astir13/SoftRF/documents/images/ForeFlight-1.jpg

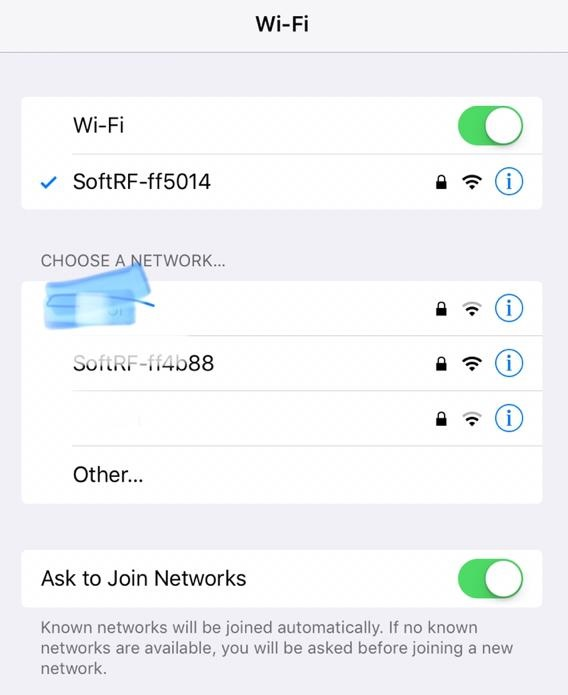
documents/images/ForeFlight-1.jpg
