astir13/SoftRF/documents/images/ForeFlight-2.jpg

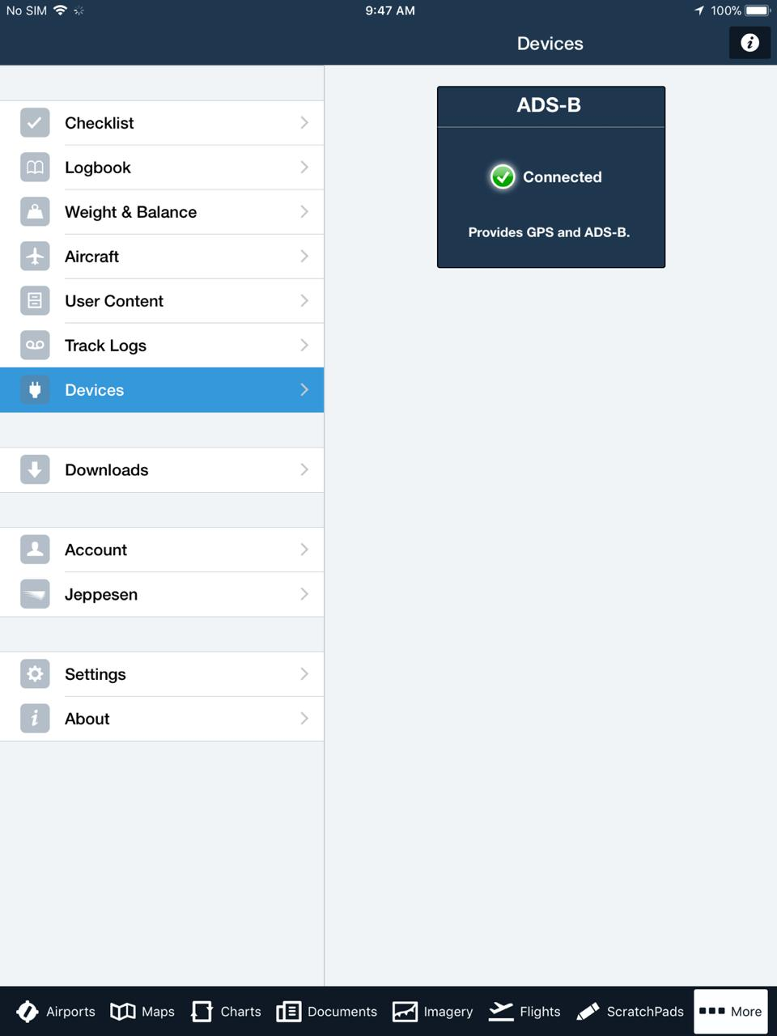
documents/images/ForeFlight-2.jpg
