astir13/SoftRF/documents/images/ForeFlight-3.jpg

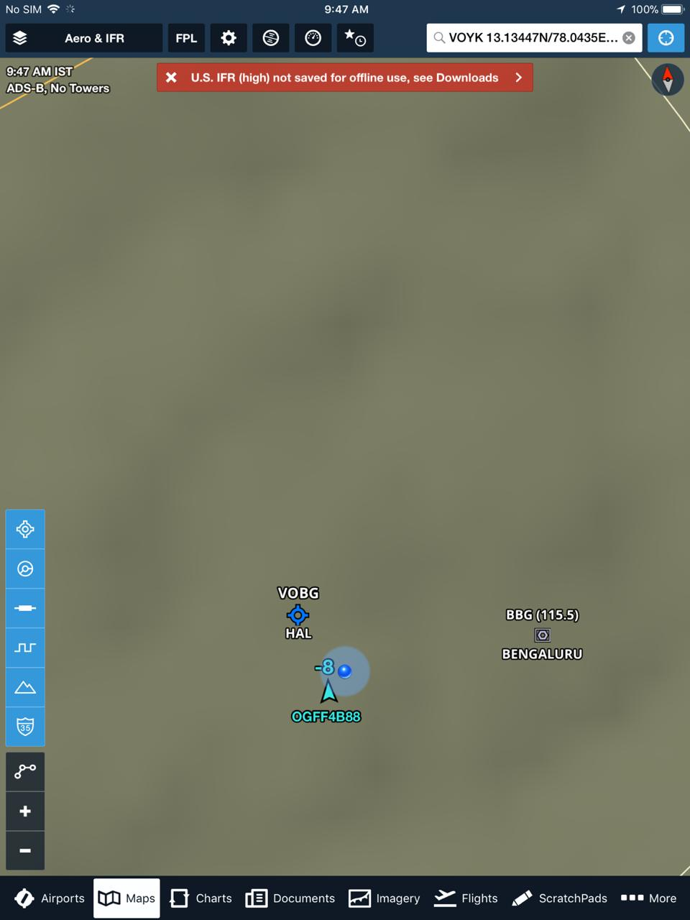
documents/images/ForeFlight-3.jpg
