astir13/SoftRF/documents/images/iLogger-boot.jpg

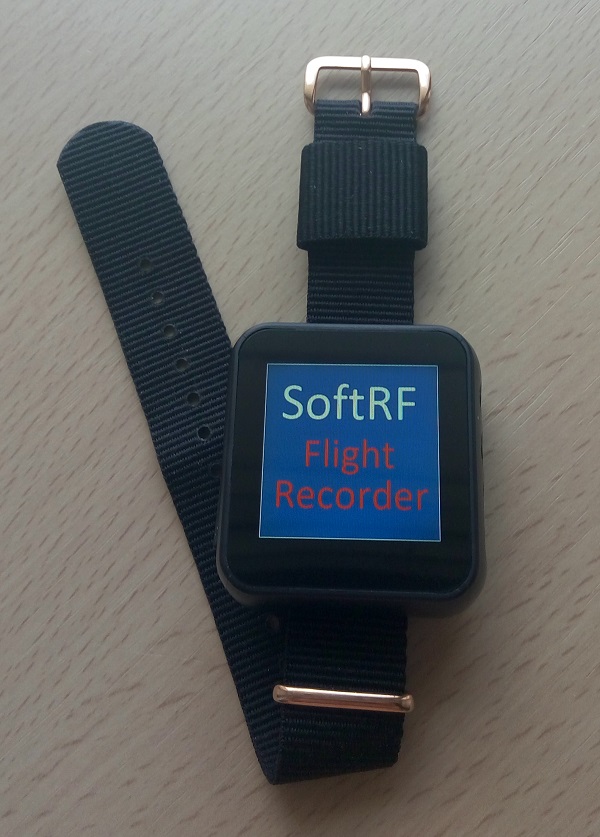
documents/images/iLogger-boot.jpg
