astir13/SoftRF/documents/images/iLogger-DIY.jpg

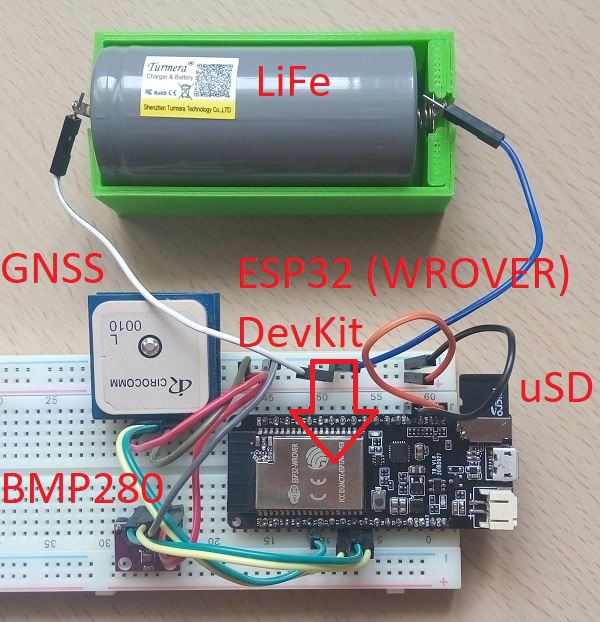
documents/images/iLogger-DIY.jpg
