astir13/SoftRF/documents/images/iLogger-flashing.jpg

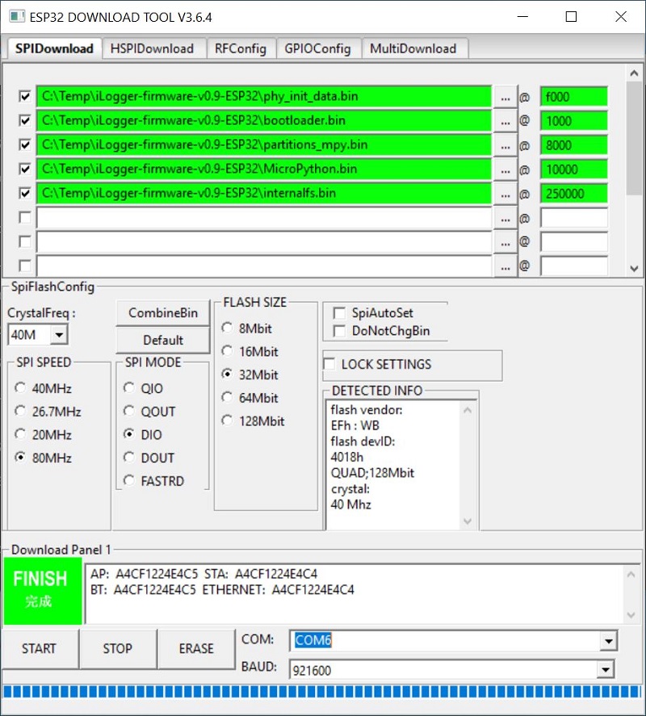
documents/images/iLogger-flashing.jpg
