astir13/SoftRF/documents/images/iLogger-I2C.jpg

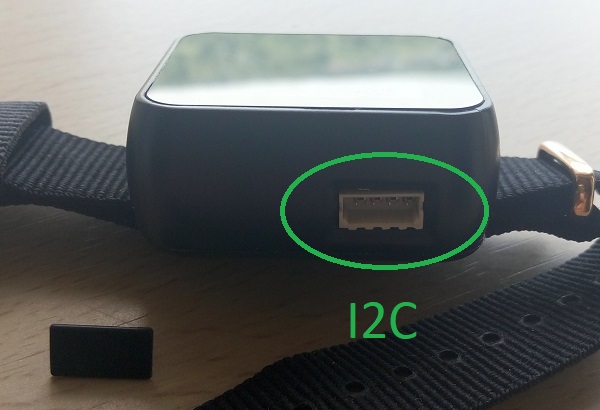
documents/images/iLogger-I2C.jpg
