astir13/SoftRF/documents/images/iLogger-nocard.jpg

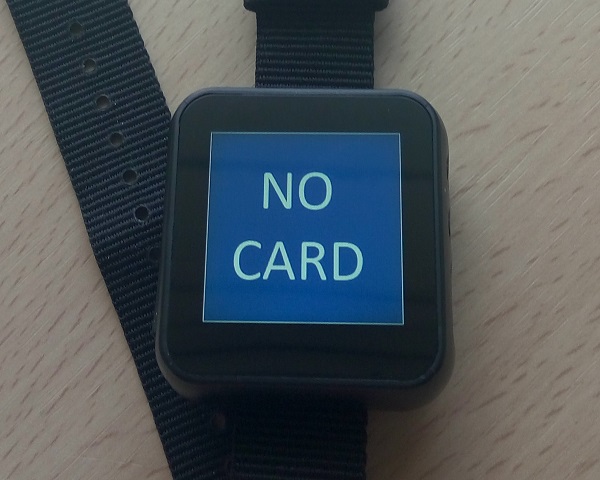
documents/images/iLogger-nocard.jpg
