astir13/SoftRF/documents/images/iLogger-nofix.jpg

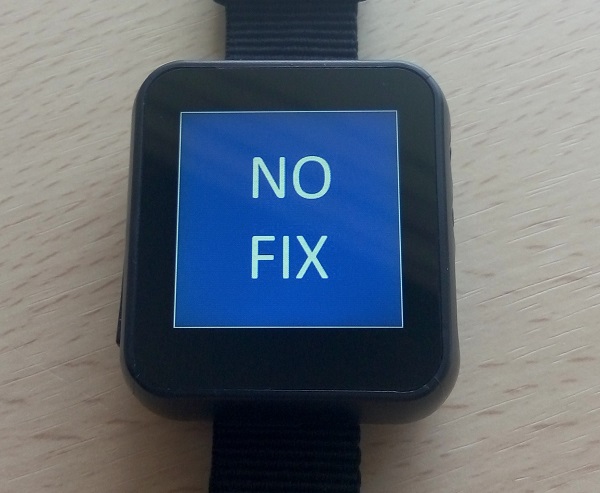
documents/images/iLogger-nofix.jpg
