astir13/SoftRF/documents/images/iLogger-off.jpg

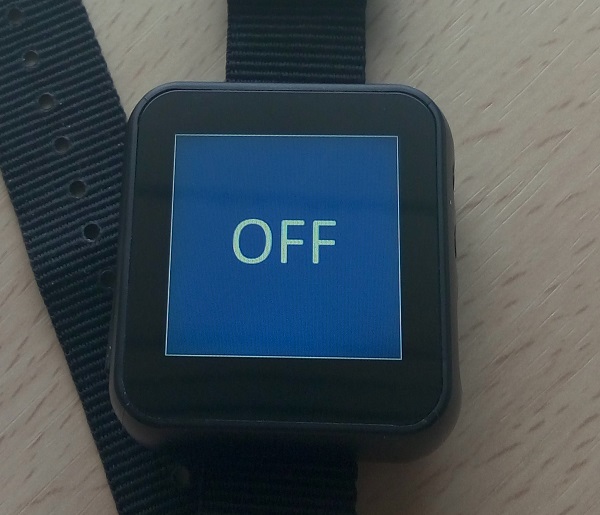
documents/images/iLogger-off.jpg
