astir13/SoftRF/documents/images/iLogger-SeeYou.JPG

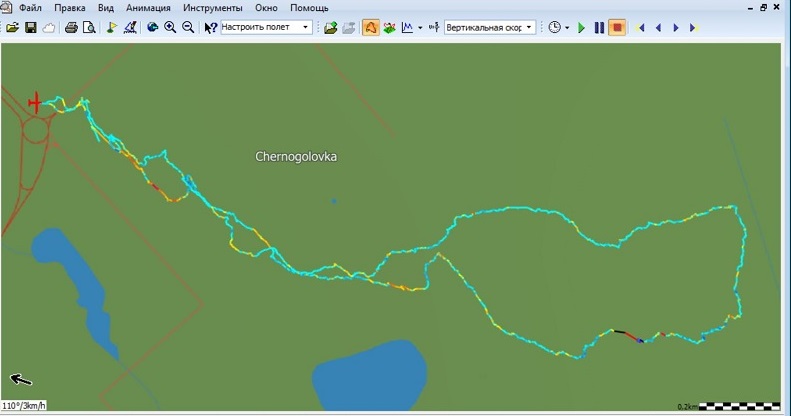
documents/images/iLogger-SeeYou.JPG
