astir13/SoftRF/documents/images/instrument-panel-1.jpg

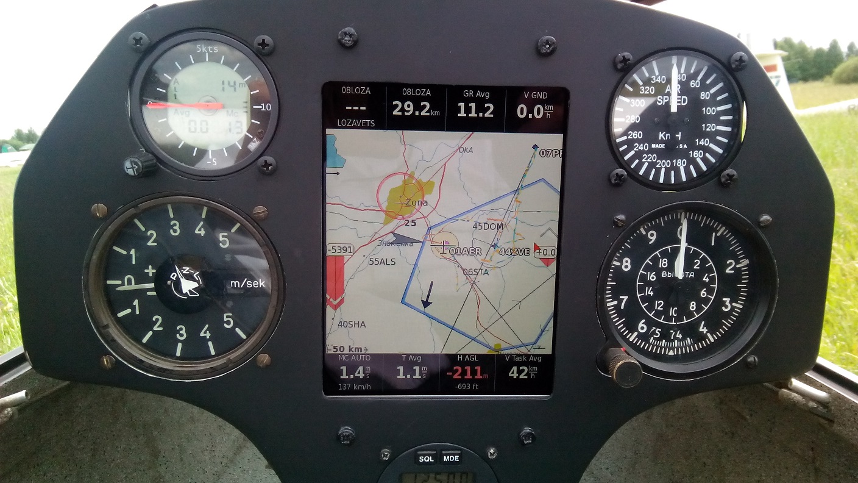
documents/images/instrument-panel-1.jpg
