astir13/SoftRF/documents/images/PE2_QS_p1.jpg

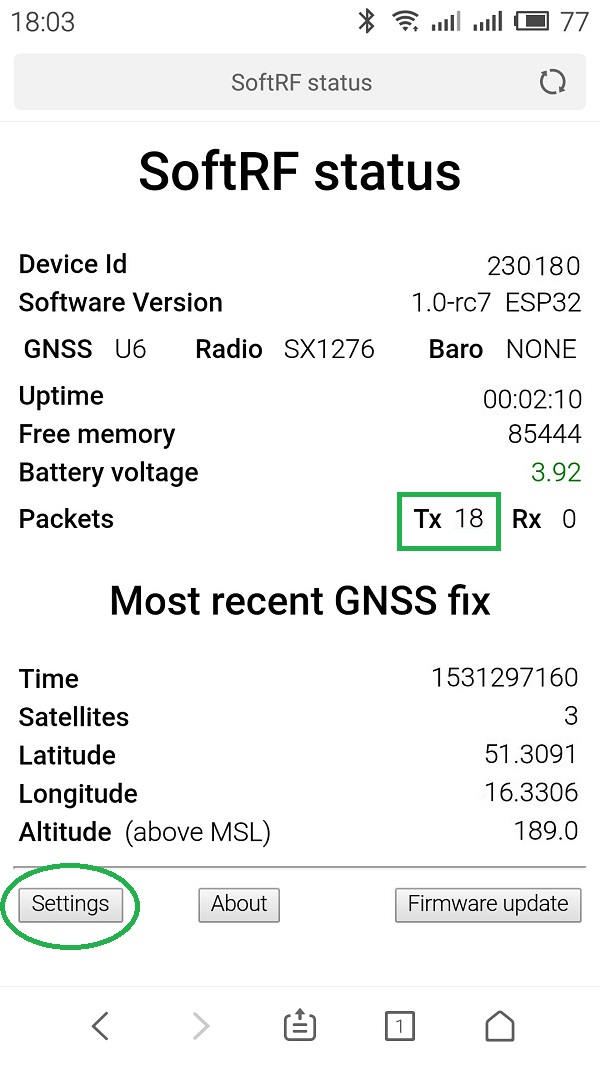
documents/images/PE2_QS_p1.jpg
