astir13/SoftRF/documents/images/PE2_QS_p2.jpg

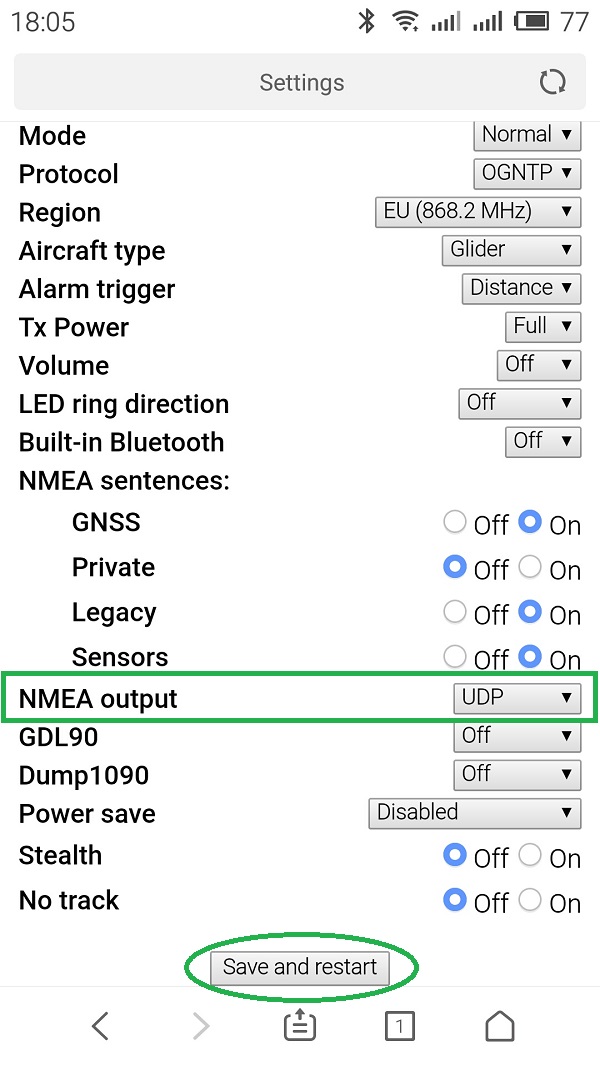
documents/images/PE2_QS_p2.jpg
