astir13/SoftRF/documents/images/Prime2_T22_V10_1.jpg

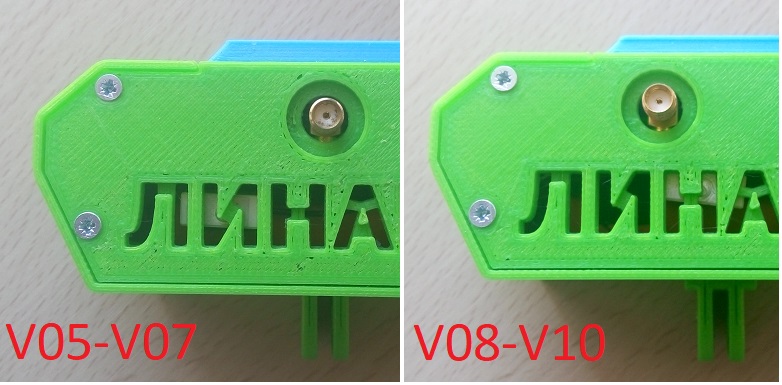
documents/images/Prime2_T22_V10_1.jpg
