astir13/SoftRF/documents/images/RPI_SPI.jpg

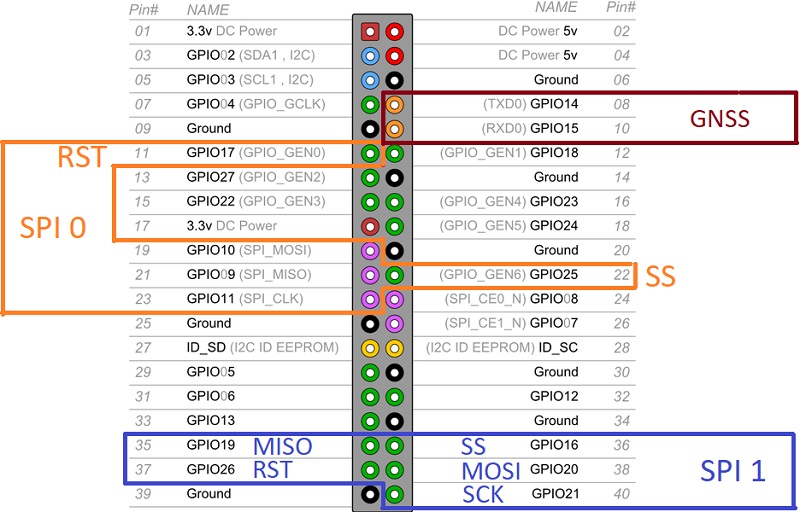
documents/images/RPI_SPI.jpg
