astir13/SoftRF/documents/images/skyview-1-t5s.jpg

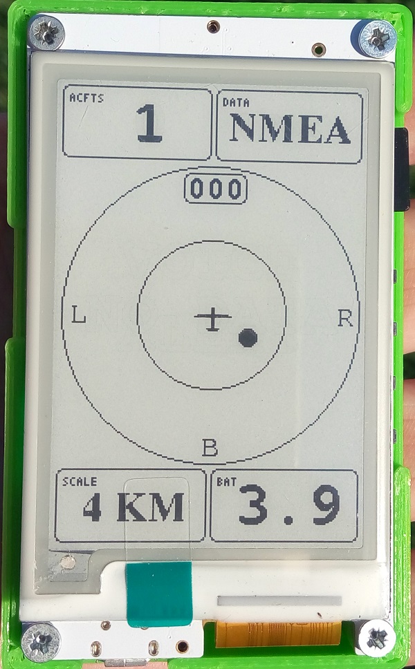
documents/images/skyview-1-t5s.jpg
