astir13/SoftRF/documents/images/skyview-1.jpg

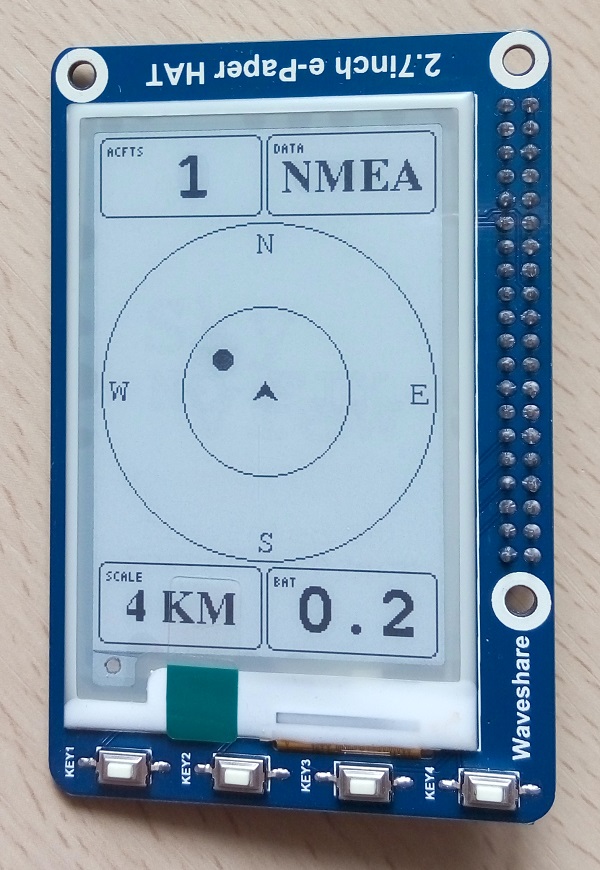
documents/images/skyview-1.jpg
