astir13/SoftRF/documents/images/skyview-2.jpg

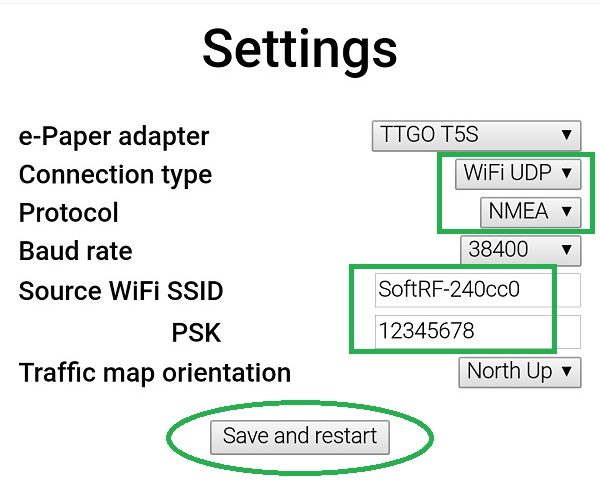
documents/images/skyview-2.jpg
