astir13/SoftRF/documents/images/skyview-3-t5s.jpg

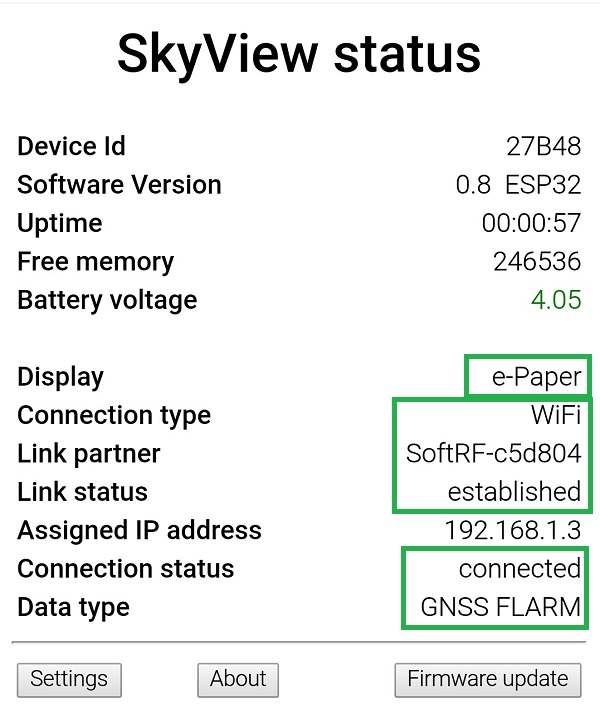
documents/images/skyview-3-t5s.jpg
