astir13/SoftRF/documents/images/skyview-3.jpg

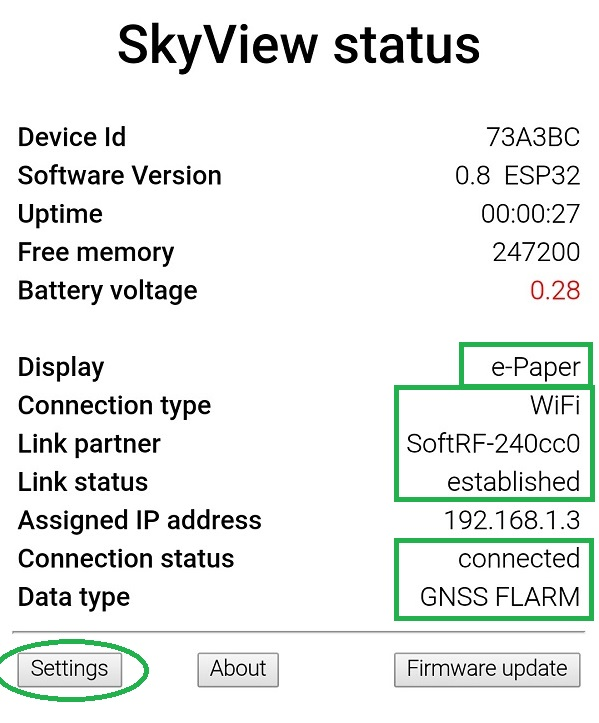
documents/images/skyview-3.jpg
