astir13/SoftRF/documents/images/skyview-4.jpg

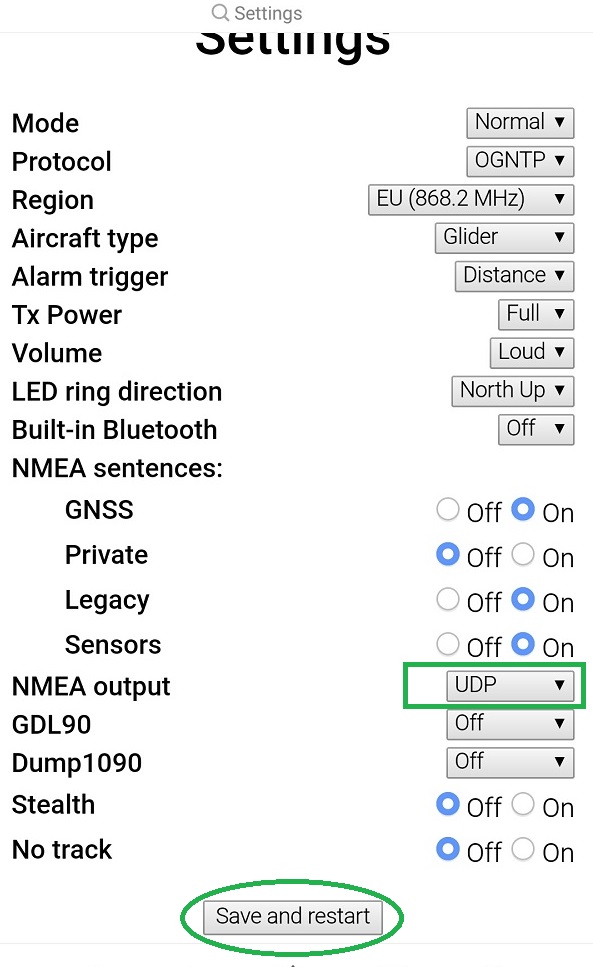
documents/images/skyview-4.jpg
