astir13/SoftRF/documents/images/skyview-5-t5s.jpg

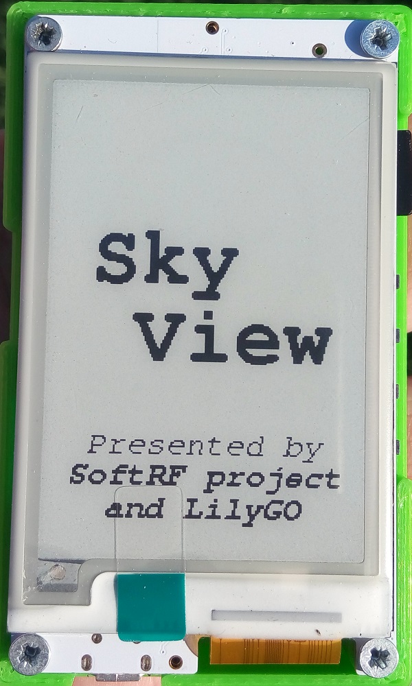
documents/images/skyview-5-t5s.jpg
