astir13/SoftRF/documents/images/skyview-5.jpg

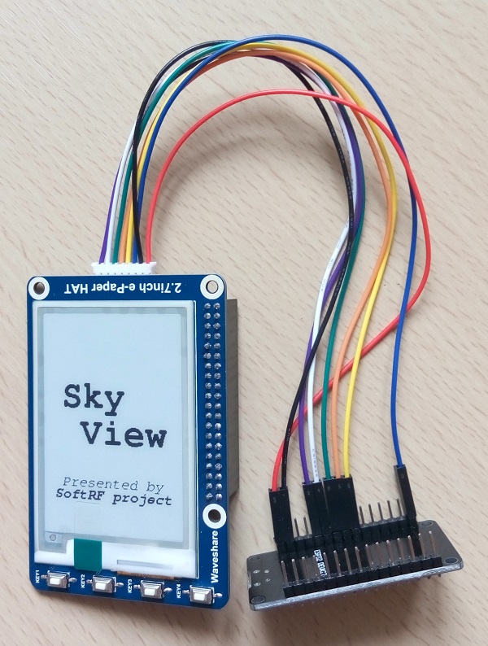
documents/images/skyview-5.jpg
