astir13/SoftRF/documents/images/skyview-7-no-traffic-t5s.jpg

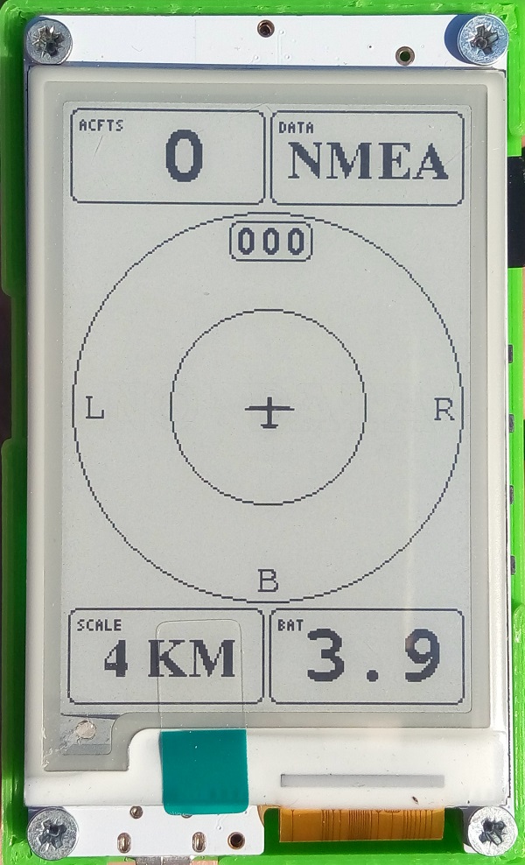
documents/images/skyview-7-no-traffic-t5s.jpg
