astir13/SoftRF/documents/images/skyview-8-no-data-t5s.jpg

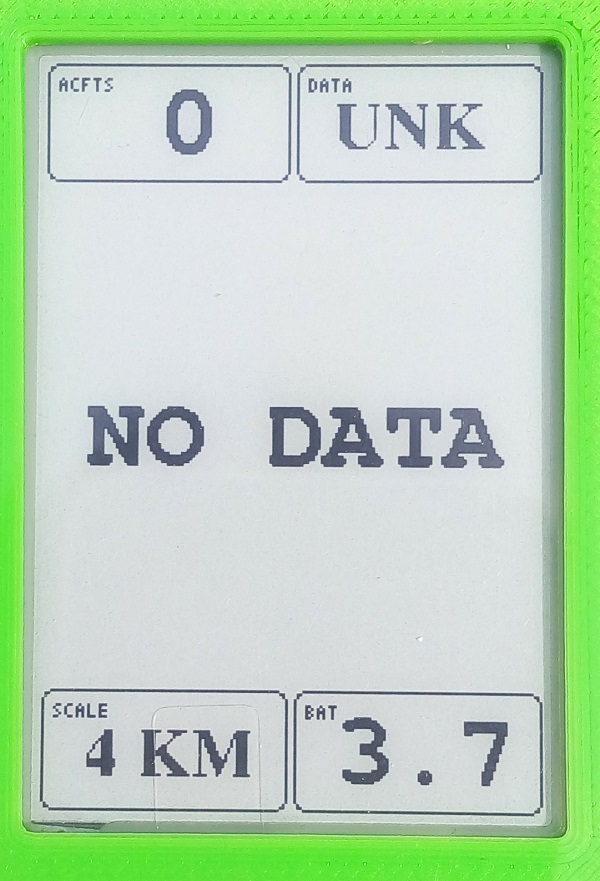
documents/images/skyview-8-no-data-t5s.jpg
