astir13/SoftRF/documents/images/skyview-8-no-data.jpg

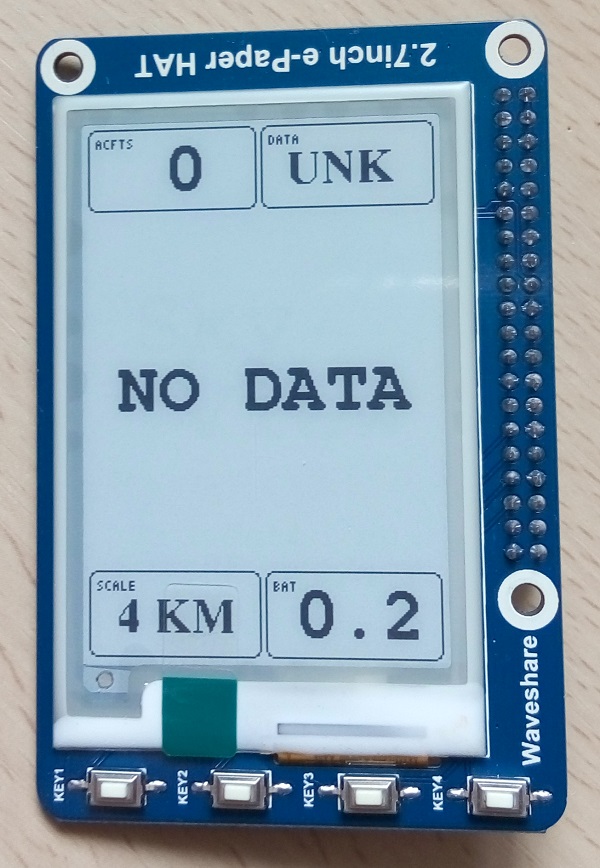
documents/images/skyview-8-no-data.jpg
