astir13/SoftRF/documents/images/skyview-9.JPG

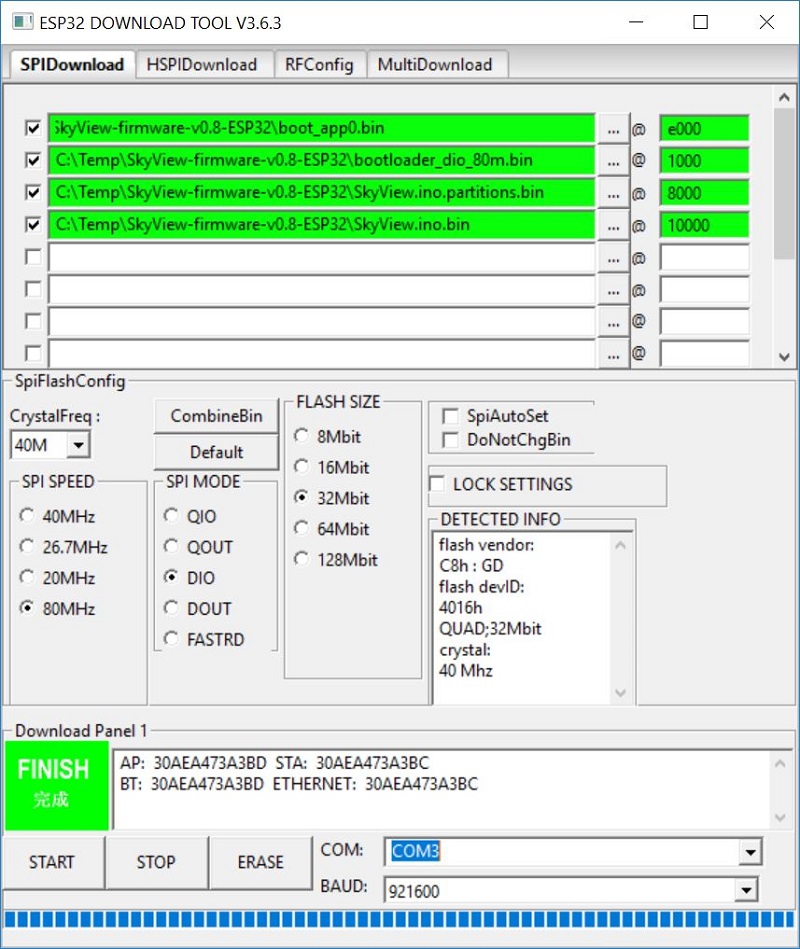
documents/images/skyview-9.JPG
