astir13/SoftRF/documents/images/skyview-10.jpg

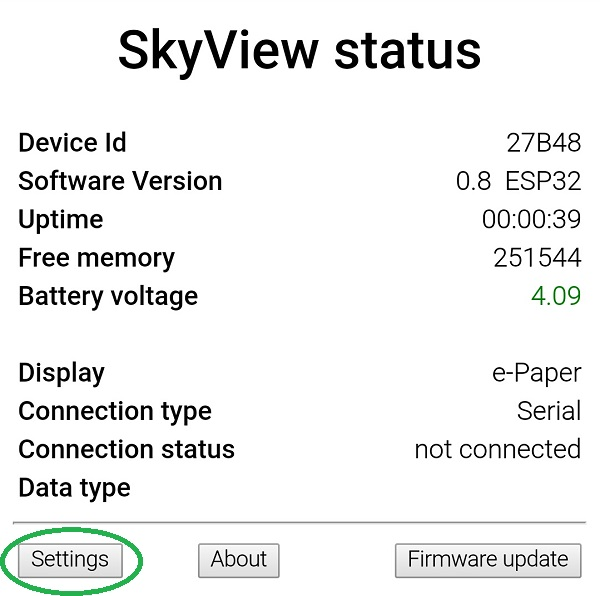
documents/images/skyview-10.jpg
