astir13/SoftRF/documents/images/skyview-12.jpg

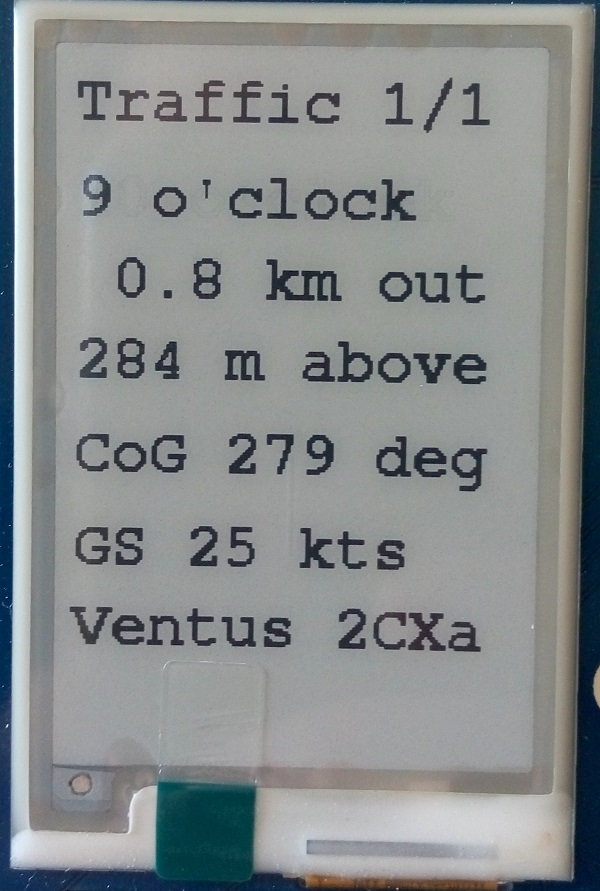
documents/images/skyview-12.jpg
