astir13/SoftRF/documents/images/skyview-14.jpg

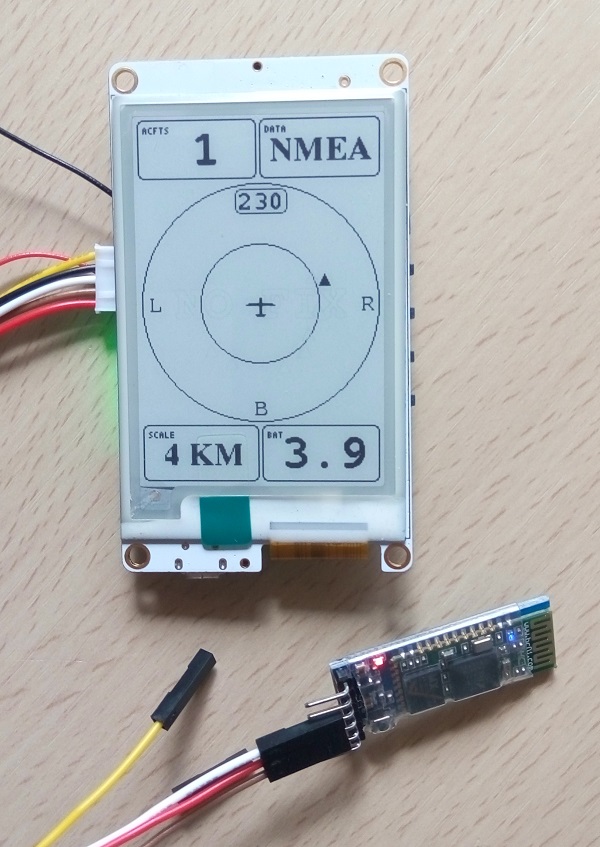
documents/images/skyview-14.jpg
