astir13/SoftRF/documents/images/skyview-15.JPG

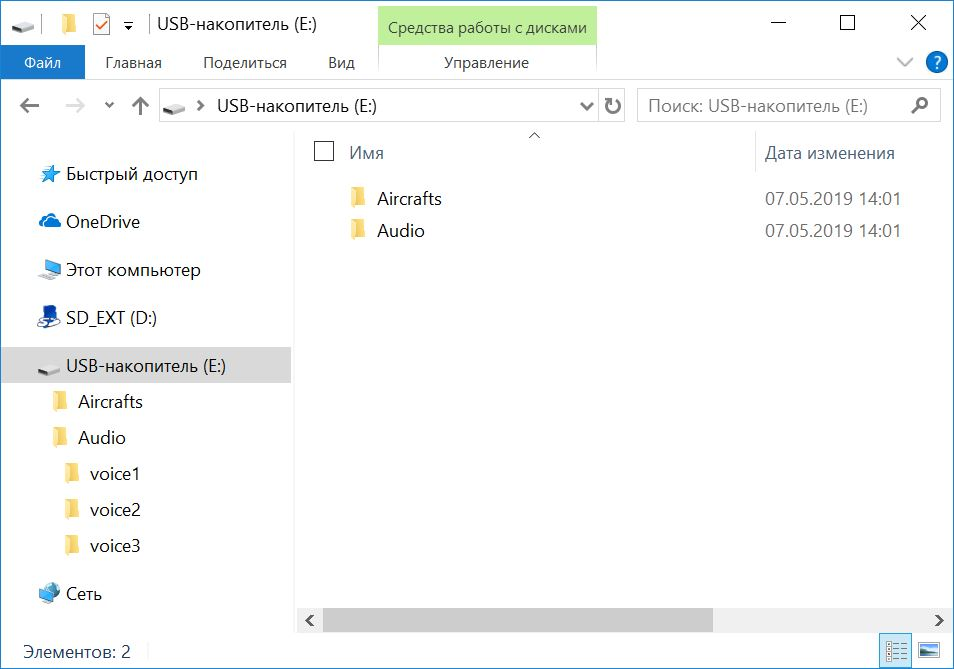
documents/images/skyview-15.JPG
