astir13/SoftRF/documents/images/skyview-16-ePaper-vs-OLED.jpg

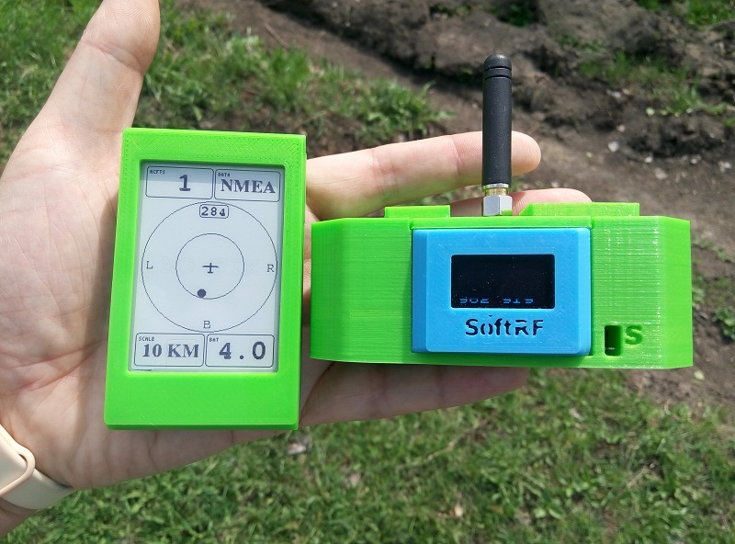
documents/images/skyview-16-ePaper-vs-OLED.jpg
