astir13/SoftRF/documents/images/skyview-17.jpg

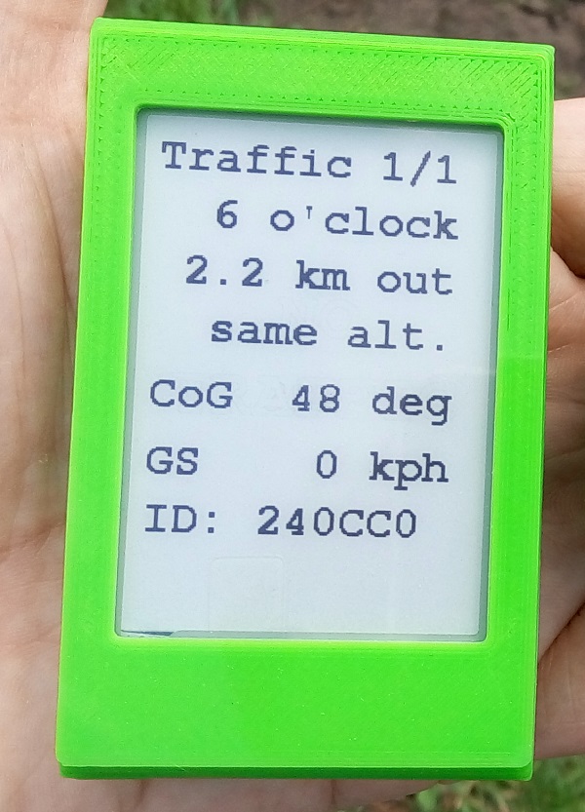
documents/images/skyview-17.jpg
