astir13/SoftRF/documents/images/skyview-18.jpg

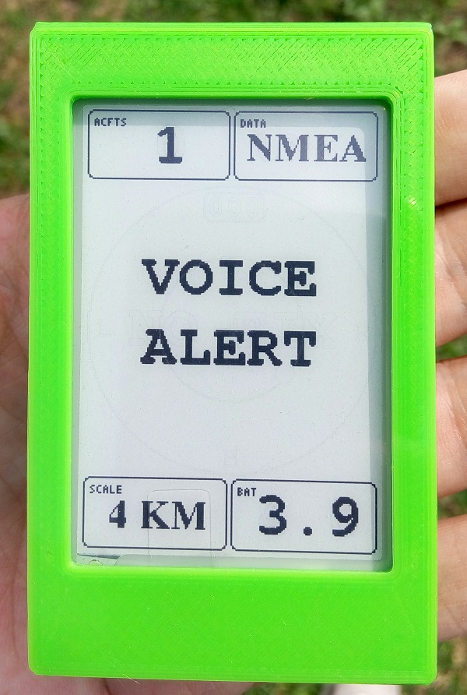
documents/images/skyview-18.jpg
