astir13/SoftRF/documents/images/skyview-19-buttons.jpg

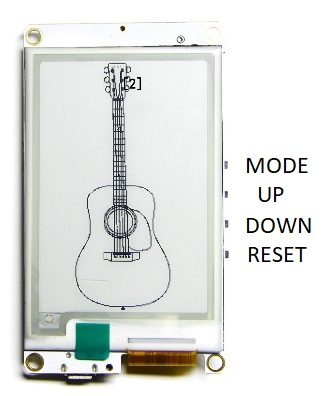
documents/images/skyview-19-buttons.jpg
