astir13/SoftRF/documents/images/skyview-20-serial.jpg

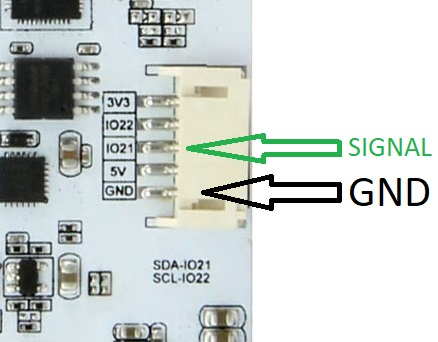
documents/images/skyview-20-serial.jpg
