astir13/SoftRF/documents/images/skyview-21-speaker.jpg

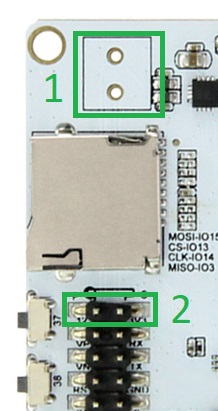
documents/images/skyview-21-speaker.jpg
