astir13/SoftRF/documents/images/skyview-22-enclosure.jpg

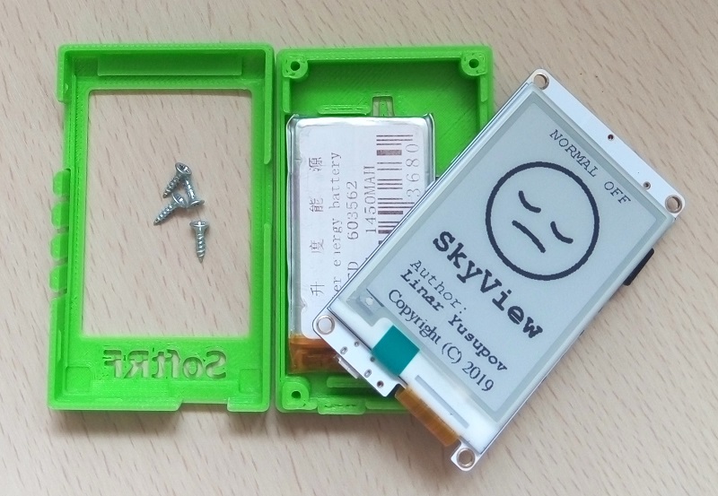
documents/images/skyview-22-enclosure.jpg
