astir13/SoftRF/documents/images/skyview-23-enclosure.jpg

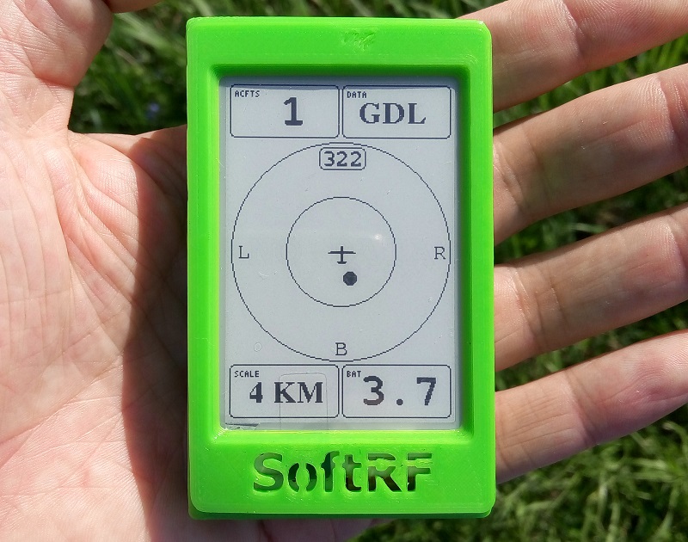
documents/images/skyview-23-enclosure.jpg
