astir13/SoftRF/documents/images/skyview-24.jpg

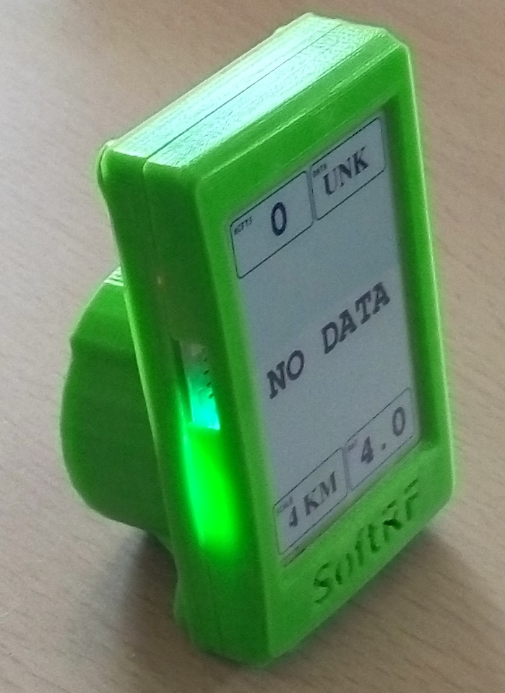
documents/images/skyview-24.jpg
