astir13/SoftRF/documents/images/skyview-25.jpg

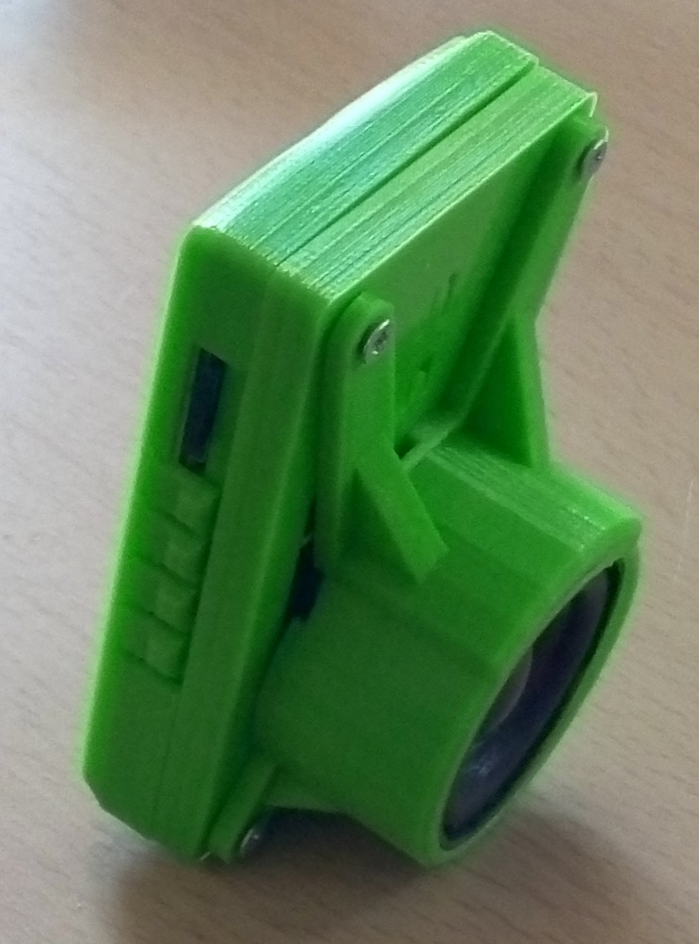
documents/images/skyview-25.jpg
