astir13/SoftRF/documents/images/skyview-26.jpg

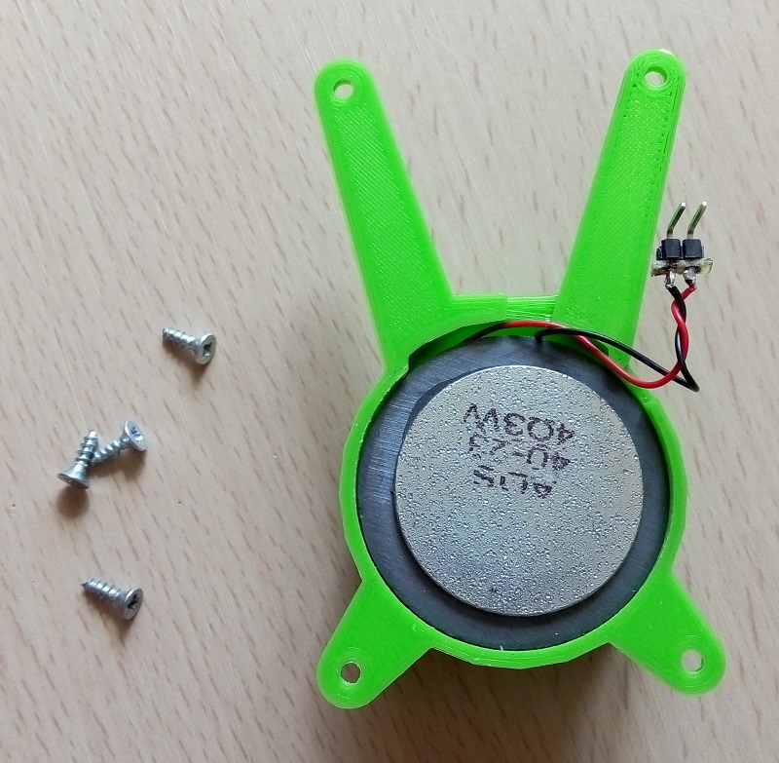
documents/images/skyview-26.jpg
