astir13/SoftRF/documents/images/skyview-27-holder.jpg

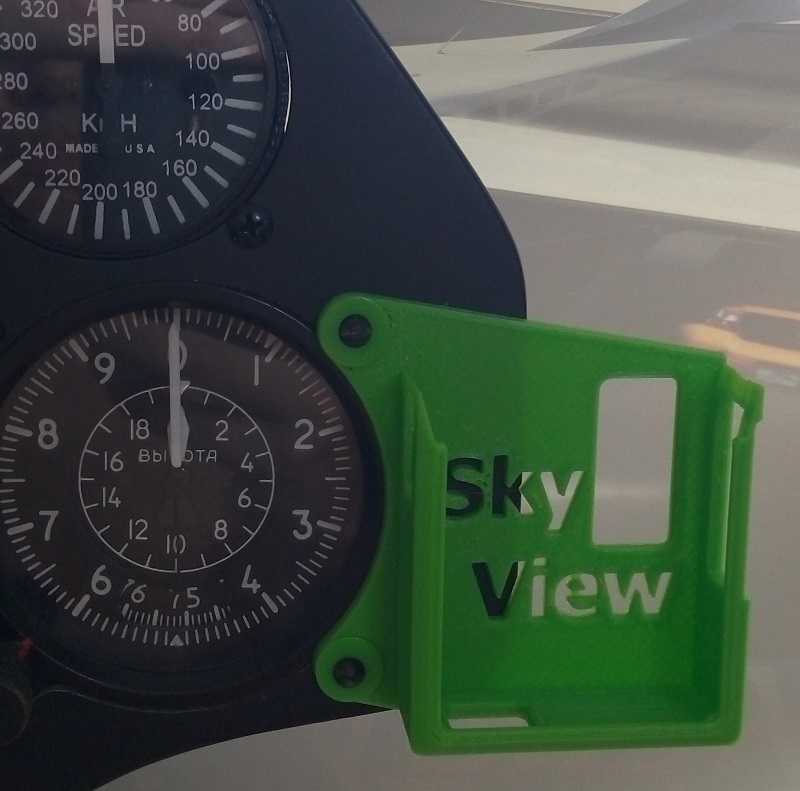
documents/images/skyview-27-holder.jpg
