astir13/SoftRF/documents/images/skyview-28.jpg

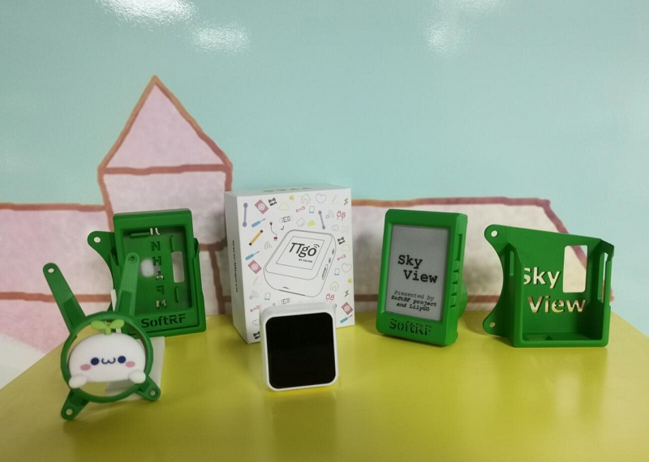
documents/images/skyview-28.jpg
