astir13/SoftRF/documents/images/skyview-29-holder.jpg

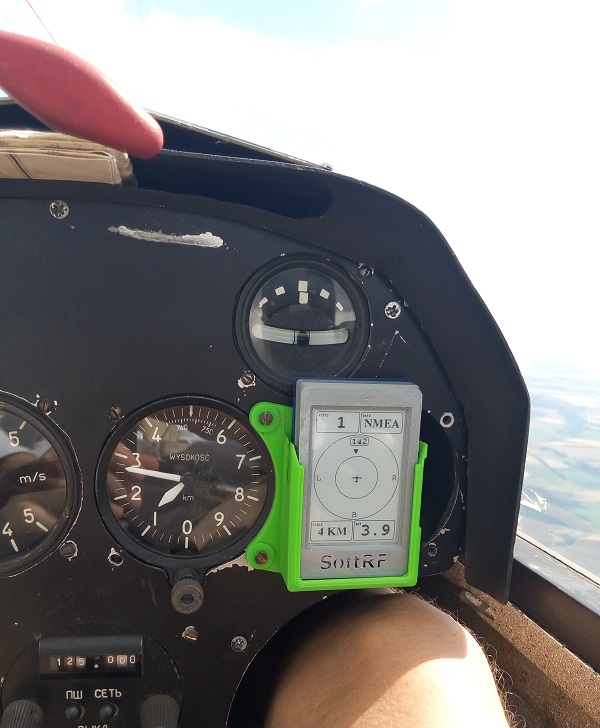
documents/images/skyview-29-holder.jpg
