astir13/SoftRF/documents/images/skyview-30-distance.jpg

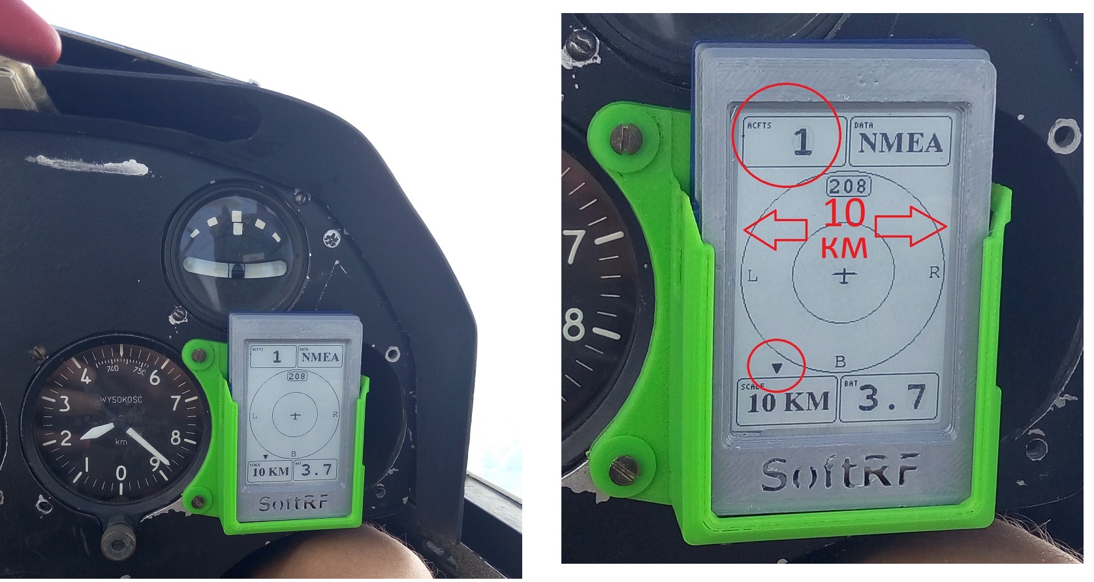
documents/images/skyview-30-distance.jpg
