astir13/SoftRF/documents/images/skyview-34.jpg

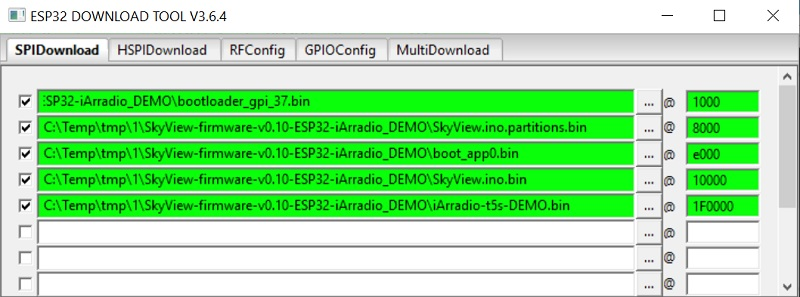
documents/images/skyview-34.jpg
