astir13/SoftRF/documents/images/skywatch-2.jpg

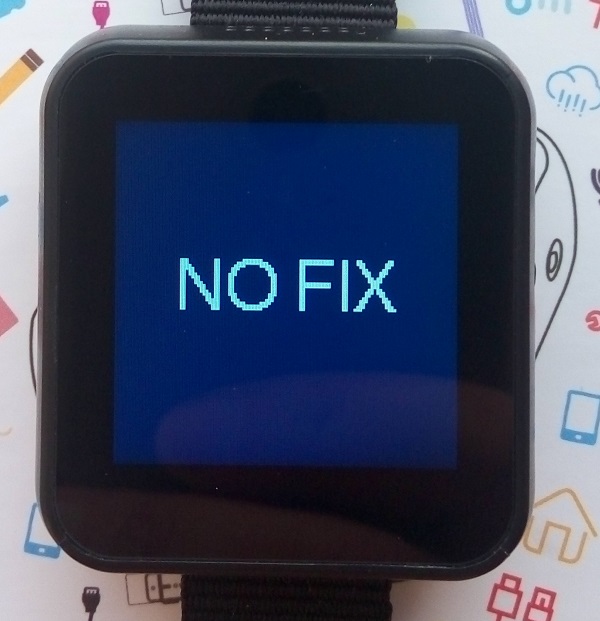
documents/images/skywatch-2.jpg
