astir13/SoftRF/documents/images/skywatch-3.jpg

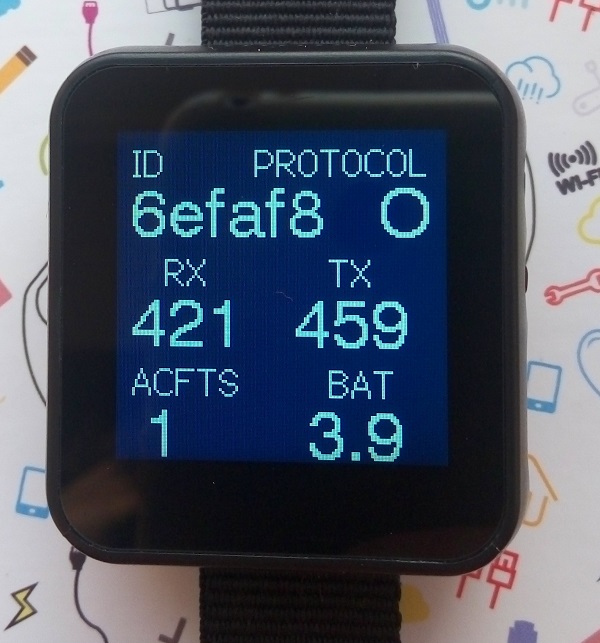
documents/images/skywatch-3.jpg
