astir13/SoftRF/documents/images/skywatch-5.jpg

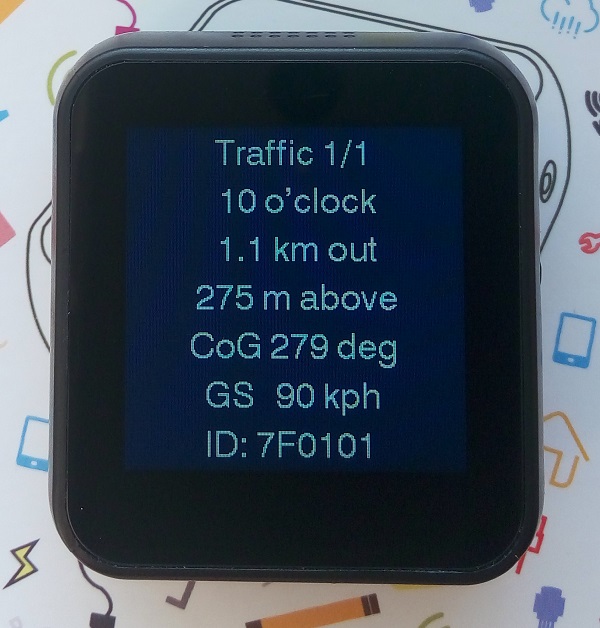
documents/images/skywatch-5.jpg
