astir13/SoftRF/documents/images/skywatch-6.jpg

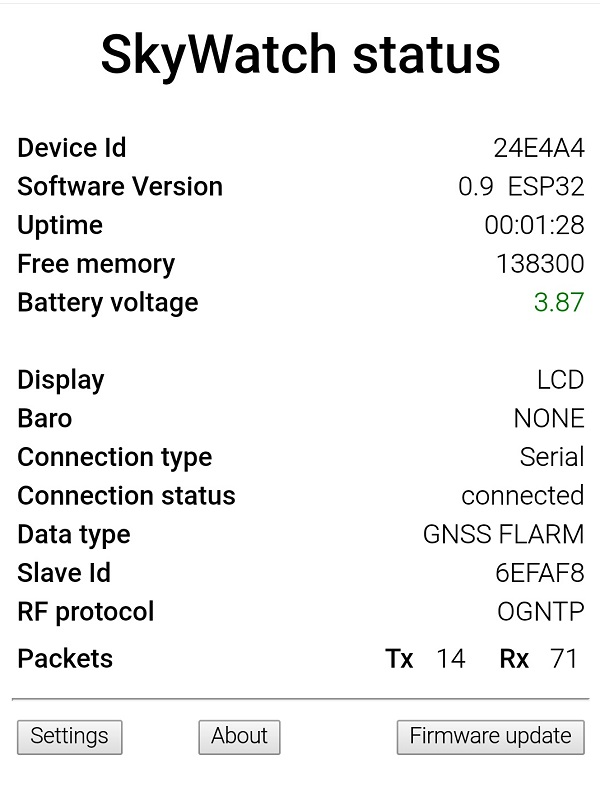
documents/images/skywatch-6.jpg
