astir13/SoftRF/documents/images/SoftRF-UAT-1.jpg

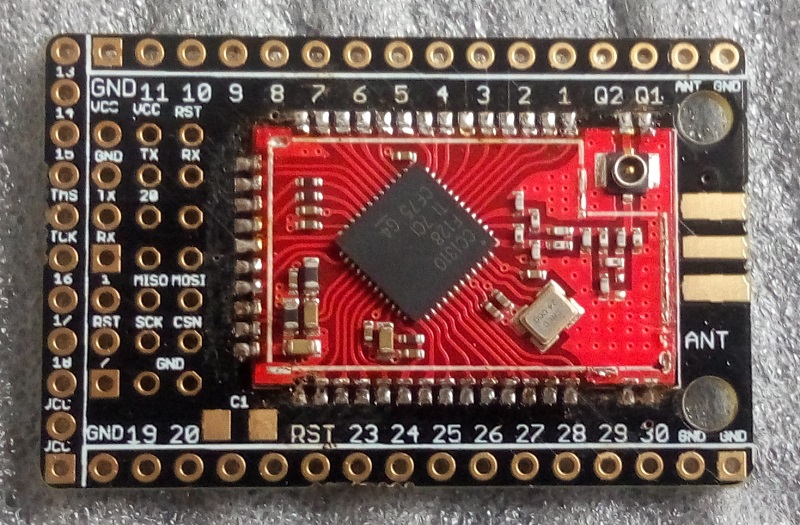
documents/images/SoftRF-UAT-1.jpg
