astir13/SoftRF/documents/images/stm32_breadboard.jpg

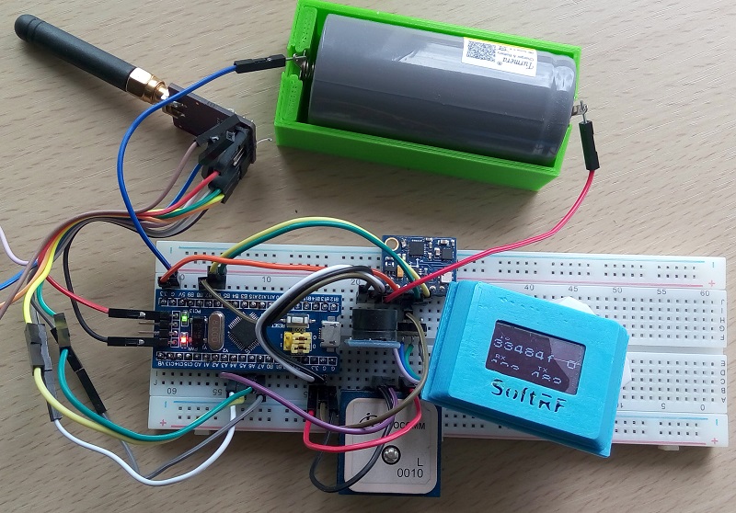
documents/images/stm32_breadboard.jpg
