astir13/SoftRF/documents/images/stm32_rfm69.jpg

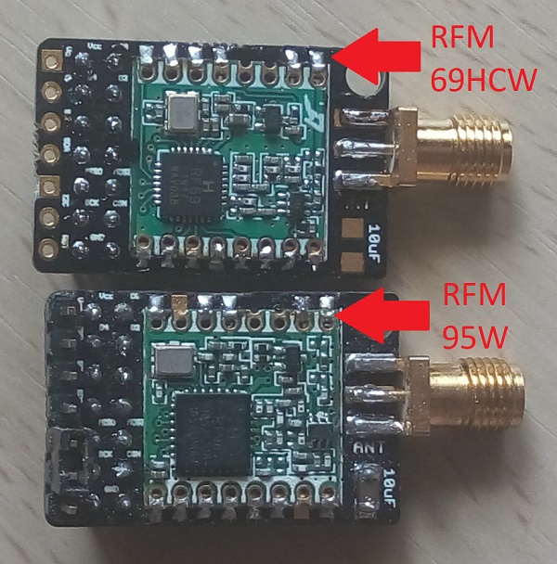
documents/images/stm32_rfm69.jpg
