astir13/SoftRF/documents/images/t-motion-7.jpg

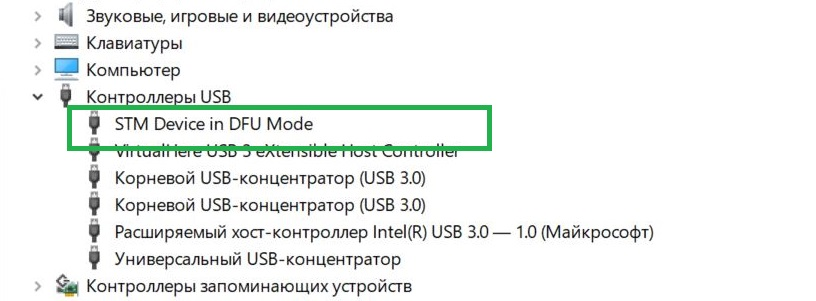
documents/images/t-motion-7.jpg
