astir13/SoftRF/documents/images/t-motion-10.jpg

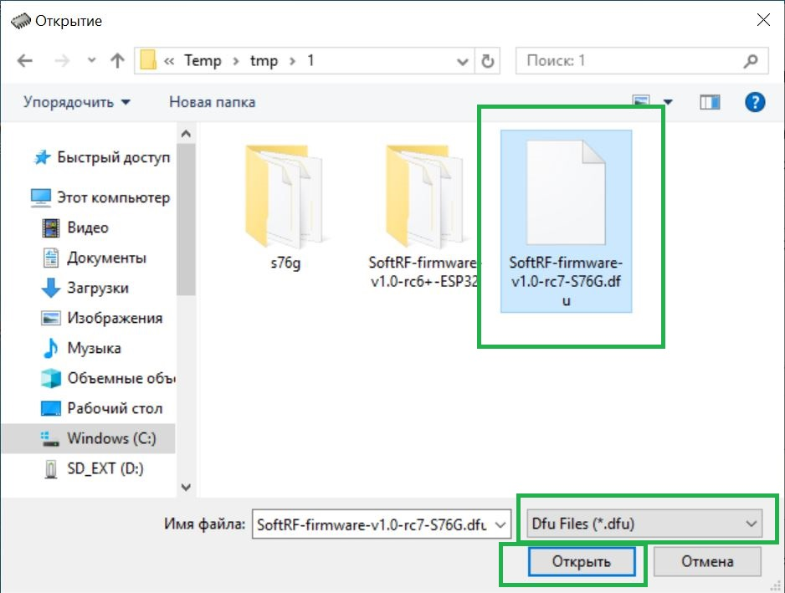
documents/images/t-motion-10.jpg
