astir13/SoftRF/documents/images/t-motion-12.jpg

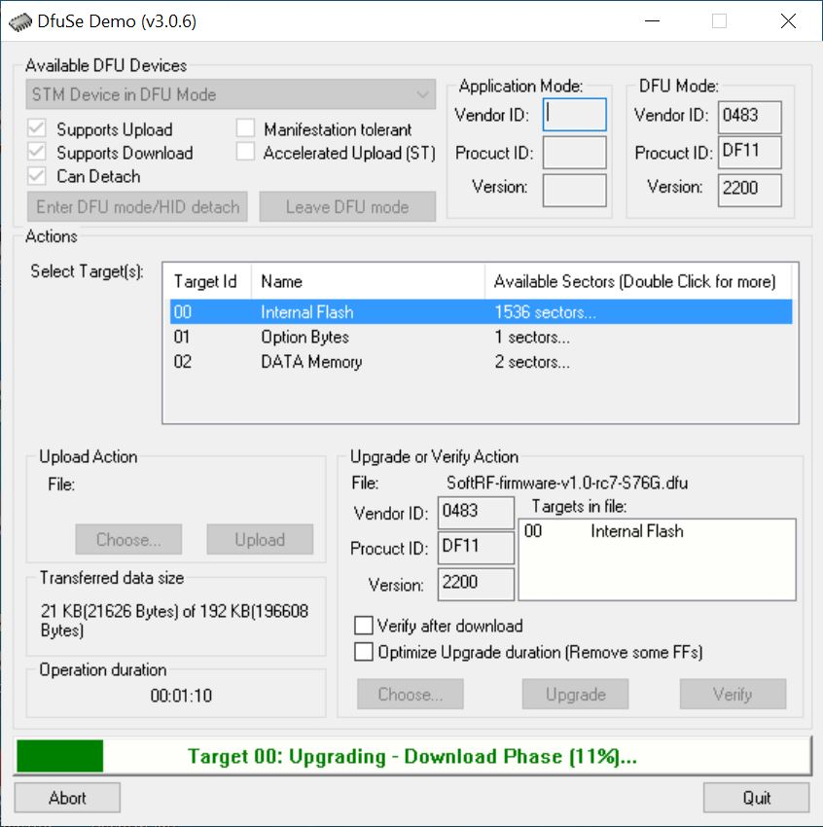
documents/images/t-motion-12.jpg
