astir13/SoftRF/documents/images/t-motion-13.jpg

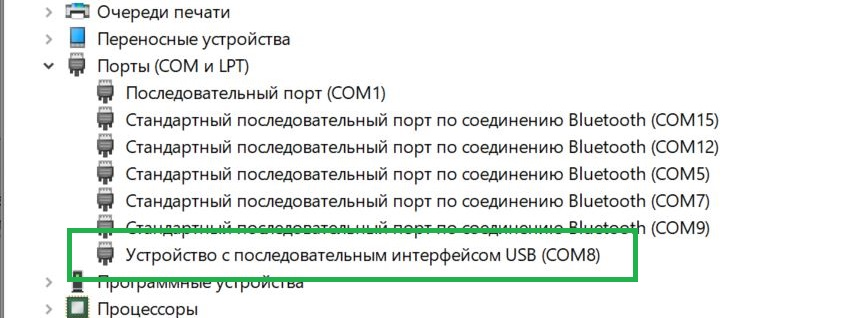
documents/images/t-motion-13.jpg
