astir13/SoftRF/documents/images/t-motion-14.jpg

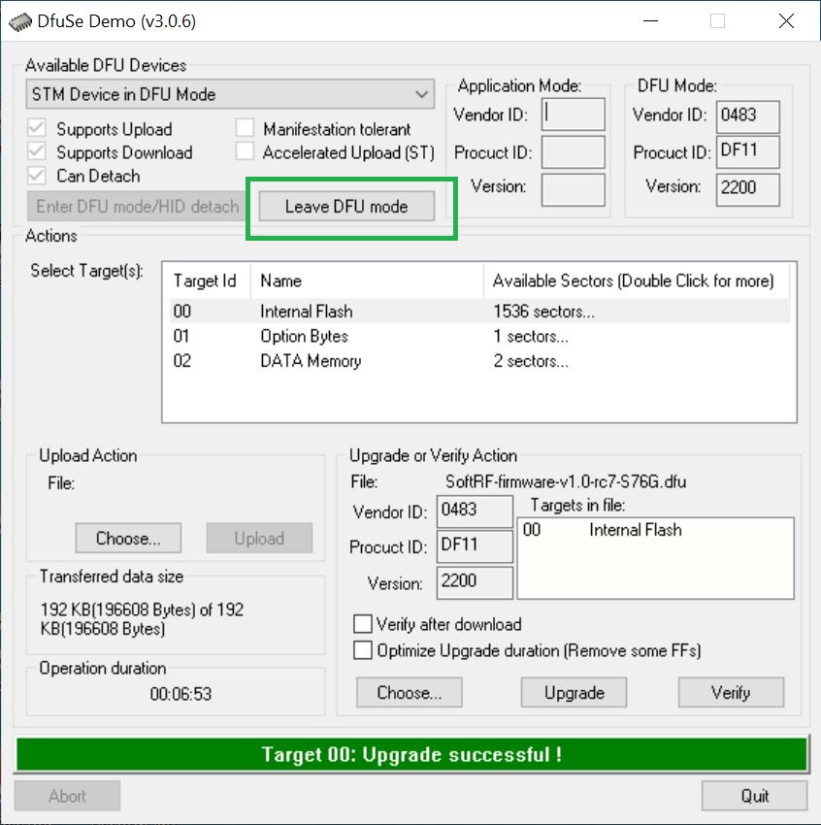
documents/images/t-motion-14.jpg
