astir13/SoftRF/documents/images/t-motion-16.jpg

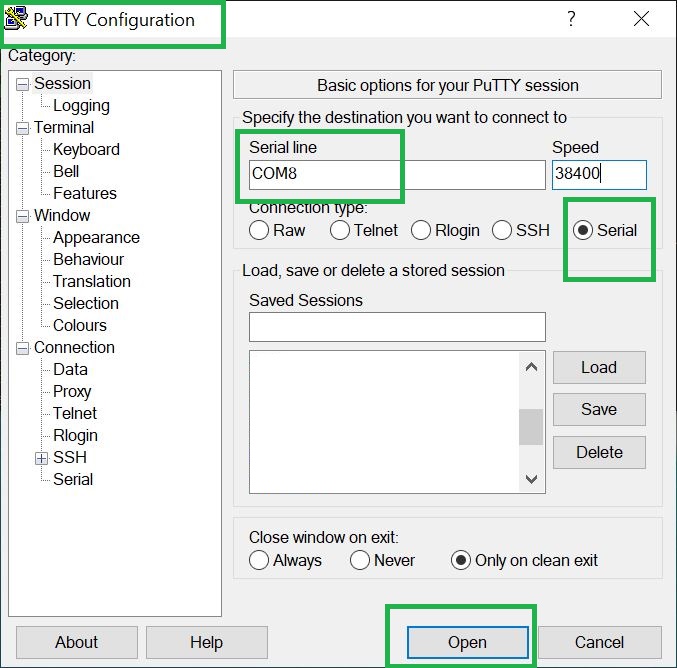
documents/images/t-motion-16.jpg
