astir13/SoftRF/documents/images/t-motion-17.jpg

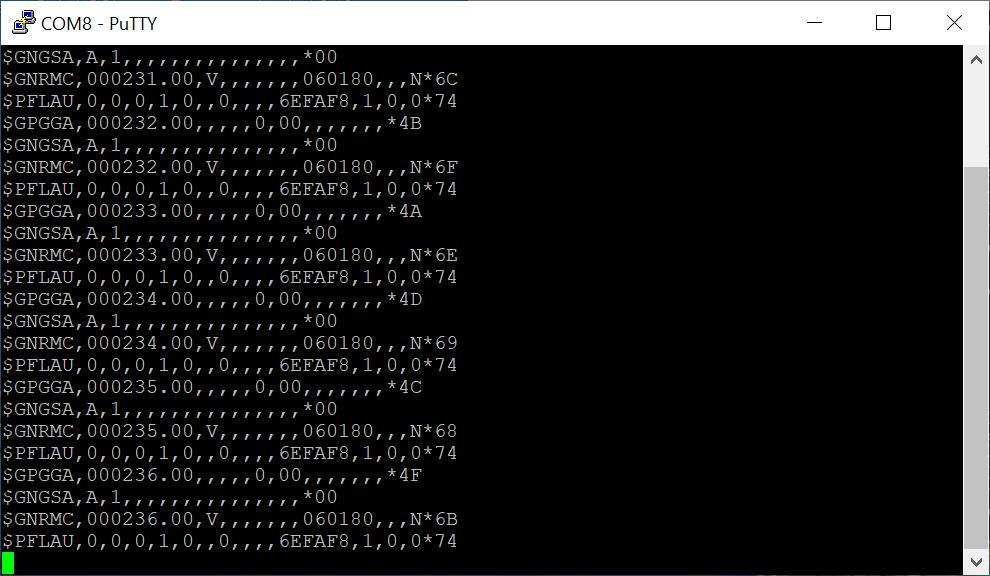
documents/images/t-motion-17.jpg
