astir13/SoftRF/documents/images/t-motion-18.jpg

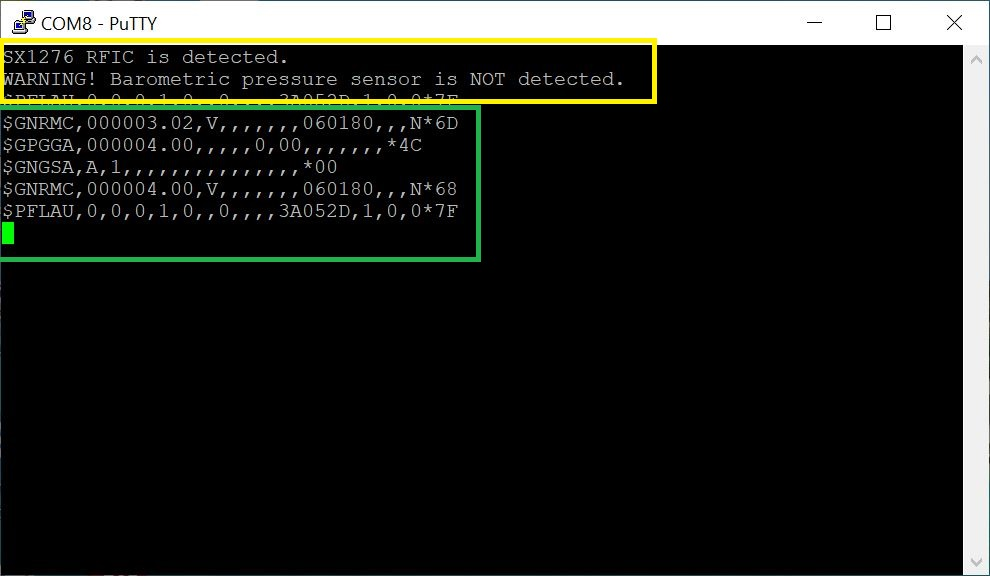
documents/images/t-motion-18.jpg
