astir13/SoftRF/documents/images/t-motion-20.jpg

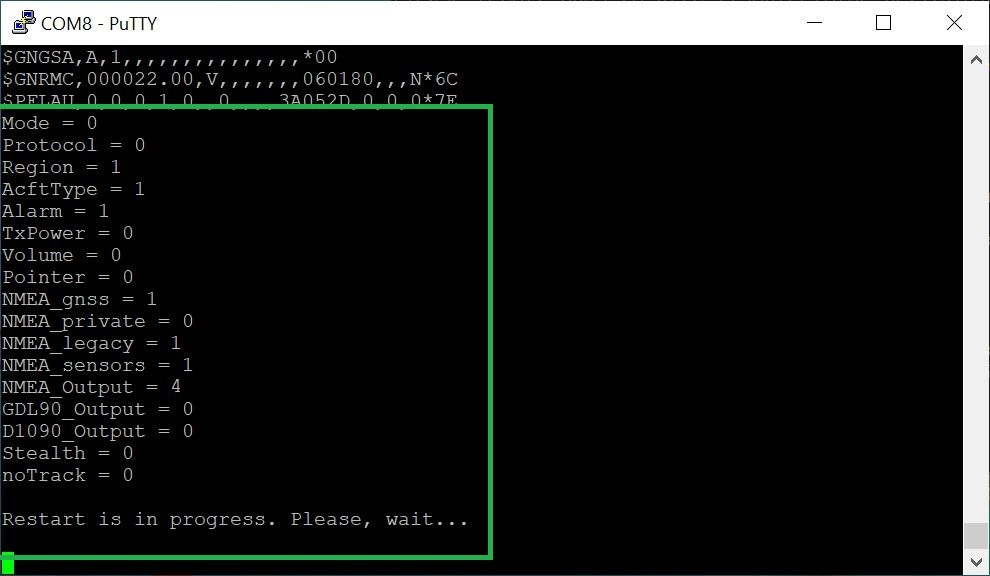
documents/images/t-motion-20.jpg
