astir13/SoftRF/documents/images/t-motion-21.jpg

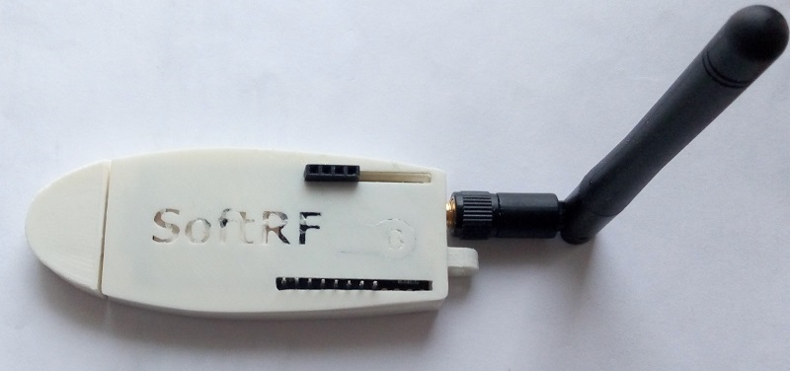
documents/images/t-motion-21.jpg
