astir13/SoftRF/documents/images/t-motion-22.jpg

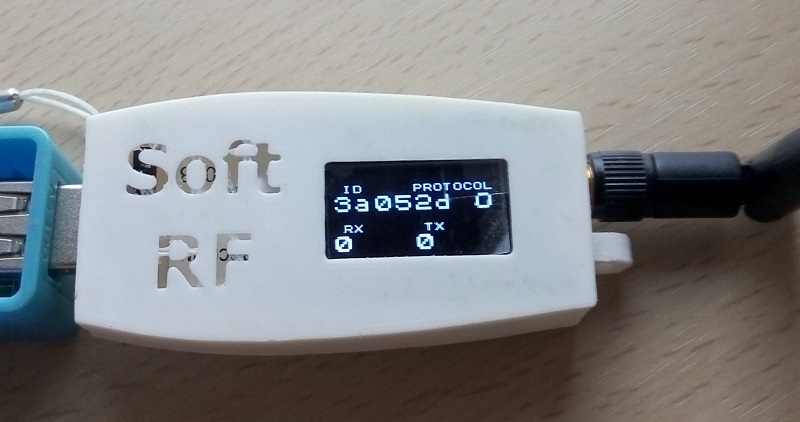
documents/images/t-motion-22.jpg
