astir13/SoftRF/documents/images/t-motion-23.jpg

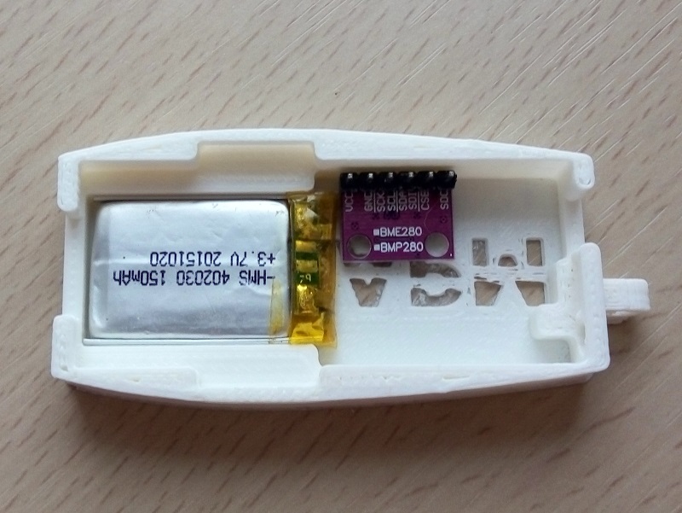
documents/images/t-motion-23.jpg
