astir13/SoftRF/documents/images/t-motion-24.jpg

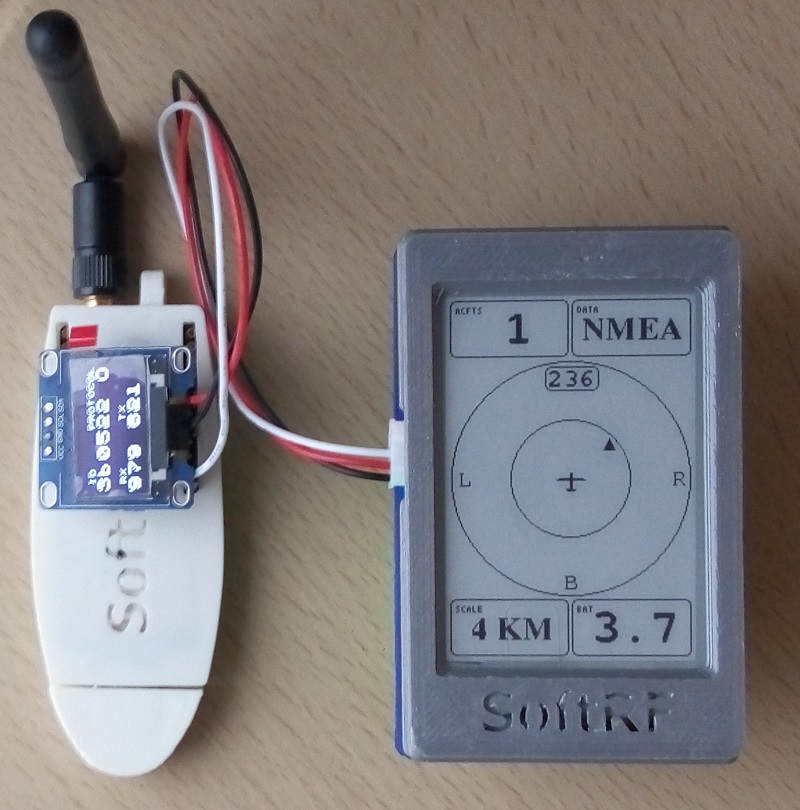
documents/images/t-motion-24.jpg
