astir13/SoftRF/documents/images/t-motion-25.jpg

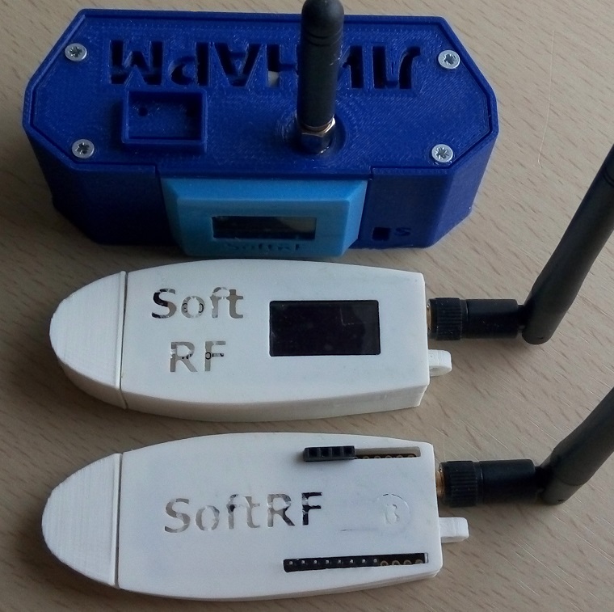
documents/images/t-motion-25.jpg
