astir13/SoftRF/documents/images/t-motion-26.jpg

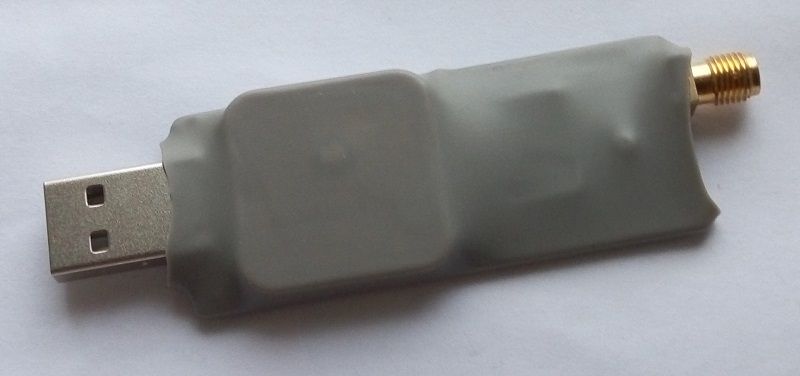
documents/images/t-motion-26.jpg
