astir13/SoftRF/documents/images/t-motion-28.jpg

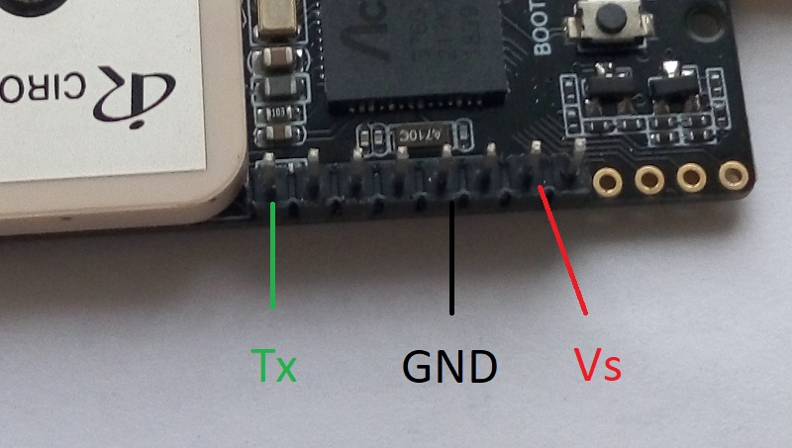
documents/images/t-motion-28.jpg
