astir13/SoftRF/documents/images/t-motion-33.jpg

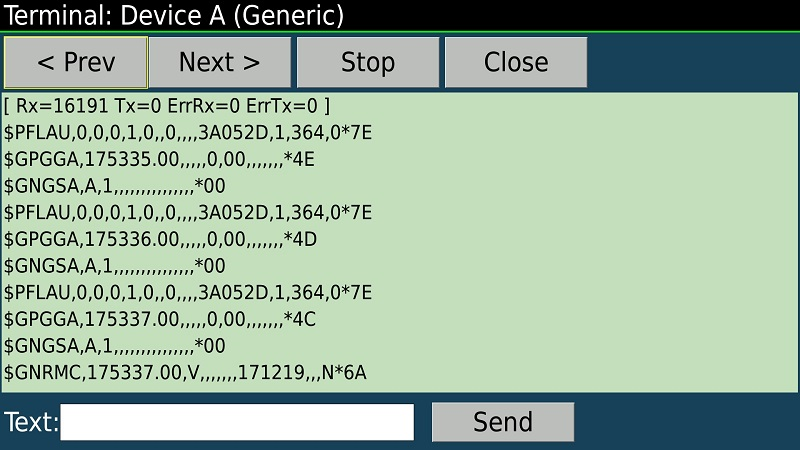
documents/images/t-motion-33.jpg
