astir13/SoftRF/documents/images/t-motion-35.jpg

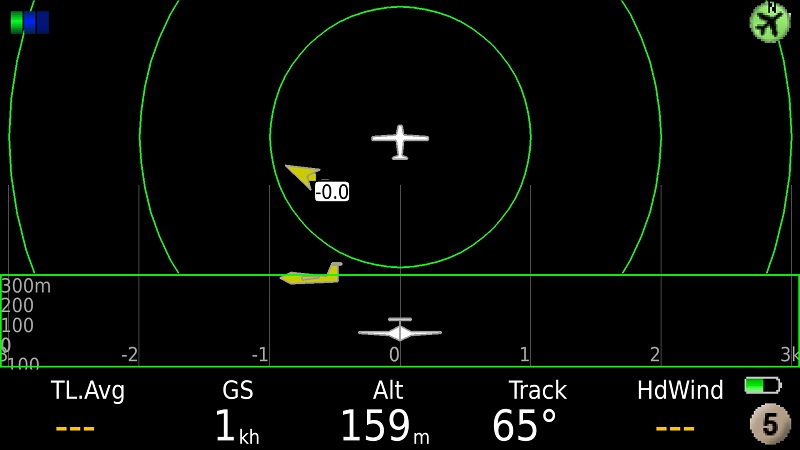
documents/images/t-motion-35.jpg
