astir13/SoftRF/documents/images/t-motion-36.jpg

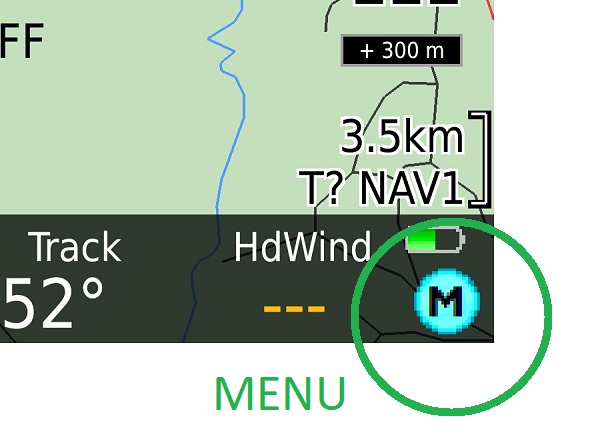
documents/images/t-motion-36.jpg
