astir13/SoftRF/documents/images/t-motion-41.jpg

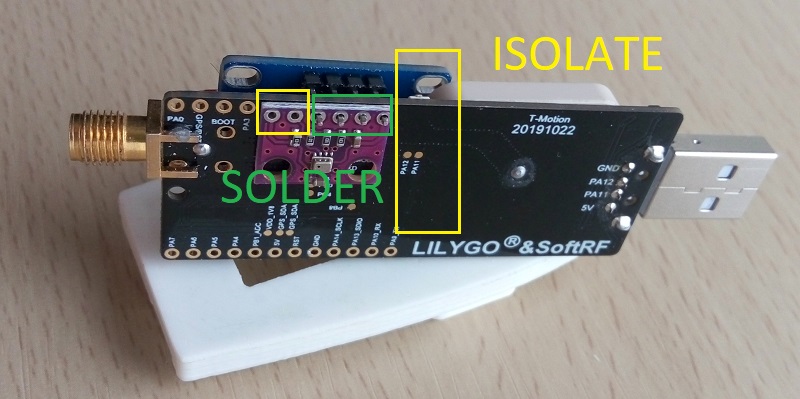
documents/images/t-motion-41.jpg
