astir13/SoftRF/documents/images/t-motion-42.jpg

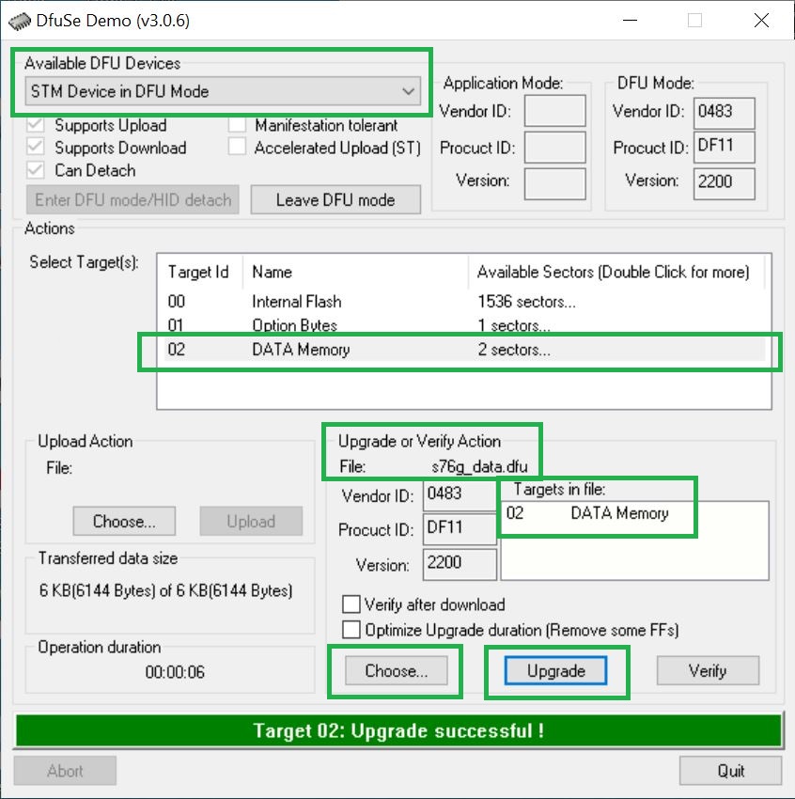
documents/images/t-motion-42.jpg
