astir13/SoftRF/documents/images/t-watch-lora-4.JPG

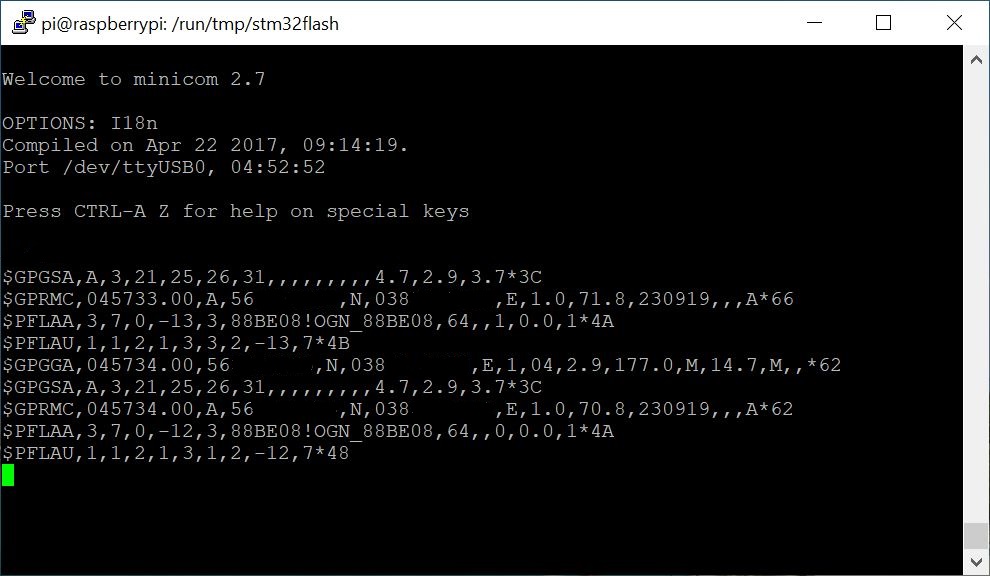
documents/images/t-watch-lora-4.JPG
