astir13/SoftRF/documents/images/t-watch-lora-5.jpg

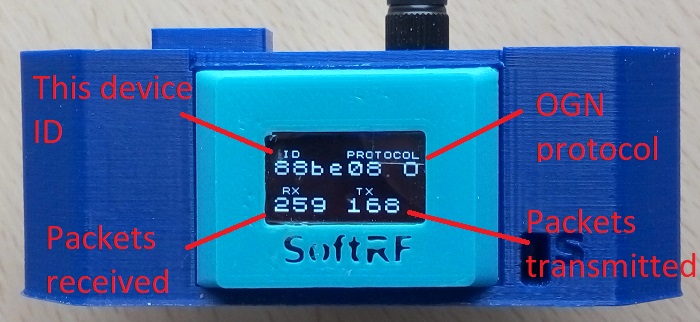
documents/images/t-watch-lora-5.jpg
