astir13/SoftRF/documents/images/ttgo-t5s-front.jpg

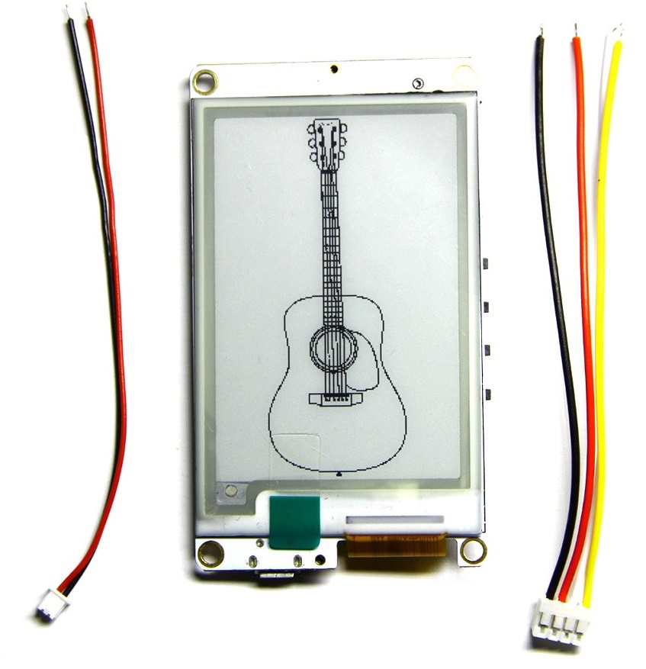
documents/images/ttgo-t5s-front.jpg
