astir13/SoftRF/documents/images/uat-drone-1.jpg

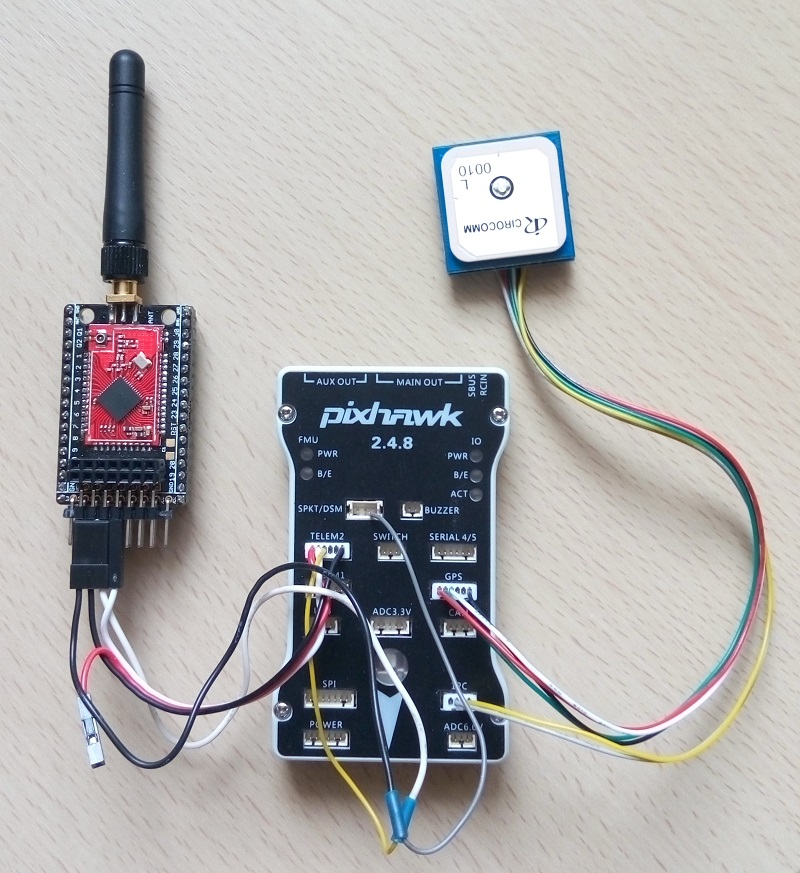
documents/images/uat-drone-1.jpg
