astir13/SoftRF/documents/images/uat-drone-2.jpg

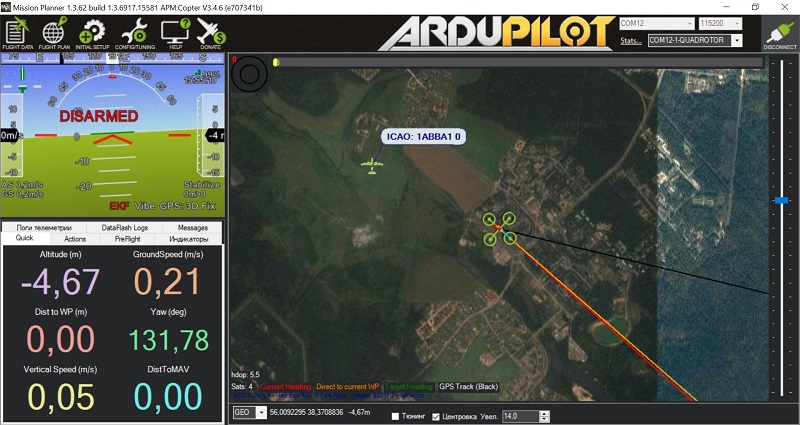
documents/images/uat-drone-2.jpg
