astir13/SoftRF/documents/images/uat-normal-1.jpg

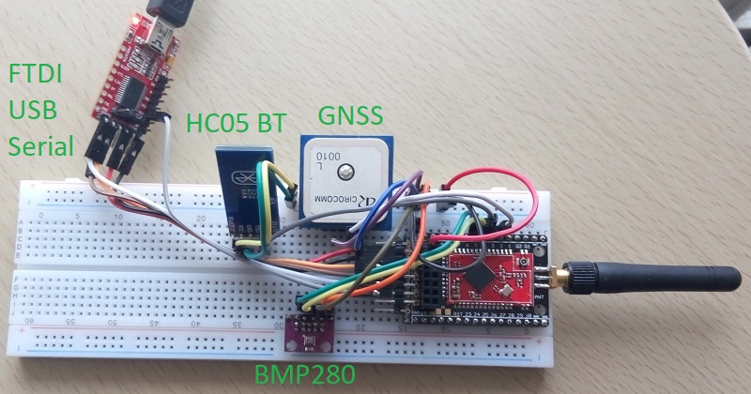
documents/images/uat-normal-1.jpg
