astir13/SoftRF/documents/images/uat-normal-2.JPG

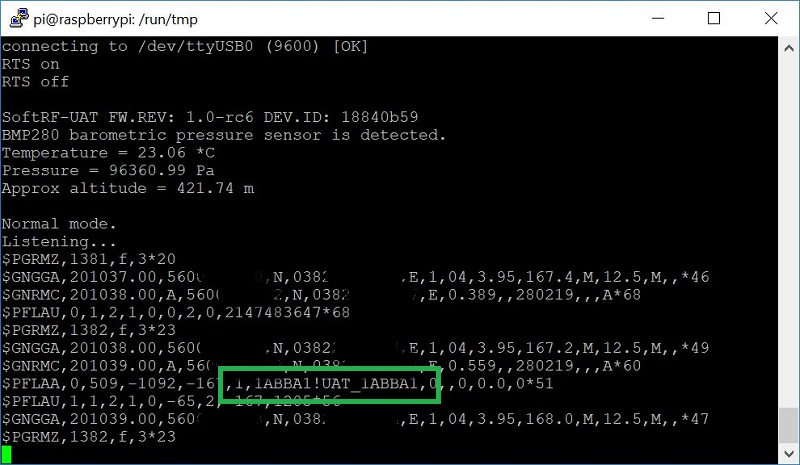
documents/images/uat-normal-2.JPG
