astir13/SoftRF/documents/images/uat-normal-5.jpg

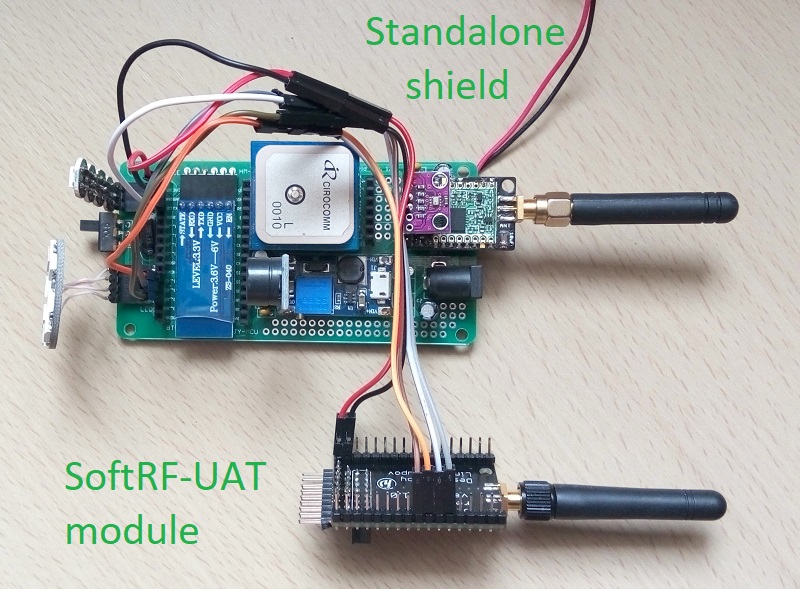
documents/images/uat-normal-5.jpg
