astir13/SoftRF/documents/images/uat-normal-6.jpg

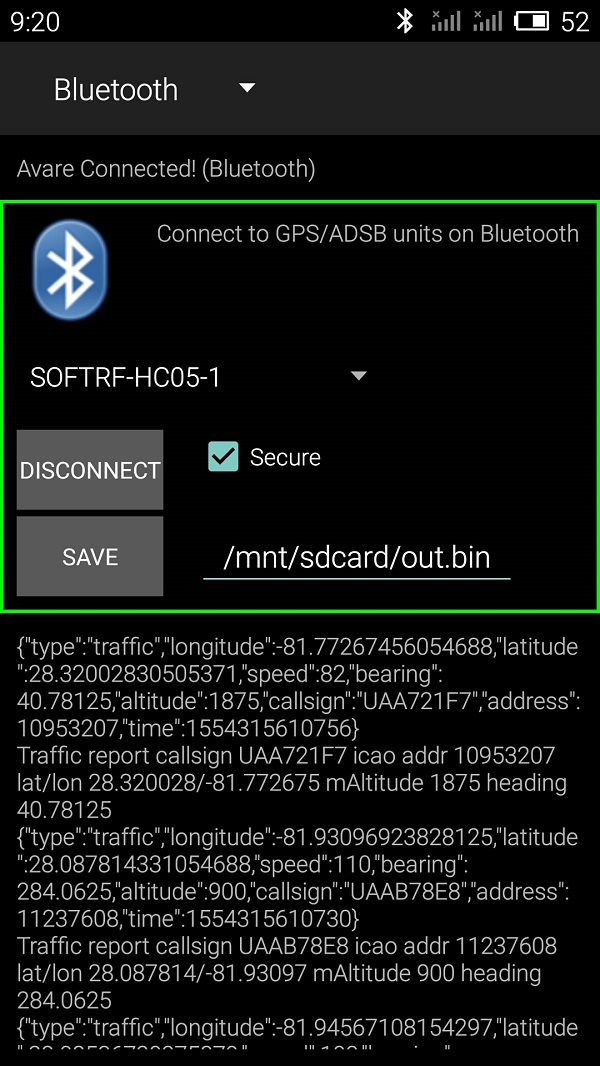
documents/images/uat-normal-6.jpg
