astir13/SoftRF/documents/images/uat-normal-7.jpg

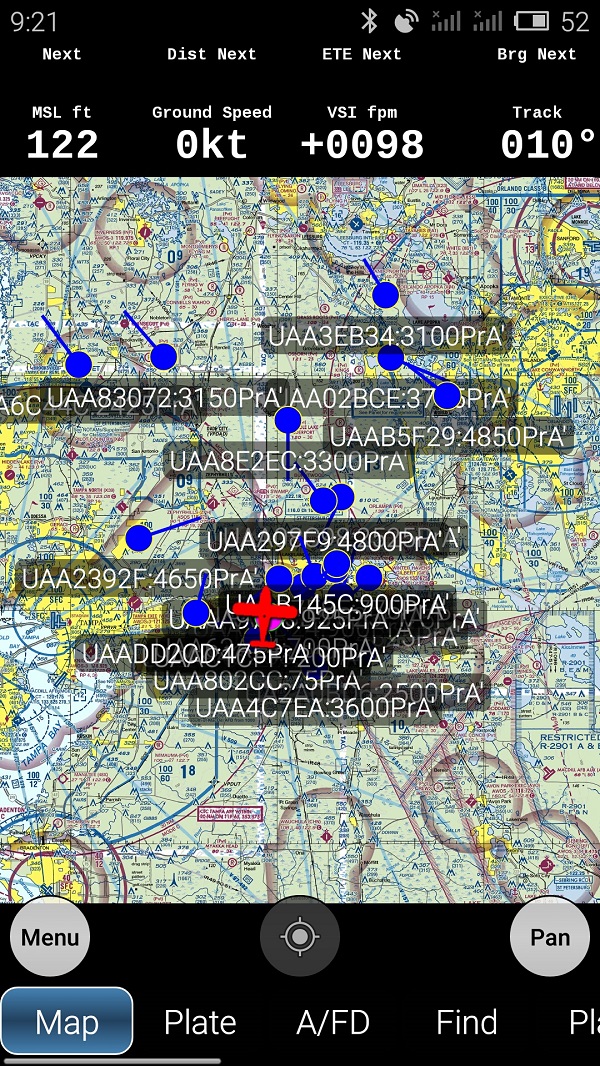
documents/images/uat-normal-7.jpg
