astir13/SoftRF/documents/images/uat-normal-8.jpg

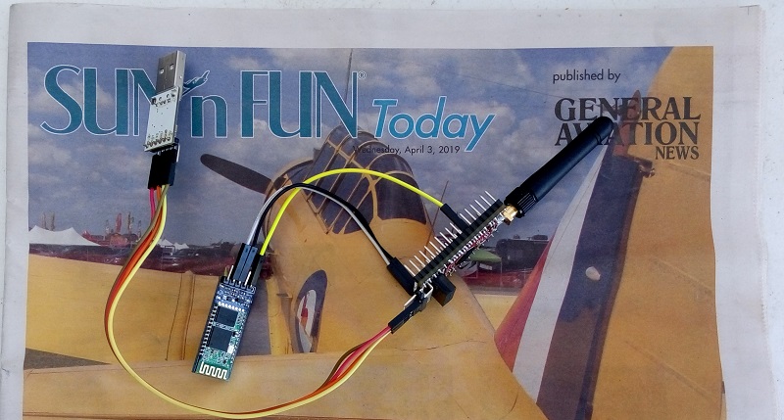
documents/images/uat-normal-8.jpg
