astir13/SoftRF/documents/images/watch-1.jpg

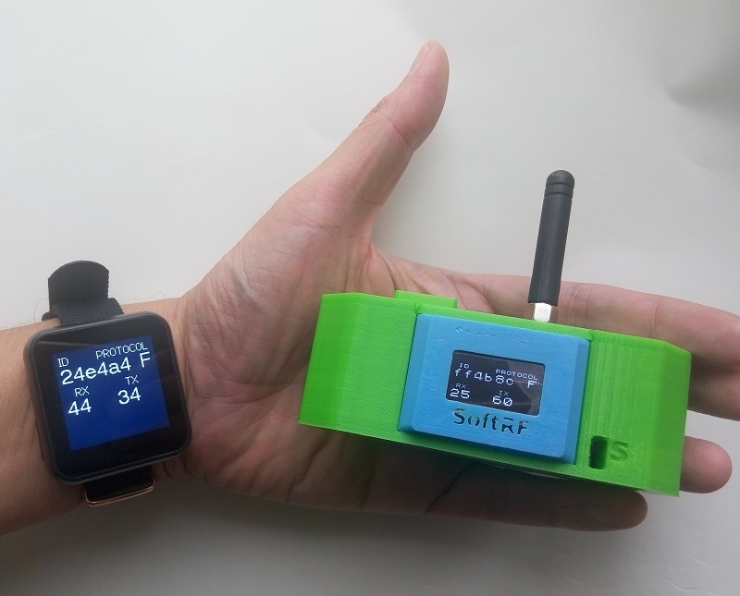
documents/images/watch-1.jpg
