astir13/SoftRF/documents/images/bom/Dragino_HAT.jpg

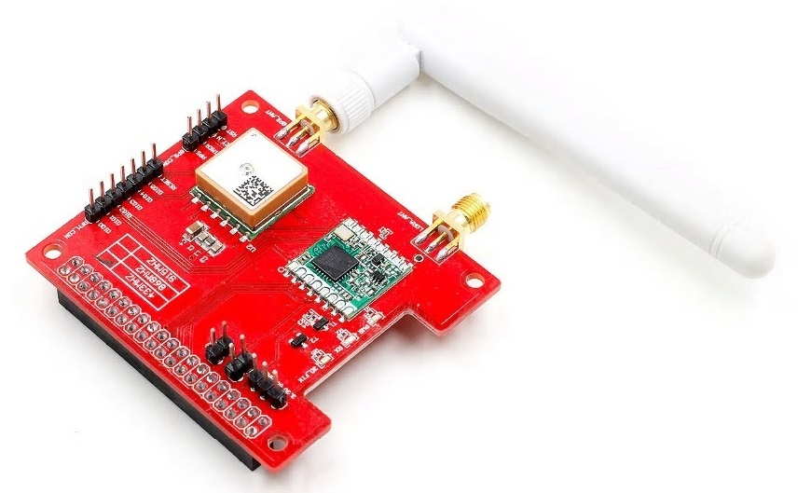
documents/images/bom/Dragino_HAT.jpg
