astir13/SoftRF/documents/images/bom/microSD.jpg

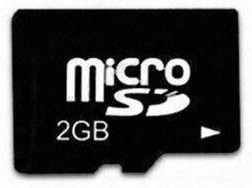
documents/images/bom/microSD.jpg
