astir13/SoftRF/documents/images/bom/powerbank-typec.jpg

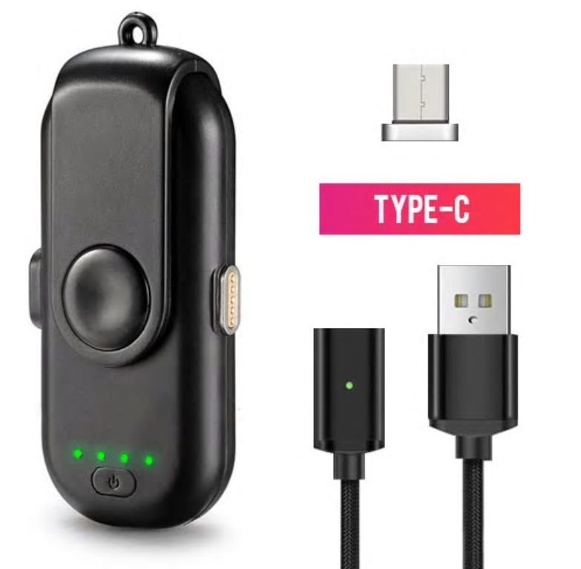
documents/images/bom/powerbank-typec.jpg
