astir13/SoftRF/software/firmware/source/SoftRF/SoftRF.h

/*
 * SoftRF.h
 * Copyright (C) 2016-2020 Linar Yusupov
 *
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
 * You should have received a copy of the GNU General Public License
 * along with this program.  If not, see <http://www.gnu.org/licenses/>.
 */

 /* Building:
  *  8. open **SoftRF** sketch from _File_ -> _Open_ menu
  *  9. Select _Tools_ -> _Board_ ->  _ESP32_ _Dev_ _Module_
  * 10. Select _Tools_ -> _Flash_ _Mode_ ->  _DIO_
  * 11. Select _Tools_ -> _Flash_ _Size_ ->  _4MB_
  * 12. Select _Tools_ -> _Partition_ _Scheme_ ->  _Minimal_ _SPIFFS_
  * 13. Select _Tools_ -> _Flash_ _Frequency_ ->  _80MHz_
  * 14. Select _Tools_ -> _CPU_ _Frequency_ ->  _80MHz_
  * 15. Select _Tools_ -> _PSRAM_ ->  _Enabled_
  * 16. _Sketch_ -> Export compiled binary
  */

#ifndef SOFTRF_H
#define SOFTRF_H

#if defined(ARDUINO)
#include <Arduino.h>
#endif /* ARDUINO */

#if defined(ENERGIA_ARCH_CC13XX)
#include <TimeLib.h>
#endif /* ENERGIA_ARCH_CC13XX */

#if defined(RASPBERRY_PI)
#include <raspi/raspi.h>
#endif /* RASPBERRY_PI */

#define SOFTRF_FIRMWARE_VERSION "1.3f"
#define SOFTRF_IDENT            "SoftRFs-"  // s for standalone fork
#define SOFTRF_ADDRESS 0x45E127
//#define SOFTRF_ADDRESS 0xFF50F0
//#define DO_GNSS_DEBUG

/* For systems where external power shall be connected under normal conditions
   (aeroplanes and sailplanes)
   shut down after timeout if no movement and no external voltage
   handling the case of forgotten to switch off the SoftRF but removed battery from plane */
#define SOFTRF_SHUTDOWN_BAT_NO_MOVE

#define ENTRY_EXPIRATION_TIME   10 /* seconds */
#define LED_EXPIRATION_TIME     5 /* seconds */
#define EXPORT_EXPIRATION_TIME  5 /* seconds */

/*
 * If you need for SoftRF to operate in wireless
 * client mode - specify your local AP's SSID/PSK:
 *
 * 
 * 
 *
 * If SoftRF's built-in AP is not stable enough for you, consider
 * to use "reverse" operation when your smartphone is acting
 * as an AP for the SoftRF unit as a client:
 *
 * #define MY_ACCESSPOINT_SSID "AndroidAP"
 * #define MY_ACCESSPOINT_PSK  "12345678"
 */
#define MY_ACCESSPOINT_SSID ""
#define MY_ACCESSPOINT_PSK ""

// Default mode is AP with
// SSID: SoftRF-XXXXXX
// KEY:  12345678
// IP: 192.168.1.1
// NETMASK: 255.255.255.0

#define RELAY_DST_PORT  12390
#define RELAY_SRC_PORT  (RELAY_DST_PORT - 1)

#define GDL90_DST_PORT    4000
#define NMEA_UDP_PORT     10110
#define NMEA_TCP_PORT     2000

/*
 * Serial I/O default values.
 * Can be overridden by platfrom-specific code.
 */
#if !defined(SERIAL_IN_BR)
/*
 * 9600 is default value of NMEA baud rate
 * for most of GNSS modules
 * being used in SoftRF project
 */
#define SERIAL_IN_BR      9600
#endif
#if !defined(SERIAL_IN_BITS)
#define SERIAL_IN_BITS    SERIAL_8N1
#endif

/*
 * 38400 is known as maximum baud rate
 * that HC-05 Bluetooth module
 * can handle without symbols loss.
 *
 * Applicable for Standalone Edition. Inherited by most of other SoftRF platforms.
 */
#define STD_OUT_BR        38400
#define STD_OUT_BITS      SERIAL_8N1

#if !defined(SERIAL_OUT_BR)
#define SERIAL_OUT_BR     STD_OUT_BR
#endif
#if !defined(SERIAL_OUT_BITS)
#define SERIAL_OUT_BITS   STD_OUT_BITS
#endif

#define UAT_BOOT_BR       9600
#define UAT_RECEIVER_BR   2000000

#if defined(PREMIUM_PACKAGE) && !defined(RASPBERRY_PI)
#define ENABLE_AHRS
#endif /* PREMIUM_PACKAGE */

typedef struct UFO {
    uint8_t   raw[34];
    time_t    timestamp;

    uint8_t   protocol;

    uint32_t  addr;
    uint8_t   addr_type;
    float     latitude;
    float     longitude;
    float     altitude;
    float     pressure_altitude;
    float     course;     /* CoG */
    float     speed;      /* ground speed in knots */
    uint8_t   aircraft_type;

    float     vs; /* feet per minute */

    bool      stealth;
    bool      no_track;

    int8_t    ns[4];
    int8_t    ew[4];

    float     geoid_separation; /* metres */
    uint16_t  hdop; /* cm */
    int8_t    rssi; /* SX1276 only */

    /* 'legacy' specific data */
    float     distance;
    float     bearing;
    int8_t    alarm_level;

    /* ADS-B (ES, UAT, GDL90) specific data */
    uint8_t   callsign[8];
} ufo_t;

typedef struct hardware_info {
    byte  model;
    byte  revision;
    byte  soc;
    byte  rf;
    byte  gnss;
    byte  baro;
    byte  display;
#if defined(ENABLE_AHRS)
    byte  ahrs;
#endif /* ENABLE_AHRS */
} hardware_info_t;

enum
{
	SOFTRF_MODE_NORMAL,
	SOFTRF_MODE_WATCHOUT,
	SOFTRF_MODE_BRIDGE,
	SOFTRF_MODE_RELAY,
	SOFTRF_MODE_TXRX_TEST,
	SOFTRF_MODE_LOOPBACK,
	SOFTRF_MODE_UAV,
	SOFTRF_MODE_RECEIVER
};

enum
{
	SOFTRF_MODEL_STANDALONE,
	SOFTRF_MODEL_PRIME,
	SOFTRF_MODEL_UAV,
	SOFTRF_MODEL_PRIME_MK2,
	SOFTRF_MODEL_RASPBERRY,
	SOFTRF_MODEL_UAT,
	SOFTRF_MODEL_SKYVIEW,
	SOFTRF_MODEL_RETRO,
	SOFTRF_MODEL_SKYWATCH,
	SOFTRF_MODEL_DONGLE
};

extern ufo_t ThisAircraft;
extern hardware_info_t hw_info;
extern const float txrx_test_positions[90][2] PROGMEM;

extern void shutdown(const char *);

#define TXRX_TEST_NUM_POSITIONS (sizeof(txrx_test_positions) / sizeof(float) / 2)
#define TXRX_TEST_ALTITUDE    438.0
#define TXRX_TEST_COURSE      280.0
#define TXRX_TEST_SPEED       50.0
#define TXRX_TEST_VS          -300.0

//#define ENABLE_TTN
//#define ENABLE_BT_VOICE
//#define TEST_PAW_ON_NICERF_SV610_FW466
#define  DO_GDL90_FF_EXT

#define LOGGER_IS_ENABLED 0

#if LOGGER_IS_ENABLED
#define StdOut  LogFile
#else
#define StdOut  Serial
#endif /* LOGGER_IS_ENABLED */

#endif /* SOFTRF_H */
