astir13/SoftRF/software/firmware/source/SoftRF/WebHelper.cpp

/*
 * WebHelper.cpp
 * Copyright (C) 2016-2020 Linar Yusupov
 *
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
 * You should have received a copy of the GNU General Public License
 * along with this program.  If not, see <http://www.gnu.org/licenses/>.
 */

#include <Arduino.h>

#include "BatteryHelper.h"
#include "RFHelper.h"
#include "SoCHelper.h"
#include "WebHelper.h"
#include "BaroHelper.h"
#include "LEDHelper.h"
#include "SoundHelper.h"
#include "BluetoothHelper.h"
#include "TrafficHelper.h"
#include "NMEAHelper.h"
#include "GDL90Helper.h"
#include "D1090Helper.h"

#if defined(ENABLE_AHRS)
#include "AHRSHelper.h"
#endif /* ENABLE_AHRS */

static uint32_t prev_rx_pkt_cnt = 0;

static const char Logo[] PROGMEM = {
#include "Logo.h"
    } ;

#include "jquery_min_js.h"

byte getVal(char c)
{
   if(c >= '0' && c <= '9')
     return (byte)(c - '0');
   else
     return (byte)(toupper(c)-'A'+10);
}

#if DEBUG
void Hex2Bin(String str, byte *buffer)
{
  char hexdata[2 * PKT_SIZE + 1];
  
  str.toCharArray(hexdata, sizeof(hexdata));
  for(int j = 0; j < PKT_SIZE * 2 ; j+=2)
  {
    buffer[j>>1] = getVal(hexdata[j+1]) + (getVal(hexdata[j]) << 4);
  }
}
#endif

static const char about_html[] PROGMEM = "<html>\
  <head>\
    <meta name='viewport' content='width=device-width, initial-scale=1'>\
    <title>About</title>\
  </head>\
<body>\
<h1 align=center>About</h1>\
<p>This firmware is a fork of open SoftRF project, adapted to my personal preferences</p>\
<p>URL: http://github.com/astir13/SoftRF_standalone</p>\
<p>Author: <b>Stefan Pielmeier</b></p>\
<p>E-mail: stefan@symlinux.com</p>\
<h2 align=center>Credits</h2>\
<p align=center>(in historical order)</p>\
<table width=100%%>\
<tr><th align=left>Linar Yusupov</th><td align=left>Project lyusupov/SoftRF (open SoftRF)</td></tr>\
<tr><th align=left>Ivan Grokhotkov</th><td align=left>Arduino core for ESP8266</td></tr>\
<tr><th align=left>Zak Kemble</th><td align=left>nRF905 library</td></tr>\
<tr><th align=left>Stanislaw Pusep</th><td align=left>flarm_decode</td></tr>\
<tr><th align=left>Paul Stoffregen</th><td align=left>Arduino Time Library</td></tr>\
<tr><th align=left>Mikal Hart</th><td align=left>TinyGPS++ and PString Libraries</td></tr>\
<tr><th align=left>Phil Burgess</th><td align=left>Adafruit NeoPixel Library</td></tr>\
<tr><th align=left>Andy Little</th><td align=left>Aircraft and MAVLink Libraries</td></tr>\
<tr><th align=left>Peter Knight</th><td align=left>TrueRandom Library</td></tr>\
<tr><th align=left>Matthijs Kooijman</th><td align=left>IBM LMIC framework for Arduino</td></tr>\
<tr><th align=left>David Paiva</th><td align=left>ESP8266FtpServer</td></tr>\
<tr><th align=left>Lammert Bies</th><td align=left>Lib_crc</td></tr>\
<tr><th align=left>Pawel Jalocha</th><td align=left>OGN library</td></tr>\
<tr><th align=left>Timur Sinitsyn, Tobias Simon, Ferry Huberts</th><td align=left>NMEA library</td></tr>\
<tr><th align=left>yangbinbin (yangbinbin_ytu@163.com)</th><td align=left>ADS-B encoder C++ library</td></tr>\
<tr><th align=left>Hristo Gochkov</th><td align=left>Arduino core for ESP32</td></tr>\
<tr><th align=left>Evandro Copercini</th><td align=left>ESP32 BT SPP library</td></tr>\
<tr><th align=left>Limor Fried and Ladyada</th><td align=left>Adafruit BMP085 library</td></tr>\
<tr><th align=left>Kevin Townsend</th><td align=left>Adafruit BMP280 library</td></tr>\
<tr><th align=left>Limor Fried and Kevin Townsend</th><td align=left>Adafruit MPL3115A2 library</td></tr>\
<tr><th align=left>Oliver Kraus</th><td align=left>U8g2 LCD, OLED and eInk library</td></tr>\
<tr><th align=left>Michael Miller</th><td align=left>NeoPixelBus library</td></tr>\
<tr><th align=left>Shenzhen Xin Yuan (LilyGO) ET company</th><td align=left>TTGO T-Beam and T-Watch</td></tr>\
<tr><th align=left>JS Foundation</th><td align=left>jQuery library</td></tr>\
<tr><th align=left>XCSoar team</th><td align=left>EGM96 data</td></tr>\
<tr><th align=left>Mike McCauley</th><td align=left>BCM2835 C library</td></tr>\
<tr><th align=left>Dario Longobardi</th><td align=left>SimpleNetwork library</td></tr>\
<tr><th align=left>Benoit Blanchon</th><td align=left>ArduinoJson library</td></tr>\
<tr><th align=left>flashrom.org project</th><td align=left>Flashrom library</td></tr>\
<tr><th align=left>Robert Wessels and Tony Cave</th><td align=left>EasyLink library</td></tr>\
<tr><th align=left>Oliver Jowett</th><td align=left>Dump978 library</td></tr>\
<tr><th align=left>Phil Karn</th><td align=left>FEC library</td></tr>\
<tr><th align=left>Lewis He</th><td align=left>AXP20X library</td></tr>\
<tr><th align=left>Bodmer</th><td align=left>TFT library</td></tr>\
</table>\
<hr>\
Copyright (C) 2018-2020 &nbsp;&nbsp;&nbsp; Stefan Pielmeier\
</body>\
</html>";

void handleSettings() {

  size_t size = 5700;
  char *offset;
  size_t len = 0;
  char *Settings_temp = (char *) malloc(size);

  if (Settings_temp == NULL) {
    return;
  }

  offset = Settings_temp;

  /* Common part 1 */
  snprintf_P ( offset, size,
    PSTR("<html>\
<head>\
<meta name='viewport' content='width=device-width, initial-scale=1'>\
<title>Settings</title>\
</head>\
<body>\
<h1 align=center>Settings</h1>\
<form action='/input' method='GET'>\
<table width=100%%>\
<tr>\
<th align=left>Mode</th>\
<td align=right>\
<select name='mode'>\
<option %s value='%d'>Normal</option>\
<!-- <option %s value='%d'>Tx/Rx Test</option> -->\
<option %s value='%d'>Bridge</option>\
<option %s value='%d'>UAV</option>\
</select>\
</td>\
</tr>"),
  (settings->mode == SOFTRF_MODE_NORMAL ? "selected" : "") , SOFTRF_MODE_NORMAL,
  (settings->mode == SOFTRF_MODE_TXRX_TEST ? "selected" : ""), SOFTRF_MODE_TXRX_TEST,
  (settings->mode == SOFTRF_MODE_BRIDGE ? "selected" : ""), SOFTRF_MODE_BRIDGE,
  (settings->mode == SOFTRF_MODE_UAV ? "selected" : ""), SOFTRF_MODE_UAV
/*  (settings->mode == SOFTRF_MODE_WATCHOUT ? "selected" : ""), SOFTRF_MODE_WATCHOUT, */
  );

  len = strlen(offset);
  offset += len;
  size -= len;

  /* Radio specific part */
  if (hw_info.rf == RF_IC_SX1276) {
    snprintf_P ( offset, size,
      PSTR("\
<tr>\
<th align=left>Protocol</th>\
<td align=right>\
<select name='protocol'>\
<option %s value='%d'>%s</option>\
<option %s value='%d'>%s</option>\
<option %s value='%d'>%s</option>\
<option %s value='%d'>%s</option>\
</select>\
</td>\
</tr>"),
    (settings->rf_protocol == RF_PROTOCOL_LEGACY ? "selected" : ""),
     RF_PROTOCOL_LEGACY, legacy_proto_desc.name,
    (settings->rf_protocol == RF_PROTOCOL_OGNTP ? "selected" : ""),
     RF_PROTOCOL_OGNTP, ogntp_proto_desc.name,
    (settings->rf_protocol == RF_PROTOCOL_P3I ? "selected" : ""),
     RF_PROTOCOL_P3I, p3i_proto_desc.name,
    (settings->rf_protocol == RF_PROTOCOL_FANET ? "selected" : ""),
     RF_PROTOCOL_FANET, fanet_proto_desc.name
    );
  } else {
    snprintf_P ( offset, size,
      PSTR("\
<tr>\
<th align=left>Protocol</th>\
<td align=right>%s\
</td>\
</tr>"),
    (settings->rf_protocol == RF_PROTOCOL_LEGACY   ? legacy_proto_desc.name :
    (settings->rf_protocol == RF_PROTOCOL_ADSB_UAT ? uat978_proto_desc.name :
    (settings->rf_protocol == RF_PROTOCOL_FANET    ? fanet_proto_desc.name  :
     "UNK")))
    );
  }
  len = strlen(offset);
  offset += len;
  size -= len;

  /* Common part 2 */
  snprintf_P ( offset, size,
    PSTR("\
<tr>\
<th align=left>Region</th>\
<td align=right>\
<select name='band'>\
<option %s value='%d'>AUTO</option>\
<option %s value='%d'>EU (868.2 MHz)</option>\
<option %s value='%d'>RU (868.8 MHz)</option>\
<option %s value='%d'>CN (470 MHz)</option>\
<option %s value='%d'>US/CA (915 MHz)</option>\
<option %s value='%d'>NZ (869.25 MHz)</option>\
<option %s value='%d'>UK (869.52 MHz)</option>\
<option %s value='%d'>AU (921 MHz)</option>\
<option %s value='%d'>IN (866 MHz)</option>\
</select>\
</td>\
</tr>\
<tr>\
<th align=left>Aircraft type</th>\
<td align=right>\
<select name='acft_type'>\
<option %s value='%d'>Glider</option>\
<option %s value='%d'>Towplane</option>\
<option %s value='%d'>Powered</option>\
<option %s value='%d'>Helicopter</option>\
<option %s value='%d'>UAV</option>\
<option %s value='%d'>Hangglider</option>\
<option %s value='%d'>Paraglider</option>\
<option %s value='%d'>Balloon</option>\
<option %s value='%d'>Static</option>\
</select>\
</td>\
</tr>\
<tr>\
<th align=left>Alarm trigger</th>\
<td align=right>\
<select name='alarm'>\
<option %s value='%d'>None</option>\
<option %s value='%d'>Distance</option>\
<option %s value='%d'>Vector</option>\
</select>\
</td>\
</tr>\
<tr>\
<th align=left>Tx Power</th>\
<td align=right>\
<select name='txpower'>\
<option %s value='%d'>Full</option>\
<option %s value='%d'>EU</option>\
<option %s value='%d'>Low</option>\
<option %s value='%d'>Off</option>\
</select>\
</td>\
</tr>\
<tr>\
<th align=left>Volume</th>\
<td align=right>\
<select name='volume'>\
<option %s value='%d'>Loud</option>\
<option %s value='%d'>Low</option>\
<option %s value='%d'>Off</option>\
</select>\
</td>\
</tr>\
<tr>\
<th align=left>LED ring direction</th>\
<td align=right>\
<select name='pointer'>\
<option %s value='%d'>CoG Up</option>\
<option %s value='%d'>North Up</option>\
<option %s value='%d'>Off</option>\
</select>\
</td>\
</tr>"),
  (settings->band == RF_BAND_AUTO ? "selected" : ""), RF_BAND_AUTO,
  (settings->band == RF_BAND_EU ? "selected" : ""), RF_BAND_EU,
  (settings->band == RF_BAND_RU ? "selected" : ""), RF_BAND_RU,
  (settings->band == RF_BAND_CN ? "selected" : ""), RF_BAND_CN,
  (settings->band == RF_BAND_US ? "selected" : ""), RF_BAND_US,
  (settings->band == RF_BAND_NZ ? "selected" : ""), RF_BAND_NZ,
  (settings->band == RF_BAND_UK ? "selected" : ""), RF_BAND_UK,
  (settings->band == RF_BAND_AU ? "selected" : ""), RF_BAND_AU,
  (settings->band == RF_BAND_IN ? "selected" : ""), RF_BAND_IN,
  (settings->aircraft_type == AIRCRAFT_TYPE_GLIDER ? "selected" : ""),  AIRCRAFT_TYPE_GLIDER,
  (settings->aircraft_type == AIRCRAFT_TYPE_TOWPLANE ? "selected" : ""),  AIRCRAFT_TYPE_TOWPLANE,
  (settings->aircraft_type == AIRCRAFT_TYPE_POWERED ? "selected" : ""),  AIRCRAFT_TYPE_POWERED,
  (settings->aircraft_type == AIRCRAFT_TYPE_HELICOPTER ? "selected" : ""),  AIRCRAFT_TYPE_HELICOPTER,
  (settings->aircraft_type == AIRCRAFT_TYPE_UAV ? "selected" : ""),  AIRCRAFT_TYPE_UAV,
  (settings->aircraft_type == AIRCRAFT_TYPE_HANGGLIDER ? "selected" : ""),  AIRCRAFT_TYPE_HANGGLIDER,
  (settings->aircraft_type == AIRCRAFT_TYPE_PARAGLIDER ? "selected" : ""),  AIRCRAFT_TYPE_PARAGLIDER,
  (settings->aircraft_type == AIRCRAFT_TYPE_BALLOON ? "selected" : ""),  AIRCRAFT_TYPE_BALLOON,
  (settings->aircraft_type == AIRCRAFT_TYPE_STATIC ? "selected" : ""),  AIRCRAFT_TYPE_STATIC,
  (settings->alarm == TRAFFIC_ALARM_NONE ? "selected" : ""),  TRAFFIC_ALARM_NONE,
  (settings->alarm == TRAFFIC_ALARM_DISTANCE ? "selected" : ""),  TRAFFIC_ALARM_DISTANCE,
  (settings->alarm == TRAFFIC_ALARM_VECTOR ? "selected" : ""),  TRAFFIC_ALARM_VECTOR,
  (settings->txpower == RF_TX_POWER_FULL ? "selected" : ""),  RF_TX_POWER_FULL,
  (settings->txpower == RF_TX_POWER_EU ? "selected" : ""),  RF_TX_POWER_EU,
  (settings->txpower == RF_TX_POWER_LOW ? "selected" : ""),  RF_TX_POWER_LOW,
  (settings->txpower == RF_TX_POWER_OFF ? "selected" : ""),  RF_TX_POWER_OFF,
  (settings->volume == BUZZER_VOLUME_FULL ? "selected" : ""), BUZZER_VOLUME_FULL,
  (settings->volume == BUZZER_VOLUME_LOW ? "selected" : ""), BUZZER_VOLUME_LOW,
  (settings->volume == BUZZER_OFF ? "selected" : ""), BUZZER_OFF,
  (settings->pointer == DIRECTION_TRACK_UP ? "selected" : ""), DIRECTION_TRACK_UP,
  (settings->pointer == DIRECTION_NORTH_UP ? "selected" : ""), DIRECTION_NORTH_UP,
  (settings->pointer == LED_OFF ? "selected" : ""), LED_OFF
  );

  len = strlen(offset);
  offset += len;
  size -= len;

  /* SoC specific part 1 */
  if (SoC->id == SOC_ESP32) {
    snprintf_P ( offset, size,
      PSTR("\
<tr>\
<th align=left>Built-in Bluetooth</th>\
<td align=right>\
<select name='bluetooth'>\
<option %s value='%d'>Off</option>\
<option %s value='%d'>SPP</option>\
<option %s value='%d'>LE</option>\
</select>\
</td>\
</tr>"),
    (settings->bluetooth == BLUETOOTH_OFF ? "selected" : ""), BLUETOOTH_OFF,
    (settings->bluetooth == BLUETOOTH_SPP ? "selected" : ""), BLUETOOTH_SPP,
    (settings->bluetooth == BLUETOOTH_LE_HM10_SERIAL ? "selected" : ""), BLUETOOTH_LE_HM10_SERIAL
    );

    len = strlen(offset);
    offset += len;
    size -= len;
  }

  /* Common part 3 */
  snprintf_P ( offset, size,
    PSTR("\
<tr>\
<th align=left>NMEA sentences:</th>\
</tr>\
<tr>\
<th align=left>&nbsp;&nbsp;&nbsp;&nbsp;&nbsp;&nbsp;&nbsp;&nbsp;GNSS</th>\
<td align=right>\
<input type='radio' name='nmea_g' value='0' %s>Off\
<input type='radio' name='nmea_g' value='1' %s>On\
</td>\
</tr>\
<tr>\
<th align=left>&nbsp;&nbsp;&nbsp;&nbsp;&nbsp;&nbsp;&nbsp;&nbsp;Private</th>\
<td align=right>\
<input type='radio' name='nmea_p' value='0' %s>Off\
<input type='radio' name='nmea_p' value='1' %s>On\
</td>\
</tr>\
<tr>\
<th align=left>&nbsp;&nbsp;&nbsp;&nbsp;&nbsp;&nbsp;&nbsp;&nbsp;Legacy</th>\
<td align=right>\
<input type='radio' name='nmea_l' value='0' %s>Off\
<input type='radio' name='nmea_l' value='1' %s>On\
</td>\
</tr>\
<tr>\
<th align=left>&nbsp;&nbsp;&nbsp;&nbsp;&nbsp;&nbsp;&nbsp;&nbsp;Sensors</th>\
<td align=right>\
<input type='radio' name='nmea_s' value='0' %s>Off\
<input type='radio' name='nmea_s' value='1' %s>On\
</td>\
</tr>\
<tr>\
<th align=left>NMEA output</th>\
<td align=right>\
<select name='nmea_out'>\
<option %s value='%d'>Off</option>\
<option %s value='%d'>Serial</option>\
<option %s value='%d'>UDP</option>"),
  (!settings->nmea_g ? "checked" : "") , (settings->nmea_g ? "checked" : ""),
  (!settings->nmea_p ? "checked" : "") , (settings->nmea_p ? "checked" : ""),
  (!settings->nmea_l ? "checked" : "") , (settings->nmea_l ? "checked" : ""),
  (!settings->nmea_s ? "checked" : "") , (settings->nmea_s ? "checked" : ""),
  (settings->nmea_out == NMEA_OFF ? "selected" : ""), NMEA_OFF,
  (settings->nmea_out == NMEA_UART ? "selected" : ""), NMEA_UART,
  (settings->nmea_out == NMEA_UDP ? "selected" : ""), NMEA_UDP);

  len = strlen(offset);
  offset += len;
  size -= len;

  /* SoC specific part 2 */
  if (SoC->id == SOC_ESP32) {
    snprintf_P ( offset, size,
      PSTR("\
<option %s value='%d'>TCP</option>\
<option %s value='%d'>Serial and Bluetooth</option>\
<option %s value='%d'>Bluetooth</option>"),
    (settings->nmea_out == NMEA_TCP ? "selected" : ""), NMEA_TCP,
    (settings->nmea_out == NMEA_UART_BT ? "selected" : ""), NMEA_UART_BT,
    (settings->nmea_out == NMEA_BLUETOOTH ? "selected" : ""), NMEA_BLUETOOTH);

    len = strlen(offset);
    offset += len;
    size -= len;
  }

  /* Common part 4 */
  snprintf_P ( offset, size,
    PSTR("\
</select>\
</td>\
</tr>\
<tr>\
<th align=left>GDL90</th>\
<td align=right>\
<select name='gdl90'>\
<option %s value='%d'>Off</option>\
<option %s value='%d'>Serial</option>\
<option %s value='%d'>UDP</option>"),
  (settings->gdl90 == GDL90_OFF ? "selected" : ""), GDL90_OFF,
  (settings->gdl90 == GDL90_UART ? "selected" : ""), GDL90_UART,
  (settings->gdl90 == GDL90_UDP ? "selected" : ""), GDL90_UDP);

  len = strlen(offset);
  offset += len;
  size -= len;

  /* SoC specific part 3 */
  if (SoC->id == SOC_ESP32) {
    snprintf_P ( offset, size,
      PSTR("\
<option %s value='%d'>Bluetooth</option>"),
    (settings->gdl90 == GDL90_BLUETOOTH ? "selected" : ""), GDL90_BLUETOOTH);

    len = strlen(offset);
    offset += len;
    size -= len;
  }

  /* Common part 5 */
  snprintf_P ( offset, size,
    PSTR("\
</select>\
</td>\
</tr>\
<tr>\
<th align=left>Dump1090</th>\
<td align=right>\
<select name='d1090'>\
<option %s value='%d'>Off</option>\
<option %s value='%d'>Serial</option>"),
  (settings->d1090 == D1090_OFF ? "selected" : ""), D1090_OFF,
  (settings->d1090 == D1090_UART ? "selected" : ""), D1090_UART);

  len = strlen(offset);
  offset += len;
  size -= len;

  /* SoC specific part 4 */
  if (SoC->id == SOC_ESP32) {
    snprintf_P ( offset, size,
      PSTR("\
<option %s value='%d'>Bluetooth</option>"),
    (settings->d1090 == D1090_BLUETOOTH ? "selected" : ""), D1090_BLUETOOTH);

    len = strlen(offset);
    offset += len;
    size -= len;
  }

  /* Common part 6 */
  snprintf_P ( offset, size,
    PSTR("\
</select>\
</td>\
</tr>\
<tr>\
<th align=left>Power save</th>\
<td align=right>\
<select name='power_save'>\
<option %s value='%d'>Disabled</option>\
<option %s value='%d'>WiFi OFF (10 min.)</option>\
</select>\
</td>\
</tr>\
<tr>\
<th align=left>Stealth</th>\
<td align=right>\
<input type='radio' name='stealth' value='0' %s>Off\
<input type='radio' name='stealth' value='1' %s>On\
</td>\
</tr>\
<tr>\
<th align=left>No track</th>\
<td align=right>\
<input type='radio' name='no_track' value='0' %s>Off\
<input type='radio' name='no_track' value='1' %s>On\
</td>\
</tr>\
</table>\
<p align=center><INPUT type='submit' value='Save and restart'></p>\
</form>\
</body>\
</html>"),
  (settings->power_save == POWER_SAVE_NONE ? "selected" : ""), POWER_SAVE_NONE,
  (settings->power_save == POWER_SAVE_WIFI ? "selected" : ""), POWER_SAVE_WIFI,
  (!settings->stealth ? "checked" : "") , (settings->stealth ? "checked" : ""),
  (!settings->no_track ? "checked" : "") , (settings->no_track ? "checked" : "")
  );

  SoC->swSer_enableRx(false);
  server.sendHeader(String(F("Cache-Control")), String(F("no-cache, no-store, must-revalidate")));
  server.sendHeader(String(F("Pragma")), String(F("no-cache")));
  server.sendHeader(String(F("Expires")), String(F("-1")));
  server.send ( 200, "text/html", Settings_temp );
  SoC->swSer_enableRx(true);
  free(Settings_temp);
}

void handleRoot() {
  int sec = millis() / 1000;
  int min = sec / 60;
  int hr = min / 60;

  float vdd = Battery_voltage() ;
  bool low_voltage = (Battery_voltage() <= Battery_threshold());

  time_t timestamp = ThisAircraft.timestamp;
  unsigned int sats = gnss.satellites.value(); // Number of satellites in use (u32)
  char str_lat[16];
  char str_lon[16];
  char str_alt[16];
  char str_Vcc[8];

  char *Root_temp = (char *) malloc(2300);
  if (Root_temp == NULL) {
    return;
  }

  dtostrf(ThisAircraft.latitude, 8, 4, str_lat);
  dtostrf(ThisAircraft.longitude, 8, 4, str_lon);
  dtostrf(ThisAircraft.altitude, 7, 1, str_alt);
  dtostrf(vdd, 4, 2, str_Vcc);

  snprintf_P ( Root_temp, 2500,
    PSTR("<html>\
  <head>\
    <meta name='viewport' content='width=device-width, initial-scale=1'>\
    <title>SoftRF status</title>\
  </head>\
<body>\
 <table width=100%%>\
  <tr><!-- <td align=left><h1>&nbsp;&nbsp;&nbsp;&nbsp;&nbsp;</h1></td> -->\
  <td align=center><h1>SoftRF status</h1></td>\
  <!-- <td align=right><img src='/logo.png'></td> --></tr>\
 </table>\
 <table width=100%%>\
  <tr><th align=left>Device Id</th><td align=right>%X</td></tr>\
  <tr><th align=left>Software Version (astir13/SoftRF_standalone)</th><td align=right>%s&nbsp;&nbsp;%s</td></tr>"
#if !defined(ENABLE_AHRS)
 "</table><table width=100%%>\
  <tr><td align=left><table><tr><th align=left>GNSS&nbsp;&nbsp;</th><td align=right>%s</td></tr></table></td>\
  <td align=center><table><tr><th align=left>Radio&nbsp;&nbsp;</th><td align=right>%s</td></tr></table></td>\
  <td align=right><table><tr><th align=left>Baro&nbsp;&nbsp;</th><td align=right>%s</td></tr></table></td></tr>\
  </table><table width=100%%>"
#else
 "<tr><td align=left><table><tr><th align=left>GNSS&nbsp;&nbsp;</th><td align=right>%s</td></tr></table></td>\
  <td align=right><table><tr><th align=left>Radio&nbsp;&nbsp;</th><td align=right>%s</td></tr></table></td></tr>\
  <tr><td align=left><table><tr><th align=left>Baro&nbsp;&nbsp;</th><td align=right>%s</td></tr></table></td>\
  <td align=right><table><tr><th align=left>AHRS&nbsp;&nbsp;</th><td align=right>%s</td></tr></table></td></tr>"
#endif /* ENABLE_AHRS */
 "<tr><th align=left>Uptime</th><td align=right>%02d:%02d:%02d</td></tr>\
  <tr><th align=left>Free memory</th><td align=right>%u</td></tr>\
  <tr><th align=left>Battery voltage</th><td align=right><font color=%s>%s</font></td></tr>\
 </table>\
 <table width=100%%>\
   <tr><th align=left>Packets</th>\
    <td align=right><table><tr>\
     <th align=left>Tx&nbsp;&nbsp;</th><td align=right>%u</td>\
     <th align=left>&nbsp;&nbsp;&nbsp;&nbsp;Rx&nbsp;&nbsp;</th><td align=right>%u</td>\
   </tr></table></td></tr>\
 </table>\
 <h2 align=center>Most recent GNSS fix</h2>\
 <table width=100%%>\
  <tr><th align=left>Time</th><td align=right>%u</td></tr>\
  <tr><th align=left>Satellites</th><td align=right>%d</td></tr>\
  <tr><th align=left>Latitude</th><td align=right>%s</td></tr>\
  <tr><th align=left>Longitude</th><td align=right>%s</td></tr>\
  <tr><td align=left><b>Altitude</b>&nbsp;&nbsp;(above MSL)</td><td align=right>%s</td></tr>\
 </table>\
 <hr>\
 <table width=100%%>\
  <tr>\
    <td align=left><input type=button onClick=\"location.href='/settings'\" value='Settings'></td>\
    <td align=center><input type=button onClick=\"location.href='/about'\" value='About'></td>\
    <td align=right><input type=button onClick=\"location.href='/firmware'\" value='Firmware update'></td>\
  </tr>\
 </table>\
</body>\
</html>"),
    ThisAircraft.addr, SOFTRF_FIRMWARE_VERSION
#if defined(SOFTRF_ADDRESS)
    "I"
#endif
    ,
    (SoC == NULL ? "NONE" : SoC->name),
    GNSS_name[hw_info.gnss],
    (rf_chip == NULL ? "NONE" : rf_chip->name),
    (baro_chip == NULL ? "NONE" : baro_chip->name),
#if defined(ENABLE_AHRS)
    (ahrs_chip == NULL ? "NONE" : ahrs_chip->name),
#endif /* ENABLE_AHRS */
    hr, min % 60, sec % 60, ESP.getFreeHeap(),
    low_voltage ? "red" : "green", str_Vcc,
    tx_packets_counter, rx_packets_counter,
    timestamp, sats, str_lat, str_lon, str_alt
  );
  SoC->swSer_enableRx(false);
  server.sendHeader(String(F("Cache-Control")), String(F("no-cache, no-store, must-revalidate")));
  server.sendHeader(String(F("Pragma")), String(F("no-cache")));
  server.sendHeader(String(F("Expires")), String(F("-1")));
  server.send ( 200, "text/html", Root_temp );
  SoC->swSer_enableRx(true);
  free(Root_temp);
}

void handleInput() {

  char *Input_temp = (char *) malloc(1520);
  if (Input_temp == NULL) {
    return;
  }

  for ( uint8_t i = 0; i < server.args(); i++ ) {
    if (server.argName(i).equals("mode")) {
      settings->mode = server.arg(i).toInt();
    } else if (server.argName(i).equals("protocol")) {
      settings->rf_protocol = server.arg(i).toInt();
    } else if (server.argName(i).equals("band")) {
      settings->band = server.arg(i).toInt();
    } else if (server.argName(i).equals("acft_type")) {
      settings->aircraft_type = server.arg(i).toInt();
    } else if (server.argName(i).equals("alarm")) {
      settings->alarm = server.arg(i).toInt();
    } else if (server.argName(i).equals("txpower")) {
      settings->txpower = server.arg(i).toInt();
    } else if (server.argName(i).equals("volume")) {
      settings->volume = server.arg(i).toInt();
    } else if (server.argName(i).equals("pointer")) {
      settings->pointer = server.arg(i).toInt();
    } else if (server.argName(i).equals("bluetooth")) {
      settings->bluetooth = server.arg(i).toInt();
    } else if (server.argName(i).equals("nmea_g")) {
      settings->nmea_g = server.arg(i).toInt();
    } else if (server.argName(i).equals("nmea_p")) {
      settings->nmea_p = server.arg(i).toInt();
    } else if (server.argName(i).equals("nmea_l")) {
      settings->nmea_l = server.arg(i).toInt();
    } else if (server.argName(i).equals("nmea_s")) {
      settings->nmea_s = server.arg(i).toInt();
    } else if (server.argName(i).equals("nmea_out")) {
      settings->nmea_out = server.arg(i).toInt();
    } else if (server.argName(i).equals("gdl90")) {
      settings->gdl90 = server.arg(i).toInt();
    } else if (server.argName(i).equals("d1090")) {
      settings->d1090 = server.arg(i).toInt();
    } else if (server.argName(i).equals("stealth")) {
      settings->stealth = server.arg(i).toInt();
    } else if (server.argName(i).equals("no_track")) {
      settings->no_track = server.arg(i).toInt();
    } else if (server.argName(i).equals("power_save")) {
      settings->power_save = server.arg(i).toInt();
    }
  }
  snprintf_P ( Input_temp, 1520,
PSTR("<html>\
<head>\
<meta http-equiv='refresh' content='15; url=/'>\
<meta name='viewport' content='width=device-width, initial-scale=1'>\
<title>SoftRF Settings</title>\
</head>\
<body>\
<h1 align=center>New settings:</h1>\
<table width=100%%>\
<tr><th align=left>Mode</th><td align=right>%d</td></tr>\
<tr><th align=left>Protocol</th><td align=right>%d</td></tr>\
<tr><th align=left>Band</th><td align=right>%d</td></tr>\
<tr><th align=left>Aircraft type</th><td align=right>%d</td></tr>\
<tr><th align=left>Alarm trigger</th><td align=right>%d</td></tr>\
<tr><th align=left>Tx Power</th><td align=right>%d</td></tr>\
<tr><th align=left>Volume</th><td align=right>%d</td></tr>\
<tr><th align=left>LED pointer</th><td align=right>%d</td></tr>\
<tr><th align=left>Bluetooth</th><td align=right>%d</td></tr>\
<tr><th align=left>NMEA GNSS</th><td align=right>%s</td></tr>\
<tr><th align=left>NMEA Private</th><td align=right>%s</td></tr>\
<tr><th align=left>NMEA Legacy</th><td align=right>%s</td></tr>\
<tr><th align=left>NMEA Sensors</th><td align=right>%s</td></tr>\
<tr><th align=left>NMEA Out</th><td align=right>%d</td></tr>\
<tr><th align=left>GDL90</th><td align=right>%d</td></tr>\
<tr><th align=left>DUMP1090</th><td align=right>%d</td></tr>\
<tr><th align=left>Stealth</th><td align=right>%s</td></tr>\
<tr><th align=left>No track</th><td align=right>%s</td></tr>\
<tr><th align=left>Power save</th><td align=right>%d</td></tr>\
</table>\
<hr>\
  <p align=center><h1 align=center>Restart is in progress... Please, wait!</h1></p>\
</body>\
</html>"),
  settings->mode, settings->rf_protocol, settings->band,
  settings->aircraft_type, settings->alarm, settings->txpower,
  settings->volume, settings->pointer, settings->bluetooth,
  BOOL_STR(settings->nmea_g), BOOL_STR(settings->nmea_p),
  BOOL_STR(settings->nmea_l), BOOL_STR(settings->nmea_s),
  settings->nmea_out, settings->gdl90, settings->d1090,
  BOOL_STR(settings->stealth), BOOL_STR(settings->no_track),
  settings->power_save
  );
  SoC->swSer_enableRx(false);
  server.send ( 200, "text/html", Input_temp );
//  SoC->swSer_enableRx(true);
  delay(1000);
  free(Input_temp);
  EEPROM_store();
  RF_Shutdown();
  delay(1000);
  SoC->reset();
}

void handleNotFound() {

  String message = "File Not Found\n\n";
  message += "URI: ";
  message += server.uri();
  message += "\nMethod: ";
  message += ( server.method() == HTTP_GET ) ? "GET" : "POST";
  message += "\nArguments: ";
  message += server.args();
  message += "\n";

  for ( uint8_t i = 0; i < server.args(); i++ ) {
    message += " " + server.argName ( i ) + ": " + server.arg ( i ) + "\n";
  }

  server.send ( 404, "text/plain", message );
}

void Web_setup()
{
  server.on ( "/", handleRoot );
  server.on ( "/settings", handleSettings );
  server.on ( "/about", []() {
    SoC->swSer_enableRx(false);
    server.sendHeader(String(F("Cache-Control")), String(F("no-cache, no-store, must-revalidate")));
    server.sendHeader(String(F("Pragma")), String(F("no-cache")));
    server.sendHeader(String(F("Expires")), String(F("-1")));
    server.send_P ( 200, PSTR("text/html"), about_html);
    SoC->swSer_enableRx(true);
  } );

  server.on ( "/input", handleInput );
  server.on ( "/inline", []() {
    server.send ( 200, "text/plain", "this works as well" );
  } );
  server.on("/firmware", HTTP_GET, [](){
    SoC->swSer_enableRx(false);
    server.sendHeader(String(F("Connection")), String(F("close")));
    server.sendHeader(String(F("Access-Control-Allow-Origin")), String(F("*")));
    server.send_P(200,
      PSTR("text/html"),
      PSTR("\
<html>\
  <head>\
    <meta name='viewport' content='width=device-width, initial-scale=1'>\
    <title>Firmware update</title>\
    <p>ESP32: select SoftRF.ino.esp32.bin from software/firmware/source/SoftRF folder</p>\
  </head>\
<body>\
<body>\
 <h1 align=center>Firmware update</h1>\
 <hr>\
 <table width=100%%>\
  <tr>\
    <td align=left>\
<script src='/jquery.min.js'></script>\
<form method='POST' action='#' enctype='multipart/form-data' id='upload_form'>\
    <input type='file' name='update'>\
    <input type='submit' value='Update'>\
</form>\
<div id='prg'>progress: 0%</div>\
<script>\
$('form').submit(function(e){\
    e.preventDefault();\
      var form = $('#upload_form')[0];\
      var data = new FormData(form);\
       $.ajax({\
            url: '/update',\
            type: 'POST',\
            data: data,\
            contentType: false,\
            processData:false,\
            xhr: function() {\
                var xhr = new window.XMLHttpRequest();\
                xhr.upload.addEventListener('progress', function(evt) {\
                    if (evt.lengthComputable) {\
                        var per = evt.loaded / evt.total;\
                        $('#prg').html('progress: ' + Math.round(per*100) + '%');\
                    }\
               }, false);\
               return xhr;\
            },\
            success:function(d, s) {\
                console.log('success!')\
           },\
            error: function (a, b, c) {\
            }\
          });\
});\
</script>\
    </td>\
  </tr>\
 </table>\
</body>\
</html>")
    );
  SoC->swSer_enableRx(true);
  });
  server.onNotFound ( handleNotFound );

  server.on("/update", HTTP_POST, [](){
    SoC->swSer_enableRx(false);
    server.sendHeader(String(F("Connection")), String(F("close")));
    server.sendHeader(String(F("Access-Control-Allow-Origin")), "*");
    server.send(200, String(F("text/plain")), (Update.hasError())?"FAIL":"OK");
//    SoC->swSer_enableRx(true);
    RF_Shutdown();
    delay(1000);
    SoC->reset();
  },[](){
    HTTPUpload& upload = server.upload();
    if(upload.status == UPLOAD_FILE_START){
      Serial.setDebugOutput(true);
      SoC->WiFiUDP_stopAll();
      SoC->WDT_fini();
      Serial.printf("Update: %s\r\n", upload.filename.c_str());
      uint32_t maxSketchSpace = SoC->maxSketchSpace();
      if(!Update.begin(maxSketchSpace)){//start with max available size
        Update.printError(Serial);
      }
    } else if(upload.status == UPLOAD_FILE_WRITE){
      if(Update.write(upload.buf, upload.currentSize) != upload.currentSize){
        Update.printError(Serial);
      }
    } else if(upload.status == UPLOAD_FILE_END){
      if(Update.end(true)){ //true to set the size to the current progress
        Serial.printf("Update Success: %u\r\nRebooting...\r\n", upload.totalSize);
      } else {
        Update.printError(Serial);
      }
      Serial.setDebugOutput(false);
    }
    yield();
  });

  server.on ( "/logo.png", []() {
    server.send_P ( 200, "image/png", Logo, sizeof(Logo) );
  } );

  server.on ( "/jquery.min.js", []() {

    PGM_P content = jquery_min_js_gz;
    size_t bytes_left = jquery_min_js_gz_len;
    size_t chunk_size;

    server.setContentLength(bytes_left);
    server.sendHeader(String(F("Content-Encoding")),String(F("gzip")));
    server.send(200, String(F("application/javascript")), "");

    do {
      chunk_size = bytes_left > JS_MAX_CHUNK_SIZE ? JS_MAX_CHUNK_SIZE : bytes_left;
      server.sendContent_P(content, chunk_size);
      content += chunk_size;
      bytes_left -= chunk_size;
    } while (bytes_left > 0) ;

  } );

  server.begin();
  Serial.println (F("HTTP server has started at port: 80"));

  delay(1000);
}

void Web_loop()
{
  server.handleClient();
}

void Web_fini()
{
  server.stop();
}
