astir13/SoftRF/software/firmware/source/SoftRF/NMEAHelper.cpp

/*
 * NMEAHelper.cpp
 * Copyright (C) 2017-2020 Linar Yusupov
 *
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
 * You should have received a copy of the GNU General Public License
 * along with this program.  If not, see <http://www.gnu.org/licenses/>.
 */

#include <TimeLib.h>

#include "NMEAHelper.h"
#include "GNSSHelper.h"
#include "RFHelper.h"
#include "SoCHelper.h"
#include "WiFiHelper.h"
#include "EEPROMHelper.h"
#include "TrafficHelper.h"

#define ADDR_TO_HEX_STR(s, c) (s += ((c) < 0x10 ? "0" : "") + String((c), HEX))

#if defined(NMEA_TCP_SERVICE)
WiFiServer NmeaTCPServer(NMEA_TCP_PORT);
NmeaTCP_t NmeaTCP[MAX_NMEATCP_CLIENTS];
#endif

char NMEABuffer[NMEA_BUFFER_SIZE]; //buffer for NMEA data

static char NMEA_Callsign[NMEA_CALLSIGN_SIZE];

#if defined(USE_NMEALIB)
#include <nmealib.h>

NmeaMallocedBuffer nmealib_buf;
#endif /* USE_NMEALIB */

const char *NMEA_CallSign_Prefix[] = {
  [RF_PROTOCOL_LEGACY]    = "FLR",
  [RF_PROTOCOL_OGNTP]     = "OGN",
  [RF_PROTOCOL_P3I]       = "PAW",
  [RF_PROTOCOL_ADSB_1090] = "ADS",
  [RF_PROTOCOL_ADSB_UAT]  = "UAT",
  [RF_PROTOCOL_FANET]     = "FAN"
};

#define isTimeToPFLAV() (millis() - PFLAV_TimeMarker > 10000) /* PFLAV all 10 seconds */
unsigned long PFLAV_TimeMarker = 0;

#define isTimeToPGRMZ() (millis() - PGRMZ_TimeMarker > 1000)
unsigned long PGRMZ_TimeMarker = 0;

extern uint32_t tx_packets_counter, rx_packets_counter;

#if defined(ENABLE_AHRS)
#include "AHRSHelper.h"

#define isTimeToRPYL()  (millis() - RPYL_TimeMarker > AHRS_INTERVAL)
unsigned long RPYL_TimeMarker = 0;
#endif /* ENABLE_AHRS */

static char *ltrim(char *s)
{
  if(s) {
    while(*s && isspace(*s))
      ++s;
  }

  return s;
}

void NMEA_add_checksum(char *buf, size_t limit)
{
  size_t sentence_size = strlen(buf);

  //calculate the checksum
  unsigned char cs = 0;
  for (unsigned int n = 1; n < sentence_size - 1; n++) {
    cs ^= buf[n];
  }

  char *csum_ptr = buf + sentence_size;
  snprintf_P(csum_ptr, limit, PSTR("%02X\r\n"), cs);
}

void NMEA_setup()
{
#if defined(NMEA_TCP_SERVICE)
  if (settings->nmea_out == NMEA_TCP) {
    NmeaTCPServer.begin();
    Serial.print(F("NMEA TCP server has started at port: "));
    Serial.println(NMEA_TCP_PORT);

    NmeaTCPServer.setNoDelay(true);
  }
#endif /* NMEA_TCP_SERVICE */

#if defined(USE_NMEALIB)
  memset(&nmealib_buf, 0, sizeof(nmealib_buf));
#endif /* USE_NMEALIB */

  PGRMZ_TimeMarker = millis();

#if defined(ENABLE_AHRS)
  RPYL_TimeMarker = millis();
#endif /* ENABLE_AHRS */
}

void NMEA_loop()
{

  if (settings->nmea_s && ThisAircraft.pressure_altitude != 0.0 && isTimeToPGRMZ()) {

    int altitude = constrain(
            (int) (ThisAircraft.pressure_altitude * _GPS_FEET_PER_METER),
            -1000, 60000);

    snprintf_P(NMEABuffer, sizeof(NMEABuffer), PSTR("$PGRMZ,%d,f,3*"),
            altitude ); /* feet , 3D fix */

    NMEA_add_checksum(NMEABuffer, sizeof(NMEABuffer) - strlen(NMEABuffer));

    NMEA_Out((byte *) NMEABuffer, strlen(NMEABuffer), false);

    PGRMZ_TimeMarker = millis();
  }

  if (isTimeToPFLAV()) {
    snprintf_P(NMEABuffer, sizeof(NMEABuffer), PSTR("$PFLAV,A,2.00,6.82,*")); /* FLARM ver. 6.82 faked */
    NMEA_add_checksum(NMEABuffer, sizeof(NMEABuffer) - strlen(NMEABuffer));
    NMEA_Out((byte *) NMEABuffer, strlen(NMEABuffer), false);
    snprintf_P(NMEABuffer, sizeof(NMEABuffer), PSTR("$PFLAE,A,0,0*")); /* FLARM no problem detected */
    NMEA_add_checksum(NMEABuffer, sizeof(NMEABuffer) - strlen(NMEABuffer));
    NMEA_Out((byte *) NMEABuffer, strlen(NMEABuffer), false);
    snprintf_P(NMEABuffer, sizeof(NMEABuffer), PSTR("$PFLAC,A,HWVER,Prime2*")); /* FLARM HW VER */
    NMEA_add_checksum(NMEABuffer, sizeof(NMEABuffer) - strlen(NMEABuffer));
    NMEA_Out((byte *) NMEABuffer, strlen(NMEABuffer), false);
    snprintf_P(NMEABuffer, sizeof(NMEABuffer), PSTR("$PFLAC,A,SWVER,6.82*")); /* FLARM SW VER */
    NMEA_add_checksum(NMEABuffer, sizeof(NMEABuffer) - strlen(NMEABuffer));
    NMEA_Out((byte *) NMEABuffer, strlen(NMEABuffer), false);
    snprintf_P(NMEABuffer, sizeof(NMEABuffer), PSTR("$PFLAC,A,SER,01211*")); /* FLARM SERIAL NR. */
    NMEA_add_checksum(NMEABuffer, sizeof(NMEABuffer) - strlen(NMEABuffer));
    NMEA_Out((byte *) NMEABuffer, strlen(NMEABuffer), false);
    snprintf_P(NMEABuffer, sizeof(NMEABuffer), PSTR("$PFLAC,A,ID,123456*")); /* FLARM ID */
    NMEA_add_checksum(NMEABuffer, sizeof(NMEABuffer) - strlen(NMEABuffer));
    NMEA_Out((byte *) NMEABuffer, strlen(NMEABuffer), false);
    PFLAV_TimeMarker = millis();
  }

#if defined(ENABLE_AHRS)
  if (settings->nmea_s && isTimeToRPYL()) {

    AHRS_NMEA();

    RPYL_TimeMarker = millis();
  }
#endif /* ENABLE_AHRS */

#if defined(NMEA_TCP_SERVICE)
  uint8_t i;

  if (settings->nmea_out == NMEA_TCP) {

    if (NmeaTCPServer.hasClient()) {
      for(i = 0; i < MAX_NMEATCP_CLIENTS; i++) {
        // find free/disconnected spot
        if (!NmeaTCP[i].client || !NmeaTCP[i].client.connected()) {
          if(NmeaTCP[i].client) {
            NmeaTCP[i].client.stop();
            NmeaTCP[i].connect_ts = 0;
          }
          NmeaTCP[i].client = NmeaTCPServer.available();
          NmeaTCP[i].connect_ts = now();
          NmeaTCP[i].ack = false;
          NmeaTCP[i].client.print(F("PASS?"));
          break;
        }
      }
      if (i >= MAX_NMEATCP_CLIENTS) {
        // no free/disconnected spot so reject
        NmeaTCPServer.available().stop();
      }
    }

    for (i = 0; i < MAX_NMEATCP_CLIENTS; i++) {
      if (NmeaTCP[i].client && NmeaTCP[i].client.connected() &&
         !NmeaTCP[i].ack && NmeaTCP[i].connect_ts > 0 &&
         (now() - NmeaTCP[i].connect_ts) >= NMEATCP_ACK_TIMEOUT) {

          /* Clean TCP input buffer from any pass codes sent by client */
          while (NmeaTCP[i].client.available()) {
            char c = NmeaTCP[i].client.read();
            yield();
          }
          /* send acknowledge */
          NmeaTCP[i].client.print(F("AOK"));
          NmeaTCP[i].ack = true;
      }
    }
  }
#endif
}

void NMEA_fini()
{
#if defined(NMEA_TCP_SERVICE)
  if (settings->nmea_out == NMEA_TCP) {
    NmeaTCPServer.stop();
  }
#endif /* NMEA_TCP_SERVICE */
}

void NMEA_Out(byte *buf, size_t size, bool nl)
{
  switch(settings->nmea_out)
  {
  case NMEA_UART:
    {
      SerialOutput.write(buf, size);
      if (nl)
        SerialOutput.write('\n');
    }
    break;
  case NMEA_UART_BT:
    {
      SerialOutput.write(buf, size);
      if (nl)
        SerialOutput.write('\n');
    }
    if (SoC->Bluetooth) {
      SoC->Bluetooth->write(buf, size);
      if (nl)
        SoC->Bluetooth->write((byte *) "\n", 1);
    }
    break;
  case NMEA_UDP:
    {
      size_t udp_size = size;

      if (size >= sizeof(UDPpacketBuffer))
        udp_size = sizeof(UDPpacketBuffer) - 1;
      memcpy(UDPpacketBuffer, buf, udp_size);

      if (nl)
        UDPpacketBuffer[udp_size] = '\n';

      SoC->WiFi_transmit_UDP(NMEA_UDP_PORT, (byte *) UDPpacketBuffer,
                              nl ? udp_size + 1 : udp_size);
    }
    break;
  case NMEA_TCP:
    {
#if defined(NMEA_TCP_SERVICE)
      for (uint8_t acc_ndx = 0; acc_ndx < MAX_NMEATCP_CLIENTS; acc_ndx++) {
        if (NmeaTCP[acc_ndx].client && NmeaTCP[acc_ndx].client.connected()){
          if (NmeaTCP[acc_ndx].ack) {
            NmeaTCP[acc_ndx].client.write(buf, size);
            if (nl)
              NmeaTCP[acc_ndx].client.write('\n');
          }
        }
      }
#endif
    }
    break;
  case NMEA_BLUETOOTH:
    {
      if (SoC->Bluetooth) {
        SoC->Bluetooth->write(buf, size);
        if (nl)
          SoC->Bluetooth->write((byte *) "\n", 1);
      }
    }
    break;
  case NMEA_OFF:
  default:
    break;
  }
}

void NMEA_Export()
{
    int bearing;
    int alt_diff;
    float distance;

    int total_objects = 0;
    int alarm_level = ALARM_LEVEL_NONE;
    time_t this_moment = now();

    /* High priority object (most relevant target) */
    int HP_bearing = 0;
    int HP_alt_diff = 0;
    int HP_alarm_level = ALARM_LEVEL_NONE;
    float HP_distance = 2147483647;
    uint32_t HP_addr = 0;

    bool has_Fix = isValidFix() || (settings->mode == SOFTRF_MODE_TXRX_TEST);

    if (has_Fix) {
      for (int i=0; i < MAX_TRACKING_OBJECTS; i++) {
        if (Container[i].addr && (this_moment - Container[i].timestamp) <= EXPORT_EXPIRATION_TIME) {

#if 0
          Serial.println(fo.addr);
          Serial.println(fo.latitude, 4);
          Serial.println(fo.longitude, 4);
          Serial.println(fo.altitude);
          Serial.println(fo.addr_type);
          Serial.println(fo.vs);
          Serial.println(fo.aircraft_type);
          Serial.println(fo.stealth);
          Serial.println(fo.no_track);
#endif
          if (settings->nmea_l) {
            distance = Container[i].distance;

            if (distance < ALARM_ZONE_NONE) {

              total_objects++;

              char str_climb_rate[8] = "";
              uint8_t addr_type = Container[i].addr_type > ADDR_TYPE_ANONYMOUS ?
                                  ADDR_TYPE_ANONYMOUS : Container[i].addr_type;

              bearing = Container[i].bearing;
              alarm_level = Container[i].alarm_level;
              alt_diff = (int) (Container[i].altitude - ThisAircraft.altitude);

              if (!Container[i].stealth && !ThisAircraft.stealth) {
                dtostrf(
                  constrain(Container[i].vs / (_GPS_FEET_PER_METER * 60.0), -32.7, 32.7),
                  5, 1, str_climb_rate);
              }

              /*
               * When callsign is available - send it to a NMEA client.
               * If it is not - generate a callsign substitute,
               * based upon a protocol ID and the ICAO address
               */
              memset((void *) NMEA_Callsign, 0, sizeof(NMEA_Callsign));

              if (strnlen((char *) Container[i].callsign, sizeof(Container[i].callsign)) > 0) {
                memcpy(NMEA_Callsign, Container[i].callsign, sizeof(Container[i].callsign));
              } else {
                memcpy(NMEA_Callsign, NMEA_CallSign_Prefix[Container[i].protocol],
                  strlen(NMEA_CallSign_Prefix[Container[i].protocol]));

                String str = "_";

                ADDR_TO_HEX_STR(str, (Container[i].addr >> 16) & 0xFF);
                ADDR_TO_HEX_STR(str, (Container[i].addr >>  8) & 0xFF);
                ADDR_TO_HEX_STR(str, (Container[i].addr      ) & 0xFF);

                str.toUpperCase();
                memcpy(NMEA_Callsign + strlen(NMEA_CallSign_Prefix[Container[i].protocol]),
                  str.c_str(), str.length());
              }

              snprintf_P(NMEABuffer, sizeof(NMEABuffer), PSTR("$PFLAA,%d,%d,%d,%d,%d,%06X!%s,%d,,%d,%s,%d*"),
                      alarm_level,
                      (int) (distance * cos(radians(bearing))), (int) (distance * sin(radians(bearing))),
                      alt_diff, addr_type, Container[i].addr, NMEA_Callsign,
                      (int) Container[i].course, (int) (Container[i].speed * _GPS_MPS_PER_KNOT),
                      ltrim(str_climb_rate), Container[i].aircraft_type);

              NMEA_add_checksum(NMEABuffer, sizeof(NMEABuffer) - strlen(NMEABuffer));

              NMEA_Out((byte *) NMEABuffer, strlen(NMEABuffer), false);

              /* Most close traffic is treated as highest priority target */
              if (distance < HP_distance) {
                HP_bearing = bearing;
                HP_alt_diff = alt_diff;
                HP_alarm_level = alarm_level;
                HP_distance = distance;
                HP_addr = Container[i].addr;
              }

            }
          }
        }
      }
    }

    /* One PFLAU NMEA sentence is mandatory regardless of traffic reception status */
    if (settings->nmea_l) {

      if (total_objects > 0) {
        HP_bearing = HP_bearing - ThisAircraft.course;  // relative bearing to our own needed for ext. display (i.e. FLARM display)
        HP_bearing > 0 ? HP_bearing : HP_bearing + 360;
        snprintf_P(NMEABuffer, sizeof(NMEABuffer),
                PSTR("$PFLAU,%d,%d,%d,%d,%d,%d,%d,%d,%u,%06X" PFLAU_EXT1_FMT "*"),
                total_objects,
                settings->txpower == RF_TX_POWER_OFF ? TX_STATUS_OFF : TX_STATUS_ON,
                GNSS_STATUS_3D_MOVING,
                POWER_STATUS_GOOD, HP_alarm_level,
                (HP_bearing < 180 ? HP_bearing : HP_bearing - 360),
                ALARM_TYPE_AIRCRAFT, HP_alt_diff, (int) HP_distance, HP_addr
                PFLAU_EXT1_ARGS );
      } else {
        snprintf_P(NMEABuffer, sizeof(NMEABuffer),
                PSTR("$PFLAU,0,%d,%d,%d,%d,,0,,," PFLAU_EXT1_FMT "*"),
                has_Fix && (settings->txpower != RF_TX_POWER_OFF) ?
                  TX_STATUS_ON : TX_STATUS_OFF,
                has_Fix ? GNSS_STATUS_3D_MOVING : GNSS_STATUS_NONE,
                POWER_STATUS_GOOD, HP_alarm_level
                PFLAU_EXT1_ARGS );
      }

      NMEA_add_checksum(NMEABuffer, sizeof(NMEABuffer) - strlen(NMEABuffer));

      NMEA_Out((byte *) NMEABuffer, strlen(NMEABuffer), false);
    }
}

#if defined(USE_NMEALIB)

void NMEA_Position()
{
  NmeaInfo info;
  size_t i;
  struct timeval tv;

  if (settings->nmea_g) {

    nmeaInfoClear(&info);

    info.sig = NMEALIB_SIG_SENSITIVE;
    info.fix = NMEALIB_FIX_3D;

    tv.tv_sec  = ThisAircraft.timestamp;
    tv.tv_usec = 0;

    nmeaTimeSet(&info.utc, &info.present, &tv);

    info.latitude = ((int) ThisAircraft.latitude) * 100.0;
    info.latitude += (ThisAircraft.latitude - (int) ThisAircraft.latitude) * 60.0;
    info.longitude = ((int) ThisAircraft.longitude) * 100.0;
    info.longitude += (ThisAircraft.longitude - (int) ThisAircraft.longitude) * 60.0;
    info.speed = ThisAircraft.speed * _GPS_KMPH_PER_KNOT;
    info.elevation = ThisAircraft.altitude; /* above MSL */
    info.height = LookupSeparation(ThisAircraft.latitude, ThisAircraft.longitude);
    info.track = ThisAircraft.course;

#if 0
    info.mtrack = 55;
    info.magvar = 55;
#endif
    info.hdop = 2.3;
    info.vdop = 1.2;
    info.pdop = 2.594224354;

    nmeaInfoSetPresent(&info.present, NMEALIB_PRESENT_SIG);
    nmeaInfoSetPresent(&info.present, NMEALIB_PRESENT_FIX);
    nmeaInfoSetPresent(&info.present, NMEALIB_PRESENT_LAT);
    nmeaInfoSetPresent(&info.present, NMEALIB_PRESENT_LON);
    nmeaInfoSetPresent(&info.present, NMEALIB_PRESENT_SPEED);
    nmeaInfoSetPresent(&info.present, NMEALIB_PRESENT_ELV);
    nmeaInfoSetPresent(&info.present, NMEALIB_PRESENT_HEIGHT);

    nmeaInfoSetPresent(&info.present, NMEALIB_PRESENT_TRACK);
#if 0
    nmeaInfoSetPresent(&info.present, NMEALIB_PRESENT_MTRACK);
    nmeaInfoSetPresent(&info.present, NMEALIB_PRESENT_MAGVAR);
#endif
    nmeaInfoSetPresent(&info.present, NMEALIB_PRESENT_HDOP);
    nmeaInfoSetPresent(&info.present, NMEALIB_PRESENT_VDOP);
    nmeaInfoSetPresent(&info.present, NMEALIB_PRESENT_PDOP);

#if 0
    info.satellites.inUseCount = NMEALIB_MAX_SATELLITES;
    nmeaInfoSetPresent(&info.present, NMEALIB_PRESENT_SATINUSECOUNT);
    for (i = 0; i < NMEALIB_MAX_SATELLITES; i++) {
      info.satellites.inUse[i] = (unsigned int) (i + 1);
    }
    nmeaInfoSetPresent(&info.present, NMEALIB_PRESENT_SATINUSE);

    info.satellites.inViewCount = NMEALIB_MAX_SATELLITES;
    for (i = 0; i < NMEALIB_MAX_SATELLITES; i++) {
      info.satellites.inView[i].prn = (unsigned int) i + 1;
      info.satellites.inView[i].elevation = (int) ((i * 10) % 90);
      info.satellites.inView[i].azimuth = (unsigned int) (i + 1);
      info.satellites.inView[i].snr = 99 - (unsigned int) i;
    }
    nmeaInfoSetPresent(&info.present, NMEALIB_PRESENT_SATINVIEWCOUNT);
    nmeaInfoSetPresent(&info.present, NMEALIB_PRESENT_SATINVIEW);
#endif

    size_t gen_sz = nmeaSentenceFromInfo(&nmealib_buf, &info, (NmeaSentence)
      (NMEALIB_SENTENCE_GPGGA | NMEALIB_SENTENCE_GPGSA | NMEALIB_SENTENCE_GPRMC));

    if (gen_sz) {
      NMEA_Out((byte *) nmealib_buf.buffer, gen_sz, false);
    }
  }
}

void NMEA_GGA()
{
  NmeaInfo info;

  float latitude = gnss.location.lat();
  float longitude = gnss.location.lng();

  nmeaInfoClear(&info);

  info.utc.hour = gnss.time.hour();
  info.utc.min = gnss.time.minute();
  info.utc.sec = gnss.time.second();
  info.utc.hsec = gnss.time.centisecond();

  info.latitude = ((int) latitude) * 100.0;
  info.latitude += (latitude - (int) latitude) * 60.0;
  info.longitude = ((int) longitude) * 100.0;
  info.longitude += (longitude - (int) longitude) * 60.0;

  info.sig = (NmeaSignal) gnss.location.Quality();
  info.satellites.inViewCount = gnss.satellites.value();

  info.hdop = gnss.hdop.hdop();

  info.elevation = gnss.altitude.meters(); /* above MSL */
  info.height = gnss.separation.meters();

  if (info.height == 0.0 && info.sig != (NmeaSignal) Invalid) {
    info.height = LookupSeparation(latitude, longitude);
    info.elevation -= info.height;
  }

  nmeaInfoSetPresent(&info.present, NMEALIB_PRESENT_UTCTIME);
  nmeaInfoSetPresent(&info.present, NMEALIB_PRESENT_LAT);
  nmeaInfoSetPresent(&info.present, NMEALIB_PRESENT_LON);
  nmeaInfoSetPresent(&info.present, NMEALIB_PRESENT_SIG);
  /* Should be SATINUSECOUNT, but it seems to be a bug in NMEALib */
  nmeaInfoSetPresent(&info.present, NMEALIB_PRESENT_SATINVIEWCOUNT);
  nmeaInfoSetPresent(&info.present, NMEALIB_PRESENT_HDOP);
  nmeaInfoSetPresent(&info.present, NMEALIB_PRESENT_ELV);
  nmeaInfoSetPresent(&info.present, NMEALIB_PRESENT_HEIGHT);

  size_t gen_sz = nmeaSentenceFromInfo(&nmealib_buf, &info, (NmeaSentence)
                                        NMEALIB_SENTENCE_GPGGA );

  if (gen_sz) {
    NMEA_Out((byte *) nmealib_buf.buffer, gen_sz, false);
  }
}

#endif /* USE_NMEALIB */
