astir13/SoftRF/software/firmware/source/SoftRF/GNSSHelper.cpp

/*
 * GNSSHelper.cpp
 * Copyright (C) 2016-2020 Linar Yusupov
 *
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
 * You should have received a copy of the GNU General Public License
 * along with this program.  If not, see <http://www.gnu.org/licenses/>.
 */

#if defined(ARDUINO)
#include <Arduino.h>
#endif
#include <TimeLib.h>

#include "GNSSHelper.h"
#include "EEPROMHelper.h"
#include "NMEAHelper.h"
#include "SoCHelper.h"
#include "WiFiHelper.h"
#include "RFHelper.h"

#include "SoftRF.h"

#include <egm96s.h>

#if !defined(DO_GNSS_DEBUG)
#define GNSS_DEBUG_PRINT
#define GNSS_DEBUG_PRINTLN
#else
#define GNSS_DEBUG_PRINT    Serial.print
#define GNSS_DEBUG_PRINTLN  Serial.println
#endif

unsigned long GNSSTimeSyncMarker = 0;
volatile unsigned long PPS_TimeMarker = 0;

#if 0
unsigned long GGA_Start_Time_Marker = 0;
unsigned long GGA_Stop_Time_Marker = 0;
#endif

boolean gnss_set_sucess = false ;
TinyGPSPlus gnss;  // Create an Instance of the TinyGPS++ object called gnss

uint8_t GNSSbuf[250]; // at least 3 lines of 80 characters each
                      // and 40+30*N bytes for "UBX-MON-VER" payload
int GNSS_cnt = 0;

 /* CFG-MSG */
const uint8_t setGLL[] PROGMEM = {0xF0, 0x01, 0x00, 0x00, 0x00, 0x00, 0x00, 0x01};
const uint8_t setGSV[] PROGMEM = {0xF0, 0x03, 0x00, 0x00, 0x00, 0x00, 0x00, 0x01};
const uint8_t setVTG[] PROGMEM = {0xF0, 0x05, 0x00, 0x00, 0x00, 0x00, 0x00, 0x01};
#if !defined(NMEA_TCP_SERVICE)
const uint8_t setGSA[] PROGMEM = {0xF0, 0x02, 0x00, 0x00, 0x00, 0x00, 0x00, 0x01};
#endif
 /* CFG-PRT */
uint8_t setBR[] = {0x01, 0x00, 0x00, 0x00, 0xD0, 0x08, 0x00, 0x00, 0x00, 0x96,
                   0x00, 0x00, 0x07, 0x00, 0x03, 0x00, 0x00, 0x00, 0x00, 0x00};

const uint8_t setNav5[] PROGMEM = {0xFF, 0xFF, 0x07, 0x03, 0x00, 0x00, 0x00, 0x00,
                                   0x10, 0x27, 0x00, 0x00, 0x05, 0x00, 0xFA, 0x00,
                                   0xFA, 0x00, 0x64, 0x00, 0x2C, 0x01, 0x00, 0x00,
                                   0x00, 0x00, 0x00, 0x00, 0x00, 0x00, 0x00, 0x00,
                                   0x00, 0x00, 0x00, 0x00};

const uint8_t CFG_RST[12]   PROGMEM = {0xb5, 0x62, 0x06, 0x04, 0x04, 0x00, 0x00,
                                       0x00, 0x01, 0x00, 0x0F, 0x66};

const uint8_t RXM_PMREQ[16] PROGMEM = {0xb5, 0x62, 0x02, 0x41, 0x08, 0x00, 0x00,
                                       0x00, 0x00, 0x00, 0x02, 0x00, 0x00, 0x00,
                                       0x4d, 0x3b};

const char *GNSS_name[] = {
  [GNSS_MODULE_NONE]    = "NONE",
  [GNSS_MODULE_NMEA]    = "NMEA",
  [GNSS_MODULE_U6]      = "U6",
  [GNSS_MODULE_U7]      = "U7",
  [GNSS_MODULE_U8]      = "U8",
  [GNSS_MODULE_U9]      = "U9",
  [GNSS_MODULE_MAV]     = "MAV",
  [GNSS_MODULE_S7XG]    = "S7XG"
};

#if defined(USE_NMEA_CFG)

#include "RFHelper.h"       /* RF_Shutdown() */
#include "SoundHelper.h"
#include "LEDHelper.h"
#include "GDL90Helper.h"
#include "D1090Helper.h"

TinyGPSCustom C_Version      (gnss, "PSRFC", 1);
TinyGPSCustom C_Mode         (gnss, "PSRFC", 2);
TinyGPSCustom C_Protocol     (gnss, "PSRFC", 3);
TinyGPSCustom C_Band         (gnss, "PSRFC", 4);
TinyGPSCustom C_AcftType     (gnss, "PSRFC", 5);
TinyGPSCustom C_Alarm        (gnss, "PSRFC", 6);
TinyGPSCustom C_TxPower      (gnss, "PSRFC", 7);
TinyGPSCustom C_Volume       (gnss, "PSRFC", 8);
TinyGPSCustom C_Pointer      (gnss, "PSRFC", 9);
TinyGPSCustom C_NMEA_gnss    (gnss, "PSRFC", 10);
TinyGPSCustom C_NMEA_private (gnss, "PSRFC", 11);
TinyGPSCustom C_NMEA_legacy  (gnss, "PSRFC", 12);
TinyGPSCustom C_NMEA_sensors (gnss, "PSRFC", 13);
TinyGPSCustom C_NMEA_Output  (gnss, "PSRFC", 14);
TinyGPSCustom C_GDL90_Output (gnss, "PSRFC", 15);
TinyGPSCustom C_D1090_Output (gnss, "PSRFC", 16);
TinyGPSCustom C_Stealth      (gnss, "PSRFC", 17);
TinyGPSCustom C_noTrack      (gnss, "PSRFC", 18);

#endif /* USE_NMEA_CFG */

static uint8_t makeUBXCFG(uint8_t cl, uint8_t id, uint8_t msglen, const uint8_t *msg)
{
  if (msglen > (sizeof(GNSSbuf) - 8) ) {
    msglen = sizeof(GNSSbuf) - 8;
  }

  // Construct the UBX packet
  GNSSbuf[0] = 0xB5;   // header
  GNSSbuf[1] = 0x62;   // header
  GNSSbuf[2] = cl;  // class
  GNSSbuf[3] = id;     // id
  GNSSbuf[4] = msglen; // length
  GNSSbuf[5] = 0x00;

  GNSSbuf[6+msglen] = 0x00; // CK_A
  GNSSbuf[7+msglen] = 0x00; // CK_B

  for (int i = 2; i < 6; i++) {
    GNSSbuf[6+msglen] += GNSSbuf[i];
    GNSSbuf[7+msglen] += GNSSbuf[6+msglen];
  }

  for (int i = 0; i < msglen; i++) {
    GNSSbuf[6+i] = pgm_read_byte(&msg[i]);
    GNSSbuf[6+msglen] += GNSSbuf[6+i];
    GNSSbuf[7+msglen] += GNSSbuf[6+msglen];
  }
  return (msglen + 8);
}

// Send a byte array of UBX protocol to the GPS
static void sendUBX(const uint8_t *MSG, uint8_t len) {
  for (int i = 0; i < len; i++) {
    swSer.write( MSG[i]);
    GNSS_DEBUG_PRINT(MSG[i], HEX);
  }
//  swSer.println();
}

// Calculate expected UBX ACK packet and parse UBX response from GPS
static boolean getUBX_ACK(uint8_t cl, uint8_t id) {
  uint8_t b;
  uint8_t ackByteID = 0;
  uint8_t ackPacket[2] = {cl, id};
  unsigned long startTime = millis();
  GNSS_DEBUG_PRINT(F(" * Reading ACK response: "));

  // Construct the expected ACK packet
  makeUBXCFG(0x05, 0x01, 2, ackPacket);

  while (1) {

    // Test for success
    if (ackByteID > 9) {
      // All packets in order!
      GNSS_DEBUG_PRINTLN(F(" (SUCCESS!)"));
      return true;
    }

    // Timeout if no valid response in 2 seconds
    if (millis() - startTime > 2000) {
      GNSS_DEBUG_PRINTLN(F(" (FAILED!)"));
      return false;
    }

    // Make sure data is available to read
    if (swSer.available()) {
      b = swSer.read();

      // Check that bytes arrive in sequence as per expected ACK packet
      if (b == GNSSbuf[ackByteID]) {
        ackByteID++;
        GNSS_DEBUG_PRINT(b, HEX);
      }
      else {
        ackByteID = 0;  // Reset and look again, invalid order
      }
    }
    yield();
  }
}

static void setup_UBX()
{
  uint8_t msglen;

#if 0
  unsigned int baudrate = 38400;

  setBR[ 8] = (baudrate      ) & 0xFF;
  setBR[ 9] = (baudrate >>  8) & 0xFF;
  setBR[10] = (baudrate >> 16) & 0xFF;

  SoC->swSer_begin(9600);

  Serial.print(F("Switching baud rate onto "));
  Serial.println(baudrate);

  msglen = makeUBXCFG(0x06, 0x00, sizeof(setBR), setBR);
  sendUBX(GNSSbuf, msglen);
  gnss_set_sucess = getUBX_ACK(0x06, 0x00);

  if (!gnss_set_sucess) {
    Serial.print(F("WARNING: Unable to set baud rate onto "));
    Serial.println(baudrate); 
  }
  swSer.flush();
  SoC->swSer_begin(baudrate);
#endif

  GNSS_DEBUG_PRINTLN(F("Airborne <2g navigation mode: "));

  // Set the navigation mode (Airborne, < 2g)
  msglen = makeUBXCFG(0x06, 0x24, sizeof(setNav5), setNav5);
  sendUBX(GNSSbuf, msglen);
  gnss_set_sucess = getUBX_ACK(0x06, 0x24);

  if (!gnss_set_sucess) {
    GNSS_DEBUG_PRINTLN(F("WARNING: Unable to set airborne <2g navigation mode."));
  }

  GNSS_DEBUG_PRINTLN(F("Switching off NMEA GLL: "));

  msglen = makeUBXCFG(0x06, 0x01, sizeof(setGLL), setGLL);
  sendUBX(GNSSbuf, msglen);
  gnss_set_sucess = getUBX_ACK(0x06, 0x01);

  if (!gnss_set_sucess) {
    GNSS_DEBUG_PRINTLN(F("WARNING: Unable to disable NMEA GLL."));
  }

  GNSS_DEBUG_PRINTLN(F("Switching off NMEA GSV: "));

  msglen = makeUBXCFG(0x06, 0x01, sizeof(setGSV), setGSV);
  sendUBX(GNSSbuf, msglen);
  gnss_set_sucess = getUBX_ACK(0x06, 0x01);

  if (!gnss_set_sucess) {
    GNSS_DEBUG_PRINTLN(F("WARNING: Unable to disable NMEA GSV."));
  }

  GNSS_DEBUG_PRINTLN(F("Switching off NMEA VTG: "));

  msglen = makeUBXCFG(0x06, 0x01, sizeof(setVTG), setVTG);
  sendUBX(GNSSbuf, msglen);
  gnss_set_sucess = getUBX_ACK(0x06, 0x01);

  if (!gnss_set_sucess) {
    GNSS_DEBUG_PRINTLN(F("WARNING: Unable to disable NMEA VTG."));
  }

#if !defined(NMEA_TCP_SERVICE)

  GNSS_DEBUG_PRINTLN(F("Switching off NMEA GSA: "));

  msglen = makeUBXCFG(0x06, 0x01, sizeof(setGSA), setGSA);
  sendUBX(GNSSbuf, msglen);
  gnss_set_sucess = getUBX_ACK(0x06, 0x01);

  if (!gnss_set_sucess) {
    GNSS_DEBUG_PRINTLN(F("WARNING: Unable to disable NMEA GSA."));
  }

#endif
}

static void setup_NMEA()
{
#if 0
  swSer.write("$PUBX,41,1,0007,0003,9600,0*10\r\n");
  swSer.write("$PUBX,41,1,0007,0003,38400,0*20\r\n");

  swSer.flush();
  SoC->swSer_begin(38400);

  // Turning off some GPS NMEA strings on the uBlox modules
  swSer.write("$PUBX,40,GLL,0,0,0,0*5C\r\n"); delay(250);
  swSer.write("$PUBX,40,GSV,0,0,0,0*59\r\n"); delay(250);
  swSer.write("$PUBX,40,VTG,0,0,0,0*5E\r\n"); delay(250);
#if !defined(NMEA_TCP_SERVICE)
  swSer.write("$PUBX,40,GSA,0,0,0,0*4E\r\n"); delay(250);
#endif
#endif

#if defined(USE_AT6558_SETUP)
  /* Assume that we deal with fake NEO module (AT6558 based) */
  swSer.write("$PCAS04,5*1C\r\n"); /* GPS + GLONASS */     delay(250);
#if defined(NMEA_TCP_SERVICE)
  /* GGA,RMC and GSA */
  swSer.write("$PCAS03,1,0,1,0,1,0,0,0,0,0,,,0,0*03\r\n"); delay(250);
#else
  /* GGA and RMC */
  swSer.write("$PCAS03,1,0,0,0,1,0,0,0,0,0,,,0,0*02\r\n"); delay(250);
#endif
  swSer.write("$PCAS11,6*1B\r\n"); /* Aviation < 2g */     delay(250);
#endif /* USE_AT6558_SETUP */
}

/* ------ BEGIN -----------  https://github.com/Black-Thunder/FPV-Tracker */

enum ubloxState{ WAIT_SYNC1, WAIT_SYNC2, GET_CLASS, GET_ID, GET_LL, GET_LH, GET_DATA, GET_CKA, GET_CKB };

ubloxState ubloxProcessDataState = WAIT_SYNC1;

unsigned short ubloxExpectedDataLength;
unsigned short ubloxClass, ubloxId;
unsigned char  ubloxCKA, ubloxCKB;

// process serial data
// data is stored inside #GNSSbuf, data size inside #GNSS_cnt
// warning : if #GNSSbuf is too short, data is truncated.
static int ubloxProcessData(unsigned char data) {
	int parsed = 0;

	switch (ubloxProcessDataState) {
	case WAIT_SYNC1:
		if (data == 0xb5) {
			ubloxProcessDataState = WAIT_SYNC2;
		}
		break;

	case WAIT_SYNC2:
		if (data == 0x62) {
			ubloxProcessDataState = GET_CLASS;
		}
		else if (data == 0xb5) {
			// ubloxProcessDataState = GET_SYNC2;
		}
		else {
			ubloxProcessDataState = WAIT_SYNC1;
		}
		break;
	case GET_CLASS:
		ubloxClass = data;
		ubloxCKA = data;
		ubloxCKB = data;
		ubloxProcessDataState = GET_ID;
		break;

	case GET_ID:
		ubloxId = data;
		ubloxCKA += data;
		ubloxCKB += ubloxCKA;
		ubloxProcessDataState = GET_LL;
		break;

	case GET_LL:
		ubloxExpectedDataLength = data;
		ubloxCKA += data;
		ubloxCKB += ubloxCKA;
		ubloxProcessDataState = GET_LH;
		break;

	case GET_LH:
		ubloxExpectedDataLength += data << 8;
		GNSS_cnt = 0;
		ubloxCKA += data;
		ubloxCKB += ubloxCKA;
		ubloxProcessDataState = GET_DATA;
		break;

	case GET_DATA:
		ubloxCKA += data;
		ubloxCKB += ubloxCKA;
		if (GNSS_cnt < sizeof(GNSSbuf)) {
			GNSSbuf[GNSS_cnt++] = data;
		}
		if ((--ubloxExpectedDataLength) == 0) {
			ubloxProcessDataState = GET_CKA;
		}
		break;

	case GET_CKA:
		if (ubloxCKA != data) {
			ubloxProcessDataState = WAIT_SYNC1;
		}
		else {
			ubloxProcessDataState = GET_CKB;
		}
		break;

	case GET_CKB:
		if (ubloxCKB == data) {
			parsed = 1;
		}
		ubloxProcessDataState = WAIT_SYNC1;
		break;

	}

	return parsed;
}

/* ------ END -----------  https://github.com/Black-Thunder/FPV-Tracker */

static boolean GNSS_probe() {

  unsigned long startTime = millis();
  char c1, c2;
  c1 = c2 = 0;

  // clean any leftovers
  swSer.flush();

  // Serial.println(F("INFO: Waiting for NMEA data from GNSS module..."));

    // Timeout if no valid response in 3 seconds
  while (millis() - startTime < 3000) {

    if (swSer.available() > 0) {
      c1 = swSer.read();
      if ((c1 == '$') && (c2 == 0)) { c2 = c1; continue; }
      if ((c2 == '$') && (c1 == 'G')) {
        /* got $G */

        /* leave the function with GNSS port opened */
        return true;
      } else {
        c2 = 0;
      }
    }

    delay(1);
  }

  return false;
}

static byte GNSS_version() {
  byte rval = GNSS_MODULE_NMEA;
  unsigned long startTime = millis();

  uint8_t msglen = makeUBXCFG(0x0A, 0x04, 0, NULL); // MON-VER
  sendUBX(GNSSbuf, msglen);

  // Get the message back from the GPS
  GNSS_DEBUG_PRINT(F(" * Reading response: "));

  while ((millis() - startTime) < 2000 ) {

    if (swSer.available()) {
      unsigned char c = swSer.read();
      int ret = 0;

      GNSS_DEBUG_PRINT(c, HEX);
      ret = ubloxProcessData(c);

      // Upon a successfully parsed sentence, do the version detection
      if (ret) {

        if (ubloxClass == 0x0A) { // MON
          if (ubloxId == 0x04) {  // VER

            // UBX-MON-VER data description
            // uBlox 6  - page 166 : https://www.u-blox.com/sites/default/files/products/documents/u-blox6_ReceiverDescrProtSpec_%28GPS.G6-SW-10018%29_Public.pdf
            // uBlox 7  - page 153 : https://www.u-blox.com/sites/default/files/products/documents/u-blox7-V14_ReceiverDescriptionProtocolSpec_%28GPS.G7-SW-12001%29_Public.pdf
            // uBlox M8 - page 300 : https://www.u-blox.com/sites/default/files/products/documents/u-blox8-M8_ReceiverDescrProtSpec_%28UBX-13003221%29_Public.pdf

            Serial.print(F("INFO: GNSS module HW version: "));
            Serial.println((char *) &GNSSbuf[30]);

            Serial.print(F("INFO: GNSS module FW version: "));
            Serial.println((char *) &GNSSbuf[0]);

#ifdef DO_GNSS_DEBUG
            for(unsigned i = 30 + 10; i < GNSS_cnt; i+=30) {
              Serial.print(F("INFO: GNSS module extension: "));
              Serial.println((char *) &GNSSbuf[i]);
            }
#endif

            if (GNSSbuf[33] == '4')
              rval = GNSS_MODULE_U6;
            else if (GNSSbuf[33] == '7')
              rval = GNSS_MODULE_U7;
            else if (GNSSbuf[33] == '8')
              rval = GNSS_MODULE_U8;

            break;
          }
        }
      }
    }
  }

  return rval;
}

byte GNSS_setup() {

  byte rval = GNSS_MODULE_NONE;

  SoC->swSer_begin(SERIAL_IN_BR);

  if (!GNSS_probe())
    return rval;

  rval = GNSS_MODULE_NMEA;

  if (hw_info.model == SOFTRF_MODEL_PRIME_MK2 ||
      hw_info.model == SOFTRF_MODEL_RASPBERRY ) {

    rval = GNSS_version();

    if (rval == GNSS_MODULE_U6 ||
        rval == GNSS_MODULE_U7 ||
        rval == GNSS_MODULE_U8) {

      // Set the navigation mode (Airborne, 1G)
      // Turning off some GPS NMEA sentences on the uBlox modules
      setup_UBX();
    } else {
      setup_NMEA();
    }
  }

  if (SOC_GPIO_PIN_GNSS_PPS != SOC_UNUSED_PIN) {
    pinMode(SOC_GPIO_PIN_GNSS_PPS, SOC_GPIO_PIN_MODE_PULLDOWN);
    attachInterrupt(digitalPinToInterrupt(SOC_GPIO_PIN_GNSS_PPS),
                    SoC->GNSS_PPS_handler, RISING);
  }

  return rval;
}

void GNSS_fini()
{
  if (hw_info.model == SOFTRF_MODEL_PRIME_MK2) {
    if (hw_info.gnss == GNSS_MODULE_U6 ||
        hw_info.gnss == GNSS_MODULE_U7 ||
        hw_info.gnss == GNSS_MODULE_U8) {

      // Controlled Software reset
      for (int i = 0; i < sizeof(CFG_RST); i++) {
        swSer.write(pgm_read_byte(&CFG_RST[i]));
      }

      delay(600);

      // power off until wakeup call
      for (int i = 0; i < sizeof(RXM_PMREQ); i++) {
        swSer.write(pgm_read_byte(&RXM_PMREQ[i]));
      }
    }
  }
}

void GNSSTimeSync()
{
  if (GNSSTimeSyncMarker == 0 && gnss.time.isValid() && gnss.time.isUpdated()) {
      setTime(gnss.time.hour(), gnss.time.minute(), gnss.time.second(), gnss.date.day(), gnss.date.month(), gnss.date.year());
      GNSSTimeSyncMarker = millis();
  } else {

    if ((millis() - GNSSTimeSyncMarker > 60000) /* 1m */ && gnss.time.isValid() &&
        gnss.time.isUpdated() && (gnss.time.age() <= 1000) /* 1s */ ) {
  #if 0
      Serial.print("Valid: ");
      Serial.println(gnss.time.isValid());
      Serial.print("isUpdated: ");
      Serial.println(gnss.time.isUpdated());
      Serial.print("age: ");
      Serial.println(gnss.time.age());
  #endif
      setTime(gnss.time.hour(), gnss.time.minute(), gnss.time.second(), gnss.date.day(), gnss.date.month(), gnss.date.year());
      GNSSTimeSyncMarker = millis();
    }
  }
}

void PickGNSSFix()
{
  bool isValidSentence = false;
  int ndx;
  int c = -1;

  /*
   * Check SW, HW and BT UARTs for data
   * WARNING! Make use only one input source at a time.
   */
  while (true) {
#if !defined(USE_NMEA_CFG)
    if (swSer.available() > 0) {
      c = swSer.read();
    } else if (Serial.available() > 0) {
      c = Serial.read();
    } else if (SoC->Bluetooth && SoC->Bluetooth->available() > 0) {
      c = SoC->Bluetooth->read();

      /*
       * Don't forget to disable echo:
       *
       * stty raw -echo -F /dev/rfcomm0
       *
       * GNSS input becomes garbled otherwise
       */

      // Serial.write((char) c);
      /* Ignore Bluetooth input for a while */
      // break;
#else
    /*
     * Give priority to control channels on STM32-based
     * 'Dongle' and 'Retro' Editions
     */

    /* USB input is first */
    if (SoC->Bluetooth && SoC->Bluetooth->available() > 0) {
      c = SoC->Bluetooth->read();

#if 0
      /* This makes possible to configure S76x's built-in SONY GNSS from aside */
      if (hw_info.model == SOFTRF_MODEL_DONGLE) {
        swSer.write(c);
      }
#endif

    /* Serial input is second */
    } else if (SerialOutput.available() > 0) {
      c = SerialOutput.read();

    /* Built-in GNSS input */
    } else if (swSer.available() > 0) {
      c = swSer.read();
#endif /* USE_NMEA_CFG */
    } else {
      /* return back if no input data */
      break;
    }

    if (c == -1) {
      /* retry */
      continue;
    }

    if (isPrintable(c) || c == '\r' || c == '\n') {
      GNSSbuf[GNSS_cnt] = c;
    } else {
      /* ignore */
      continue;
    }
#if 0
    if ( (GNSS_cnt >= 5) &&
         (GNSSbuf[GNSS_cnt-5] == '$') &&
         (GNSSbuf[GNSS_cnt-4] == 'G') &&
        ((GNSSbuf[GNSS_cnt-3] == 'P') || (GNSSbuf[GNSS_cnt-3] == 'N')) &&
         (GNSSbuf[GNSS_cnt-2] == 'G') &&
         (GNSSbuf[GNSS_cnt-1] == 'G') &&
         (GNSSbuf[GNSS_cnt-0] == 'A')
       ) {
      GGA_Start_Time_Marker = millis();
    }
#endif

    isValidSentence = gnss.encode(GNSSbuf[GNSS_cnt]);
    if (settings->nmea_g && GNSSbuf[GNSS_cnt] == '\r' && isValidSentence) {
      for (ndx = GNSS_cnt - 4; ndx >= 0; ndx--) { // skip CS and *
        if ((GNSSbuf[ndx] == '$') && (GNSSbuf[ndx+1] == 'G')) {

          size_t write_size = GNSS_cnt - ndx + 1;

#if 0
          if (!strncmp((char *) &GNSSbuf[ndx+3], "GGA,", strlen("GGA,"))) {
            GGA_Stop_Time_Marker = millis();

            Serial.print("GGA Start: ");
            Serial.print(GGA_Start_Time_Marker);
            Serial.print(" Stop: ");
            Serial.print(GGA_Stop_Time_Marker);
            Serial.print(" gnss.time.age: ");
            Serial.println(gnss.time.age());

          }
#endif

          /*
           * Work around issue with "always 0.0,M" GGA geoid separation value
           * given by some Chinese GNSS chipsets
           */
#if defined(USE_NMEALIB)
          if (hw_info.model == SOFTRF_MODEL_PRIME_MK2 &&
              !strncmp((char *) &GNSSbuf[ndx+3], "GGA,", strlen("GGA,")) &&
              gnss.separation.meters() == 0.0) {
            NMEA_GGA();
          }
          else
#endif
          { // dump all GNSS sentences out to UART can be too much, avoid GSA and GSV
            //if (!((GNSSbuf[ndx+3] == 'G') && (GNSSbuf[ndx+4] == 'S'))) {
            NMEA_Out(&GNSSbuf[ndx], write_size, true);
            //}
          }

          break;
        }
      }
#if defined(USE_NMEA_CFG)
      if (C_Version.isUpdated()) {
        if (strncmp(C_Version.value(), "OFF", 3) == 0) {
          shutdown("  OFF  ");
        } else if (strncmp(C_Version.value(), "?", 1) == 0) {
          char psrfc_buf[MAX_PSRFC_LEN];

          snprintf_P(psrfc_buf, sizeof(psrfc_buf),
              PSTR("$PSRFC,%d,%d,%d,%d,%d,%d,%d,%d,%d,%d,%d,%d,%d,%d,%d,%d,%d,%d*"),
              PSRFC_VERSION, settings->mode, settings->rf_protocol,
              settings->band, settings->aircraft_type, settings->alarm,
              settings->txpower, BUZZER_OFF, LED_OFF,
              settings->nmea_g, settings->nmea_p, settings->nmea_l,
              settings->nmea_s, NMEA_UART, GDL90_OFF,
              D1090_OFF, settings->stealth, settings->no_track );

          NMEA_add_checksum(psrfc_buf, sizeof(psrfc_buf) - strlen(psrfc_buf));
          NMEA_Out((byte *) psrfc_buf, strlen(psrfc_buf), false);

        } else if (atoi(C_Version.value()) == PSRFC_VERSION) {
          bool cfg_is_updated = false;

          if (C_Mode.isUpdated())
          {
            settings->mode = atoi(C_Mode.value());
            Serial.print(F("Mode = ")); Serial.println(settings->mode);
            cfg_is_updated = true;
          }
          if (C_Protocol.isUpdated())
          {
            settings->rf_protocol = atoi(C_Protocol.value());
            Serial.print(F("Protocol = ")); Serial.println(settings->rf_protocol);
            cfg_is_updated = true;
          }
          if (C_Band.isUpdated())
          {
            settings->band = atoi(C_Band.value());
            Serial.print(F("Region = ")); Serial.println(settings->band);
            cfg_is_updated = true;
          }
          if (C_AcftType.isUpdated())
          {
            settings->aircraft_type = atoi(C_AcftType.value());
            Serial.print(F("AcftType = ")); Serial.println(settings->aircraft_type);
            cfg_is_updated = true;
          }
          if (C_Alarm.isUpdated())
          {
            settings->alarm = atoi(C_Alarm.value());
            Serial.print(F("Alarm = ")); Serial.println(settings->alarm);
            cfg_is_updated = true;
          }
          if (C_TxPower.isUpdated())
          {
            settings->txpower = atoi(C_TxPower.value());
            Serial.print(F("TxPower = ")); Serial.println(settings->txpower);
            cfg_is_updated = true;
          }
          if (C_Volume.isUpdated())
          {
            settings->volume = atoi(C_Volume.value());
            Serial.print(F("Volume = ")); Serial.println(settings->volume);
            cfg_is_updated = true;
          }
           if (C_Pointer.isUpdated())
          {
            settings->pointer = atoi(C_Pointer.value());
            Serial.print(F("Pointer = ")); Serial.println(settings->pointer);
            cfg_is_updated = true;
          }
          if (C_NMEA_gnss.isUpdated())
          {
            settings->nmea_g = atoi(C_NMEA_gnss.value());
            Serial.print(F("NMEA_gnss = ")); Serial.println(settings->nmea_g);
            cfg_is_updated = true;
          }
          if (C_NMEA_private.isUpdated())
          {
            settings->nmea_p = atoi(C_NMEA_private.value());
            Serial.print(F("NMEA_private = ")); Serial.println(settings->nmea_p);
            cfg_is_updated = true;
          }
          if (C_NMEA_legacy.isUpdated())
          {
            settings->nmea_l = atoi(C_NMEA_legacy.value());
            Serial.print(F("NMEA_legacy = ")); Serial.println(settings->nmea_l);
            cfg_is_updated = true;
          }
           if (C_NMEA_sensors.isUpdated())
          {
            settings->nmea_s = atoi(C_NMEA_sensors.value());
            Serial.print(F("NMEA_sensors = ")); Serial.println(settings->nmea_s);
            cfg_is_updated = true;
          }
          if (C_NMEA_Output.isUpdated())
          {
            settings->nmea_out = atoi(C_NMEA_Output.value());
            Serial.print(F("NMEA_Output = ")); Serial.println(settings->nmea_out);
            cfg_is_updated = true;
          }
          if (C_GDL90_Output.isUpdated())
          {
            settings->gdl90 = atoi(C_GDL90_Output.value());
            Serial.print(F("GDL90_Output = ")); Serial.println(settings->gdl90);
            cfg_is_updated = true;
          }
          if (C_D1090_Output.isUpdated())
          {
            settings->d1090 = atoi(C_D1090_Output.value());
            Serial.print(F("D1090_Output = ")); Serial.println(settings->d1090);
            cfg_is_updated = true;
          }
          if (C_Stealth.isUpdated())
          {
            settings->stealth = atoi(C_Stealth.value());
            Serial.print(F("Stealth = ")); Serial.println(settings->stealth);
            cfg_is_updated = true;
          }
          if (C_noTrack.isUpdated())
          {
            settings->no_track = atoi(C_noTrack.value());
            Serial.print(F("noTrack = ")); Serial.println(settings->no_track);
            cfg_is_updated = true;
          }

          if (cfg_is_updated) {
            SoC->WDT_fini();
            Serial.println();
            Serial.println(F("Restart is in progress. Please, wait..."));
            Serial.println();
            Serial.flush();
            EEPROM_store();
            RF_Shutdown();
            SoC->reset();
          }
        }
      }
#endif /* USE_NMEA_CFG */
    }
    if (GNSSbuf[GNSS_cnt] == '\n' || GNSS_cnt == sizeof(GNSSbuf)-1) {
      GNSS_cnt = 0;
    } else {
      GNSS_cnt++;
      yield();
    }
  }
}

/*
 *  Algorithm of EGM96 geoid offset approximation was taken from XCSoar
 */

static float AsBearing(float angle)
{
  float retval = angle;

  while (retval < 0)
    retval += 360.0;

  while (retval >= 360.0)
    retval -= 360.0;

  return retval;
}

int LookupSeparation(float lat, float lon)
{
  int ilat, ilon;

  ilat = round((90.0 - lat) / 2.0);
  ilon = round(AsBearing(lon) / 2.0);

  int offset = ilat * 180 + ilon;

  if (offset >= egm96s_dem_len)
    return 0;

  if (offset < 0)
    return 0;

  return (int) pgm_read_byte(&egm96s_dem[offset]) - 127;
}
