astir13/SoftRF/software/firmware/source/SoftRF/WiFiHelper.cpp

/*
 * WiFiHelper.cpp
 * Copyright (C) 2016-2020 Linar Yusupov
 *
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
 * You should have received a copy of the GNU General Public License
 * along with this program.  If not, see <http://www.gnu.org/licenses/>.
 */

#include <FS.h>
#include <TimeLib.h>

#include "OTAHelper.h"
#include "GNSSHelper.h"
#include "EEPROMHelper.h"
#include "SoCHelper.h"
#include "WiFiHelper.h"
#include "TrafficHelper.h"
#include "RFHelper.h"
#include "WebHelper.h"
#include "NMEAHelper.h"
#include "BatteryHelper.h"

String station_ssid = MY_ACCESSPOINT_SSID ;
String station_psk  = MY_ACCESSPOINT_PSK ;

String host_name = HOSTNAME;

IPAddress local_IP(192,168,111,1);
IPAddress gateway(192,168,111,1);
IPAddress subnet(255,255,255,0);

/**
 * Default WiFi connection information.
 *
 */
const char* ap_default_psk = "12345678"; ///< Default PSK.

#if defined(USE_DNS_SERVER)
#include <DNSServer.h>

const byte DNS_PORT = 53;
DNSServer dnsServer;
bool dns_active = false;
#endif

// A UDP instance to let us send and receive packets over UDP
WiFiUDP Uni_Udp;

unsigned int RFlocalPort = RELAY_SRC_PORT;      // local port to listen for UDP packets

char UDPpacketBuffer[256]; // buffer to hold incoming and outgoing packets

#if defined(POWER_SAVING_WIFI_TIMEOUT)
static unsigned long WiFi_No_Clients_Time_ms = 0;
#endif

/**
 * @brief Read WiFi connection information from file system.
 * @param ssid String pointer for storing SSID.
 * @param pass String pointer for storing PSK.
 * @return True or False.
 * 
 * The config file have to containt the WiFi SSID in the first line
 * and the WiFi PSK in the second line.
 * Line seperator can be \r\n (CR LF) \r or \n.
 */
bool loadConfig(String *ssid, String *pass)
{
  // open file for reading.
  File configFile = SPIFFS.open("/cl_conf.txt", "r");
  if (!configFile)
  {
    Serial.println(F("Failed to open cl_conf.txt."));

    return false;
  }

  // Read content from config file.
  String content = configFile.readString();
  configFile.close();

  content.trim();

  // Check if ther is a second line available.
  int8_t pos = content.indexOf("\r\n");
  uint8_t le = 2;
  // check for linux and mac line ending.
  if (pos == -1)
  {
    le = 1;
    pos = content.indexOf("\n");
    if (pos == -1)
    {
      pos = content.indexOf("\r");
    }
  }

  // If there is no second line: Some information is missing.
  if (pos == -1)
  {
    Serial.println(F("Invalid content."));
    Serial.println(content);

    return false;
  }

  // Store SSID and PSK into string vars.
  *ssid = content.substring(0, pos);
  *pass = content.substring(pos + le);

  ssid->trim();
  pass->trim();

#ifdef SERIAL_VERBOSE
  Serial.println("----- file content -----");
  Serial.println(content);
  Serial.println("----- file content -----");
  Serial.println("ssid: " + *ssid);
  Serial.println("psk:  " + *pass);
#endif

  return true;
} // loadConfig


/**
 * @brief Save WiFi SSID and PSK to configuration file.
 * @param ssid SSID as string pointer.
 * @param pass PSK as string pointer,
 * @return True or False.
 */
bool saveConfig(String *ssid, String *pass)
{
  // Open config file for writing.
  File configFile = SPIFFS.open("/cl_conf.txt", "w");
  if (!configFile)
  {
    Serial.println(F("Failed to open cl_conf.txt for writing"));

    return false;
  }

  // Save SSID and PSK.
  configFile.println(*ssid);
  configFile.println(*pass);

  configFile.close();

  return true;
} // saveConfig

size_t Raw_Receive_UDP(uint8_t *buf)
{
  int noBytes = Uni_Udp.parsePacket();
  if ( noBytes ) {

    if (noBytes > MAX_PKT_SIZE) {
      noBytes = MAX_PKT_SIZE;
    }

    // We've received a packet, read the data from it
    Uni_Udp.read(buf,noBytes); // read the packet into the buffer

    return (size_t) noBytes;
  } else {
    return 0;
  }
}

void Raw_Transmit_UDP()
{
    size_t rx_size = RF_Payload_Size(settings->rf_protocol);
    rx_size = rx_size > sizeof(fo.raw) ? sizeof(fo.raw) : rx_size;
    String str = Bin2Hex(fo.raw, rx_size);
    size_t len = str.length();
    // ASSERT(sizeof(UDPpacketBuffer) > 2 * PKT_SIZE + 1)
    str.toCharArray(UDPpacketBuffer, sizeof(UDPpacketBuffer));
    UDPpacketBuffer[len] = '\n';
    SoC->WiFi_transmit_UDP(RELAY_DST_PORT, (byte *)UDPpacketBuffer, len + 1);
}

/**
 * @brief Arduino setup function.
 */
void WiFi_setup()
{
#if 0
  // Initialize file system.
  if (!SPIFFS.begin())
  {
    Serial.println(F("Failed to mount file system"));
    return;
  }

  // Load wifi connection information.
  if (! loadConfig(&station_ssid, &station_psk))
  {
    station_ssid = MY_ACCESSPOINT_SSID ;
    station_psk = MY_ACCESSPOINT_PSK ;

    Serial.println(F("No WiFi connection information available."));
  }
#endif

  // Check WiFi connection
  // ... check mode
  if (WiFi.getMode() != WIFI_STA)
  {
    WiFi.mode(WIFI_STA);
    delay(10);
  }

  // ... Compare file config with sdk config.
  if (WiFi.SSID() != station_ssid || WiFi.psk() != station_psk)
  {
    Serial.println(F("WiFi config changed."));

    // ... Try to connect to WiFi station.
    WiFi.begin(station_ssid.c_str(), station_psk.c_str());

    // ... Pritn new SSID
    Serial.print(F("new SSID: "));
    Serial.println(WiFi.SSID());

    // ... Uncomment this for debugging output.
    //WiFi.printDiag(Serial);
  }
  else
  {
    // ... Begin with sdk config.
    WiFi.begin();
  }

  // Set Hostname.
  host_name += String((SoC->getChipId() & 0xFFFFFF), HEX);
  SoC->WiFi_hostname(host_name);

  // Print hostname.
  Serial.println("Hostname: " + host_name);

  Serial.println(F("Wait for WiFi connection."));

  // ... Give ESP 10 seconds to connect to station.
  unsigned long startTime = millis();
  while (WiFi.status() != WL_CONNECTED && millis() - startTime < 10000)
  {
    Serial.write('.');
    //Serial.print(WiFi.status());
    delay(500);
  }
  Serial.println();

  // Check connection
  if(WiFi.status() == WL_CONNECTED)
  {
    // ... print IP Address
    Serial.print(F("IP address: "));
    Serial.println(WiFi.localIP());
  }
  else
  {
    Serial.println(F("Can not connect to WiFi station. Go into AP mode."));
    
    // Go into software AP mode.
    WiFi.mode(WIFI_AP);
    SoC->WiFi_setOutputPower(WIFI_TX_POWER_MED); // 10 dB
    // WiFi.setOutputPower(0); // 0 dB
    //system_phy_set_max_tpw(4 * 0); // 0 dB
    delay(10);

    Serial.print(F("Setting soft-AP configuration ... "));
    Serial.println(WiFi.softAPConfig(local_IP, gateway, subnet) ?
      F("Ready") : F("Failed!"));

    Serial.print(F("Setting soft-AP ... "));
    Serial.println(WiFi.softAP(host_name.c_str(), ap_default_psk) ?
      F("Ready") : F("Failed!"));
#if defined(USE_DNS_SERVER)
    // if DNSServer is started with "*" for domain name, it will reply with
    // provided IP to all DNS request
    dnsServer.start(DNS_PORT, "*", WiFi.softAPIP());
    dns_active = true;
#endif
    Serial.print(F("IP address: "));
    Serial.println(WiFi.softAPIP());
  }

  Uni_Udp.begin(RFlocalPort);
  Serial.print(F("UDP server has started at port: "));
  Serial.println(RFlocalPort);

#if defined(POWER_SAVING_WIFI_TIMEOUT)
  WiFi_No_Clients_Time_ms = millis();
#endif
}

void WiFi_loop()
{
#if defined(USE_DNS_SERVER)
  if (dns_active) {
    dnsServer.processNextRequest();
  }
#endif

#if defined(POWER_SAVING_WIFI_TIMEOUT)
  if (settings->power_save == POWER_SAVE_WIFI && WiFi.getMode() == WIFI_AP) {
    if (SoC->WiFi_clients_count() == 0) {
      if ((millis() - WiFi_No_Clients_Time_ms) > POWER_SAVING_WIFI_TIMEOUT) {
        NMEA_fini();
        Web_fini();
        WiFi_fini();

        if (settings->nmea_p) {
          StdOut.println(F("$PSRFS,WIFI_OFF"));
        }
      }
    } else {
      WiFi_No_Clients_Time_ms = millis();
    }
  }
#endif
}

void WiFi_fini()
{
  Uni_Udp.stop();

  WiFi.mode(WIFI_OFF);
}
